SphaeroX/optimistic-hubble/.agents/swe_1/DISPATCH.md

## 2026-08-21T17:47:13Z

You are the SWE Light orchestrator for the task defined in ORIGINAL_REQUEST.md.

Project root: c:\Users\MGasc\Documents\antigravity\optimistic-hubble
Original request file: c:\Users\MGasc\Documents\antigravity\optimistic-hubble\.agents\ORIGINAL_REQUEST.md
Your working directory: c:\Users\MGasc\Documents\antigravity\optimistic-hubble\.agents\swe_1

Read ORIGINAL_REQUEST.md and execute the SWE Light implementation and review loop to fix the Android Wi-Fi SoftAP connection lifecycle, socket binding, and recording synchronization issue between Flutter and ESP32 SoftAP. Ensure all acceptance criteria are met and verified.

When complete, write your handoff.md and send a completion message back with your final summary.
