SphaeroX/optimistic-hubble/.agents/swe_1/progress.md

# Progress Tracking

## Iteration Status
Current iteration: 6 / 32

## Current Status
Last visited: 2026-08-21T20:11:15+02:00
- [x] Implementer pass (teamwork_preview_implementer - 139cbbd2-75ac-4e21-a6cd-302e5dc0f8cb completed)
- [x] Reviewer round 1 (teamwork_preview_reviewer - 05e17a85-e970-4b02-85ed-ecea45a1d87e completed)
- [x] Reviewer round 2 (teamwork_preview_reviewer - f65f6cd9-f0e1-40d8-a784-cee9b6a79a19 completed)
- [x] Reviewer round 3 (teamwork_preview_reviewer - c275563a-5b87-41f8-9933-3ed2bfb61a50 completed)
- [x] Orchestrator independent test verification (flutter analyze: 0 issues, flutter test: 10/10 passed, assembleDebug: BUILD SUCCESSFUL)
- [x] Victory audit (teamwork_preview_victory_auditor - 6c1af6c4-f39e-444e-9d3a-9c039cb8fe52 VICTORY CONFIRMED)
- [x] Handoff and completion reporting (swe_1/handoff.md written)

## Open Issues Ledger
- [x] Concurrency state transitions & atomic deferred binding (resolved in reviewer_3)
- [x] HTTP Range RFC 7233 206 vs 200 resume streaming (resolved in reviewer_3)
- [x] OkHttp socket/response leaks on error codes (resolved in reviewer_2)
- [x] Cooperative stream cancellation & clean event handling (resolved in reviewer_2)
- [x] NetworkCallback handle leaks on onLost/onUnavailable (resolved in reviewer_1)
- [x] SoftAP connection retention across batch transfers (resolved in implementer_1)
- [ ] Bench testing with live ESP32-C3 hardware running SoftAP firmware (hardware-dependent benchmark)
