SphaeroX/optimistic-hubble/.agents/teamwork_preview_victory_auditor_sentinel/progress.md

# Progress Log — Victory Auditor Sentinel

**Status**: Completed  
**Last visited**: 2026-08-21T18:14:30Z

## Completed Steps
- [x] Recorded inbound dispatch prompt in DISPATCH.md
- [x] Initialized and updated BRIEFING.md
- [x] Phase A: Timeline & Provenance Audit (verified commits, iterative progression, lack of pre-populated results)
- [x] Phase B: Integrity Check & Forensic Analysis (verified genuine socket routing, callback retention, batch sync lifecycle, absence of facade/cheating patterns)
- [x] Phase C: Independent Test & Build Verification (`flutter analyze` -> 0 issues, `flutter test` -> 10/10 pass, `.\gradlew.bat assembleDebug` -> SUCCESS, `flutter build apk --debug` -> SUCCESS)
- [x] Rendered structured VICTORY AUDIT REPORT in handoff.md
