SphaeroX/optimistic-hubble/.agents/implementer_1/handoff.md

# Implementer Handoff Report

> [!WARNING] **Skepticism Disclaimer**
> The implementation compiles cleanly against Android Gradle (assembleDebug) and Flutter tests/analyzer, but physical Wi-Fi SoftAP switching behavior on diverse real Android OEM devices (e.g., Samsung/Xiaomi captive portal assistants) requires live hardware validation.

## 1. What I changed
- **`apps/companion_app/android/app/src/main/kotlin/com/sphaerox/companion_app/network/IotWifiManager.kt`**:
  - Removed premature callback unregistration on `awaitClose` in `connectToEsp32SoftAp()`.
  - Added thread-safe `suspend fun connect()`, `isConnected()`, and `getActiveNetwork()` methods.
  - Retained `NetworkCallback` and `bindProcessToNetwork` throughout transfer sessions until explicit `disconnect()`.
  - Added connection deduplication to reuse active network without repeated dialog prompts.
- **`apps/companion_app/android/app/src/main/kotlin/com/sphaerox/companion_app/network/IotHttpClientFactory.kt`**:
  - Enhanced OkHttpClient factory to accept optional `Network` and bound socket factories exclusively to the IoT Wi-Fi interface.
  - Added local DNS resolution bypass for `192.168.4.1` and `xiao.local`.
- **`apps/companion_app/android/app/src/main/kotlin/com/sphaerox/companion_app/MainActivity.kt`**:
  - Added MethodChannel handlers for `connectWifiSoftAp`, `disconnectWifiSoftAp`, `isWifiConnected`, and enhanced `startWifiSoftApSync` with `keepConnected` flag.
  - Reused active Wi-Fi session across clip downloads without tearing down the connection between transfers.
- **`apps/companion_app/android/app/src/main/kotlin/com/sphaerox/companion_app/service/AudioSyncForegroundService.kt`**:
  - Refactored Tier 2 Wi-Fi SoftAP sync to use suspend `connect()` and guaranteed cleanup in `finally`.
- **`apps/companion_app/lib/core/services/native_audio_sync_bridge.dart`**:
  - Added `connectWifiSoftAp`, `disconnectWifiSoftAp`, `isWifiConnected`, and `keepConnected` parameter support.
- **`apps/companion_app/lib/features/recordings/services/recording_sync_manager.dart`**:
  - Refactored `syncAllClips()` to start ESP32 Wi-Fi and pre-connect native SoftAP once for the batch session.
  - Kept Wi-Fi alive (`keepWifiAlive: true`) across all unsynced clips during "Adaptive Sync All".
  - Cleaned up Wi-Fi connection and ESP32 hotspot in `finally` and added `cancelSync()`.
- **`apps/companion_app/test/hybrid_sync_test.dart`**:
  - Added unit tests for NativeAudioSyncBridge methods and failed/cancelled sync progress events.

## 2. Why
- Consuming Kotlin Flow via `.first()` immediately terminated the flow collector, causing `awaitClose { disconnect() }` to unregister the `NetworkCallback` and unbind the network before or during HTTP transfer.
- Batch syncing was initiating and tearing down Wi-Fi specifier connections per file, causing system dialog spam and connection thrashing.
- Explicit socket routing via `IotHttpClientFactory` and `bindProcessToNetwork` ensures HTTP requests never fall back to cellular WAN.

## 3. Verification Record
- **Deep Verification (ran actual tests):**
  - Ran `flutter analyze` in `apps/companion_app` (0 warnings, 0 errors).
  - Ran `flutter test` in `apps/companion_app` (8/8 tests passed including `adpcm_test`, `hybrid_sync_test`, and `widget_test`).
  - Ran `./gradlew assembleDebug` with JDK 21 (build succeeded cleanly in 21s).
- **Shallow Verification (manual run only):**
  - None (all code verified through automated compiler and test suites).
- **Unverified aspects:**
  - Physical interaction with physical XIAO ESP32-C3 hardware running SoftAP firmware.
  - OEM-specific Android aggressive captive-portal disconnections (e.g. MIUI/OneUI specific auto-reconnect prompts).

## 4. Known Issues
- `Minor Robustness Risk`: On some custom OEM Android skins (e.g., MIUI), no-internet Wi-Fi networks may prompt a system notification asking "Keep connected?"; if dismissed, OS may disconnect.

## 5. Untested Edge Cases & Next Step
- Reviewer should test batch sync with 5+ recordings against live ESP32-C3 hardware to verify throughput (>1.8 MB/s) and smooth teardown after completion.
