SphaeroX/optimistic-hubble/.agents/teamwork_preview_orchestrator_1/plan.md

# Plan: Research & Architectural Study — Optimal IoT-to-Android Audio Sync (XIAO ESP32-C3)

## Objective
Deliver an exhaustive, publication-grade, and actionable technical research document (`research/iot_android_transfer_study.md`) detailing protocols, benchmarks, comparative matrices, hybrid architecture, and production-ready Android Kotlin + ESP32-C3 firmware reference designs for seamless audio synchronization (0.5MB - 16MB @ 8 KB/s ADPCM).

## Phase 1: Deep Technical Survey & Exploration (Parallel Explorers)
- **Explorer 1 (BLE 5.0 Throughput & Market Analysis)**:
  - Deep-dive into BLE 5.0 PHY (1M vs 2M PHY), Data Length Extension (DLE / 251 bytes), ATT MTU negotiation (512 bytes), L2CAP Connection-Oriented Channels (CoC) vs GATT Notifications.
  - Physical vs effective throughput on ESP32-C3 (NimBLE / ESP-IDF) and Android Bluetooth stack (Fluoride / Gabeldorsche).
  - Commercial analysis of Plaud Note AI, Senstone, Mobvoi, and audio wearables (reverse engineering transfer modes, BLE handshake + Wi-Fi SoftAP trigger).
- **Explorer 2 (Android OS 10–15 / API 29–35+ Networking & Background Execution)**:
  - `WifiNetworkSpecifier.Builder` and `NetworkRequest` lifecycle.
  - `CompanionDeviceManager` (CDM) association and automatic device pairing.
  - Multi-network socket binding via `Network.bindSocket()` / `Network.openConnection()` to preserve cellular LTE/5G internet while communicating with local ESP32 SoftAP.
  - Android 12-15 background constraints: Foreground Service types (`dataSync`, `connectedDevice`), `WorkManager` expedited jobs, Doze mode whitelist, exact alarm permissions, runtime BLE permissions (`BLUETOOTH_SCAN`, `BLUETOOTH_CONNECT` with `neverForLocation`).
- **Explorer 3 (ESP32-C3 Firmware Architecture & Sync Protocol)**:
  - Coexistence of BLE 5.0 and Wi-Fi on ESP32-C3 (single RF chain, time-division multiplexing).
  - Dual-mode state machine: low-power BLE advertising/sleep vs high-speed Wi-Fi AP / STA burst.
  - Chunk streaming, CRC32 verification, resume/offset recovery protocol, LittleFS / external SPI Flash (W25Q128) streaming performance.

## Phase 2: Synthesis & Deliverable Compilation (Worker)
- Dispatch Worker to write `research/iot_android_transfer_study.md` covering:
  - Executive Summary & System Overview.
  - R1: State-of-the-Art & Protocol Deep-Dive (4 transfer methods + Plaud Note case study).
  - R2: Quantitative & Qualitative Benchmark Evaluation (Mathematical transfer time models, power profiling, UX friction analysis, Android API 29-35+ permission matrix).
  - R3: Optimal Architecture & Hybrid Strategy Definition (Zero-friction Primary Method, Background Sync vs Foreground On-Open Sync, Resilient Chunked Protocol with CRC32 & Offset Resume).
  - R4: Actionable Implementation Blueprint & Reference Code (Mermaid sequence diagrams, ESP32-C3 NimBLE/ESP-IDF firmware blueprint, Android Kotlin production implementation with Coroutines, Flow, WorkManager, WifiNetworkSpecifier, Multi-network binding).

## Phase 3: Adversarial Review & Verification
- Reviewer 1: Technical & Protocol Accuracy Review.
- Reviewer 2: Android Kotlin & OS Permission Compliance Review (API 29-35+).
- Challenger: Quantitative benchmark verification & edge-case stress testing.
- Forensic Auditor: Integrity & completeness check against all acceptance criteria.

## Phase 4: Sign-off & Delivery
- Synthesize reviews into `GATE_STATUS.md`.
- Ensure deliverable at `research/iot_android_transfer_study.md` is complete and verified.
- Report completion to parent agent.
