SphaeroX/optimistic-hubble/.agents/teamwork_preview_orchestrator_1/progress.md

# Progress

## Current Status
Last visited: 2026-08-20T13:54:55Z

## Iteration Status
Current iteration: 2 / 32

## Checklist
- [x] Initialized orchestrator workspace metadata (BRIEFING.md, plan.md, context.md, DISPATCH.md, PROJECT.md)
- [x] Phase 1: Dispatch Explorers for parallel deep technical research
  - [x] Explorer 1: BLE 5.0 Throughput (2M PHY, DLE, L2CAP CoC vs GATT) & Market Analysis — Complete
  - [x] Explorer 2: Android 10-15 Networking & Background execution — Complete
  - [x] Explorer 3: ESP32-C3 Firmware Architecture & Sync Protocol — Complete
- [x] Phase 2: Dispatch Worker 1 to compile initial study — Complete
- [x] Phase 3 (Iteration 1): Review panel identified 8 specific code refinements
- [x] Phase 3 (Iteration 2 Remediation): Worker 2 applied all 8 code hardening fixes
- [x] Phase 3 (Iteration 2 Verification):
  - [x] Reviewer 3 (0b439aba-4f2f-464b-80d6-3728eb40a02a): APPROVE
  - [x] Challenger 3 (4686c1ac-9bdb-4aab-ad5b-3cd2bd38899d): APPROVE
  - [x] Auditor 2 (91c80f33-50ca-43d1-af60-840e1b9f7fdb): CLEAN (0 integrity violations, 100% acceptance criteria)
- [x] Phase 4: Sign-off & delivery to parent
