SphaeroX/optimistic-hubble/.agents/auditor_1/handoff.md

# Independent Victory Audit Handoff Report

## 1. Observation
- **Git Timeline & Provenance**:
  - `dab73e5` (Reviewer 3): Synchronized network callback lifecycle, prevented orphaned deferreds, and resolved HTTP Range partial stream handling.
  - `101125f` (Reviewer 2): Resolved race conditions in SoftAP callback, closed OkHttp response leaks, and added cooperative cancellation.
  - `5eaf591` (Reviewer 1): Prevented NetworkCallback leaks, optimized batch sync, and harmonized destination paths.
  - `b9e5e6b` (Implementer 1): Retained Wi-Fi SoftAP connection and optimized batch sync lifecycle.
- **Forensic Source Inspection**:
  - `IotWifiManager.kt`: Replaced premature Flow unregistration on `awaitClose` with suspend `connect()`, internal `connectionDeferred` protected under `synchronized(stateLock)`, atomic process network binding, and guarded `onLost`/`onUnavailable` handlers.
  - `IotHttpClientFactory.kt`: OkHttpClient explicitly uses `iotNetwork.socketFactory` and local DNS bypass for `192.168.4.1` / `xiao.local` to prevent WAN cellular fallback.
  - `MainActivity.kt`: Reuses active Wi-Fi session across clip transfers, supports `keepConnected: true`, enforces cooperative cancellation via `if (!isActive) throw CancellationException()`, handles RFC 7233 206 Partial Content vs 200 OK branching, and ensures OkHttp `Response.use` disposal.
  - `recording_sync_manager.dart`: Refactored `syncAllClips()` to trigger Wi-Fi hotspot once and pre-connect native SoftAP session once for the entire batch, passing `keepWifiAlive: true` across all unsynced clips and tearing down connection in `finally`. Streams 206 chunks directly to disk (`openWrite`).
  - `hybrid_sync_test.dart`: Contains comprehensive test coverage across model tier classification, sync progress event lifecycle, platform fallback safety, HTTP Range offset calculation, and model mutations.
- **Independent Execution Commands**:
  - `flutter analyze` in `apps/companion_app`: Exited with code 0 (`No issues found!`).
  - `flutter test` in `apps/companion_app`: Exited with code 0 (`10/10 tests passed`).
  - `cmd /c "set JAVA_HOME=C:\Program Files\Java\jdk-21& gradlew.bat assembleDebug"` in `apps/companion_app/android`: Exited with code 0 (`BUILD SUCCESSFUL in 11s`, 182 actionable tasks).

## 2. Logic Chain
1. *Observation*: Consuming `connectToEsp32SoftAp` via Kotlin Flow `.first()` previously caused `awaitClose { disconnect() }` to immediately unregister the Android `NetworkCallback`.
2. *Deduction*: Refactoring `IotWifiManager` to maintain `activeCallback` and `activeNetwork` across transfers and delegating session lifecycle to explicit `connect()` / `disconnect()` calls directly fixes R1.
3. *Observation*: `IotHttpClientFactory` binds the `OkHttpClient` socket factory directly to the IoT Wi-Fi `Network` instance and overrides DNS lookup.
4. *Deduction*: This prevents Android OS cellular data routing or captive-portal health-check failures from interfering with local ESP32 SoftAP communications, satisfying R2.
5. *Observation*: `recording_sync_manager.dart` pre-connects the Wi-Fi SoftAP and signals the BLE Hotspot once at the batch level (`syncAllClips()`), passing `keepWifiAlive: true` during single clip syncs.
6. *Deduction*: This eliminates connection thrashing, reduces per-clip overhead, and ensures cleanup in `finally`, satisfying R3.
7. *Observation*: Independent execution of static analyzer, unit test suite, and native Android compiler produced zero errors and matched claimed test results.

## 3. Caveats
- Real hardware validation with physical XIAO ESP32-C3 hardware running SoftAP firmware is necessary to measure physical over-the-air throughput (>1.8 MB/s) and observe OEM-specific captive-portal prompt suppression on specialized OEM Android skins (e.g. Xiaomi MIUI / Samsung OneUI).

## 4. Conclusion
All requirements (R1, R2, R3) and acceptance criteria have been rigorously implemented, hardened against race conditions, and independently verified against compilers and test suites.

## 5. Verification Method
- Independent static analysis: `flutter analyze` in `apps/companion_app` -> 0 issues.
- Independent test suite: `flutter test` in `apps/companion_app` -> 10/10 passed.
- Independent native build: `gradlew.bat assembleDebug` with JDK 21 in `apps/companion_app/android` -> BUILD SUCCESSFUL.

---

=== VICTORY AUDIT REPORT ===

VERDICT: VICTORY CONFIRMED

PHASE A — TIMELINE:
  Result: PASS
  Anomalies: none (chronological git commits demonstrate iterative implementation, review hardening, and test expansion)

PHASE B — INTEGRITY CHECK:
  Result: PASS
  Details: Development mode integrity verified. Genuine implementation in Kotlin and Dart without facades, hardcoded returns, or fabricated result artifacts. All code comments and identifiers adhere to English standards.

PHASE C — INDEPENDENT TEST EXECUTION:
  Test command: flutter analyze ; flutter test ; gradlew assembleDebug
  Your results:
    - flutter analyze: 0 issues found (clean)
    - flutter test: 10/10 passed
    - gradlew assembleDebug: BUILD SUCCESSFUL in 11s (182 actionable tasks)
  Claimed results:
    - flutter analyze: 0 issues
    - flutter test: 10/10 passed
    - gradlew assembleDebug: BUILD SUCCESSFUL
  Match: YES

EVIDENCE (if REJECTED):
  N/A (VICTORY CONFIRMED)
