SphaeroX/optimistic-hubble/.agents/auditor_1/progress.md

# Progress Log

Last visited: 2026-08-21T20:11:00Z

- Phase A Completed: Timeline & Provenance verified cleanly across git history.
- Phase B Completed: Forensic integrity check passed (no facades, no hardcoded results, authentic implementation, clean English identifiers).
- Phase C Completed: Independent verification executed:
  - `flutter analyze`: 0 issues (clean)
  - `flutter test`: 10/10 tests passed
  - `gradlew assembleDebug`: BUILD SUCCESSFUL (11s)
- Generating final victory audit report in `handoff.md`.
