SphaeroX/optimistic-hubble/.agents/swe_1/BRIEFING.md

# BRIEFING — 2026-08-21T20:11:10+02:00

## Mission
Orchestrate SWE Light implementation and review loop to fix Android Wi-Fi SoftAP connection lifecycle, socket binding, and recording synchronization issue between Flutter and ESP32 SoftAP.

## 🔒 My Identity
- Archetype: orchestrator
- Roles: orchestrator, user_liaison, human_reporter, successor
- Working directory: c:\Users\MGasc\Documents\antigravity\optimistic-hubble\.agents\swe_1
- Original parent: parent
- Original parent conversation ID: d583ac53-1910-40fd-b3bc-9f7e1f49c882

## 🔒 My Workflow
- **Pattern**: SWE Light
- **Scope document**: c:\Users\MGasc\Documents\antigravity\optimistic-hubble\.agents\ORIGINAL_REQUEST.md
1. **Decompose**: SWE Light does not decompose; each worker receives full task verbatim.
2. **Dispatch & Execute**:
   - Implementer: teamwork_preview_implementer (completed)
   - Reviewers: teamwork_preview_reviewer (R1 completed, R2 completed, R3 completed)
   - Victory Auditor: teamwork_preview_victory_auditor (completed)
3. **On failure**: Retry -> Replace -> Skip -> Redistribute -> Redesign -> Escalate
4. **Succession**: Self-succeed when spawn count >= 16 and all subagents complete.
- **Work items**:
  1. Implementer pass [done]
  2. Reviewer round 1 [done]
  3. Reviewer round 2 [done]
  4. Reviewer round 3 [done]
  5. Victory audit [done]
- **Current phase**: 4
- **Current focus**: Complete

## 🔒 Key Constraints
- NEVER write, modify, or create source code files yourself. Delegate all implementation and repair.
- NEVER explore or debug codebase to solve task yourself.
- Dispatch sequentially. Pass original task verbatim.
- Maintain open-issues ledger across all rounds.
- Run at least 3 review rounds, verify tests personally, and pass victory audit.
- Never reuse a subagent after it has delivered its handoff.

## Current Parent
- Conversation ID: d583ac53-1910-40fd-b3bc-9f7e1f49c882
- Updated: 2026-08-21T19:47:20+02:00

## Key Decisions Made
- Initialized SWE Light orchestrator workflow.
- Dispatched Implementer 1 (139cbbd2-75ac-4e21-a6cd-302e5dc0f8cb) - completed.
- Dispatched Reviewer 1 (05e17a85-e970-4b02-85ed-ecea45a1d87e) - completed.
- Dispatched Reviewer 2 (f65f6cd9-f0e1-40d8-a784-cee9b6a79a19) - completed.
- Dispatched Reviewer 3 (c275563a-5b87-41f8-9933-3ed2bfb61a50) - completed.
- Personally re-ran flutter analyze (passed), flutter test (10/10 passed), and gradlew assembleDebug (passed).
- Dispatched Victory Auditor (6c1af6c4-f39e-444e-9d3a-9c039cb8fe52) - VICTORY CONFIRMED.
- Wrote final handoff report at `c:\Users\MGasc\Documents\antigravity\optimistic-hubble\.agents\swe_1\handoff.md`.

## Team Roster
| Agent | Type | Work Item | Status | Conv ID |
|---|---|---|---|---|
| Implementer_1 | teamwork_preview_implementer | Implementer pass | completed | 139cbbd2-75ac-4e21-a6cd-302e5dc0f8cb |
| Reviewer_1 | teamwork_preview_reviewer | Review round 1 | completed | 05e17a85-e970-4b02-85ed-ecea45a1d87e |
| Reviewer_2 | teamwork_preview_reviewer | Review round 2 | completed | f65f6cd9-f0e1-40d8-a784-cee9b6a79a19 |
| Reviewer_3 | teamwork_preview_reviewer | Review round 3 | completed | c275563a-5b87-41f8-9933-3ed2bfb61a50 |
| Auditor_1 | teamwork_preview_victory_auditor | Independent Victory Audit | completed | 6c1af6c4-f39e-444e-9d3a-9c039cb8fe52 |

## Succession Status
- Succession required: no
- Spawn count: 5 / 16
- Pending subagents: none
- Predecessor: none
- Successor: not yet spawned

## Active Timers
- Heartbeat cron: not started
- Safety timer: none

## Artifact Index
- c:\Users\MGasc\Documents\antigravity\optimistic-hubble\.agents\ORIGINAL_REQUEST.md — Original task requirements
- c:\Users\MGasc\Documents\antigravity\optimistic-hubble\.agents\swe_1\DISPATCH.md — Orchestrator dispatch log
- c:\Users\MGasc\Documents\antigravity\optimistic-hubble\.agents\swe_1\handoff.md — Orchestrator handoff report
- c:\Users\MGasc\Documents\antigravity\optimistic-hubble\.agents\implementer_1\handoff.md — Implementer handoff
- c:\Users\MGasc\Documents\antigravity\optimistic-hubble\.agents\reviewer_1\handoff.md — Reviewer 1 handoff
- c:\Users\MGasc\Documents\antigravity\optimistic-hubble\.agents\reviewer_2\handoff.md — Reviewer 2 handoff
- c:\Users\MGasc\Documents\antigravity\optimistic-hubble\.agents\reviewer_3\handoff.md — Reviewer 3 handoff
- c:\Users\MGasc\Documents\antigravity\optimistic-hubble\.agents\auditor_1\handoff.md — Victory Audit Report
