SphaeroX/optimistic-hubble/.agents/swe_1/handoff.md

# Orchestrator Handoff Report

## 1. Observation
- The Android Wi-Fi SoftAP connection lifecycle, socket binding, and recording synchronization issue between Flutter and ESP32 MCU SoftAP has been resolved and refined across 1 implementation pass, 3 adversarial review rounds, and 1 independent victory audit.
- **Key Changes Implemented**:
  - `IotWifiManager.kt`: Replaced premature Flow unregistration on `awaitClose` with thread-safe `suspend fun connect()`, `disconnect()`, and `getActiveNetwork()`. All state transitions (`connectionDeferred`, `activeCallback`, `activeNetwork`) are synchronized under `stateLock`. Process-to-network binding (`bindProcessToNetwork`) and callback unregistration are atomic and guarded against stale/late callback events.
  - `IotHttpClientFactory.kt`: OkHttpClient explicitly uses `iotNetwork.socketFactory` and bypasses external DNS queries for `192.168.4.1` and `xiao.local`, guaranteeing that local SoftAP traffic never falls back to cellular WAN.
  - `MainActivity.kt`: Reuses active Wi-Fi sessions across clip transfers, supports `keepConnected: true`, enforces cooperative cancellation (`isActive`), handles RFC 7233 206 vs 200 HTTP Range response branching, guarantees OkHttp `Response.use` socket disposal, and supports custom `destinationPath`.
  - `recording_sync_manager.dart` & `native_audio_sync_bridge.dart`: Refactored `syncAllClips()` to trigger Wi-Fi hotspot once and pre-connect native SoftAP session once for the entire batch session. Passed `keepWifiAlive: true` across individual clip transfers and cleaned up the Wi-Fi connection in `finally`. Streams HTTP chunks directly to disk (`openWrite`).
  - `hybrid_sync_test.dart`: Expanded unit tests covering Tier 1 vs Tier 2 adaptive thresholds, SyncProgressEvent lifecycle, HTTP Range 206 vs 200 resume math, platform fallback safety, and model mutations.

## 2. Logic Chain
- Prior to these changes, `connectToEsp32SoftAp.first()` immediately triggered `awaitClose { disconnect() }`, unregistering the `NetworkCallback` and unbinding the network before HTTP requests could complete.
- Retaining the callback and network binding until explicit session completion or cancellation ensures persistent, uninterrupted local MCU communication.
- Binding OkHttp sockets directly to the dedicated IoT Wi-Fi interface prevents cellular data fallback or captive-portal validation failures on Android 10+.
- Reusing the SoftAP connection across clips during batch sync ("Adaptive Sync All") eliminates system Wi-Fi dialog thrashing, removes redundant 1.5s per-clip BLE delays, and optimizes transfer speed.

## 3. Milestone State
- **Implementer Pass**: Completed (139cbbd2-75ac-4e21-a6cd-302e5dc0f8cb)
- **Reviewer Round 1**: Completed (05e17a85-e970-4b02-85ed-ecea45a1d87e)
- **Reviewer Round 2**: Completed (f65f6cd9-f0e1-40d8-a784-cee9b6a79a19)
- **Reviewer Round 3**: Completed (c275563a-5b87-41f8-9933-3ed2bfb61a50)
- **Independent Test Verification**: Completed by Orchestrator
- **Independent Victory Audit**: Completed & VICTORY CONFIRMED (6c1af6c4-f39e-444e-9d3a-9c039cb8fe52)

## 4. Verification Method & Test Results
- `flutter analyze` in `apps/companion_app`: **0 issues found (clean)**.
- `flutter test` in `apps/companion_app`: **10/10 tests passed**.
- Native Gradle build `.\gradlew.bat assembleDebug` in `apps/companion_app/android`: **BUILD SUCCESSFUL in 11s (182 actionable tasks, 0 compiler errors)**.
- Independent Victory Auditor Verdict: **VICTORY CONFIRMED**.

## 5. Active Subagents & Team Roster
- Implementer: `139cbbd2-75ac-4e21-a6cd-302e5dc0f8cb` (Completed)
- Reviewer 1: `05e17a85-e970-4b02-85ed-ecea45a1d87e` (Completed)
- Reviewer 2: `f65f6cd9-f0e1-40d8-a784-cee9b6a79a19` (Completed)
- Reviewer 3: `c275563a-5b87-41f8-9933-3ed2bfb61a50` (Completed)
- Victory Auditor: `6c1af6c4-f39e-444e-9d3a-9c039cb8fe52` (Completed)
- All subagents are retired and complete.

## 6. Pending Decisions & Caveats
- None pending for software implementation. Real-hardware validation with physical XIAO ESP32-C3 hardware running SoftAP firmware can be performed as next step to observe live OTA throughput (>1.8 MB/s).

## 7. Key Artifacts
- `c:\Users\MGasc\Documents\antigravity\optimistic-hubble\.agents\ORIGINAL_REQUEST.md` — Original Task Specification
- `c:\Users\MGasc\Documents\antigravity\optimistic-hubble\.agents\swe_1\BRIEFING.md` — Orchestrator Briefing
- `c:\Users\MGasc\Documents\antigravity\optimistic-hubble\.agents\swe_1\progress.md` — Progress & Open Issues Ledger
- `c:\Users\MGasc\Documents\antigravity\optimistic-hubble\.agents\implementer_1\handoff.md` — Implementer Report
- `c:\Users\MGasc\Documents\antigravity\optimistic-hubble\.agents\reviewer_1\handoff.md` — Reviewer 1 Report
- `c:\Users\MGasc\Documents\antigravity\optimistic-hubble\.agents\reviewer_2\handoff.md` — Reviewer 2 Report
- `c:\Users\MGasc\Documents\antigravity\optimistic-hubble\.agents\reviewer_3\handoff.md` — Reviewer 3 Report
- `c:\Users\MGasc\Documents\antigravity\optimistic-hubble\.agents\auditor_1\handoff.md` — Victory Audit Report
