SphaeroX/optimistic-hubble/.agents/teamwork_preview_victory_auditor_sentinel/BRIEFING.md

# BRIEFING — 2026-08-21T18:14:35Z

## Mission
Independent Victory Audit of the Android Wi-Fi SoftAP connection lifecycle, socket routing, and batch sync implementation against ORIGINAL_REQUEST.md.

## 🔒 My Identity
- Archetype: victory_auditor
- Roles: [critic, specialist, auditor, victory_verifier]
- Working directory: c:\Users\MGasc\Documents\antigravity\optimistic-hubble\.agents\teamwork_preview_victory_auditor_sentinel
- Original parent: d583ac53-1910-40fd-b3bc-9f7e1f49c882
- Target: full project

## 🔒 Key Constraints
- Audit-only — do NOT modify implementation code
- Trust NOTHING — verify everything independently
- Integrity Mode: development (from ORIGINAL_REQUEST.md)
- Follow Phase A (Timeline & Provenance), Phase B (Integrity Check), Phase C (Independent Test Execution)

## Current Parent
- Conversation ID: d583ac53-1910-40fd-b3bc-9f7e1f49c882
- Updated: 2026-08-21T18:14:35Z

## Audit Scope
- **Work product**: Android native Wi-Fi manager (`IotWifiManager.kt`, `MainActivity.kt`, `IotHttpClientFactory.kt`), Flutter sync manager & bridge (`recording_sync_manager.dart`, `native_audio_sync_bridge.dart`), and unit tests.
- **Profile loaded**: General Project / Victory Audit
- **Audit type**: victory audit

## Audit Progress
- **Phase**: completed
- **Checks completed**: [DISPATCH recorded, BRIEFING initialized, Phase A: Timeline & Provenance PASS, Phase B: Forensic Integrity PASS, Phase C: Independent Test & Build PASS, handoff.md generated]
- **Checks remaining**: []
- **Findings so far**: CLEAN — VICTORY CONFIRMED

## Key Decisions Made
- Confirmed genuine, non-facade implementation across native Android Kotlin and Flutter Dart code.
- Confirmed clean builds (`flutter analyze`, `flutter test`, `gradlew assembleDebug`, `flutter build apk --debug`).

## Artifact Index
- `.agents/teamwork_preview_victory_auditor_sentinel/DISPATCH.md` — Inbound dispatch record
- `.agents/teamwork_preview_victory_auditor_sentinel/BRIEFING.md` — Persistent memory
- `.agents/teamwork_preview_victory_auditor_sentinel/progress.md` — Liveness & heartbeat
- `.agents/teamwork_preview_victory_auditor_sentinel/handoff.md` — Final audit handoff report

## Attack Surface
- **Hypotheses tested**: Premature Flow unregistration, cellular data fallback, socket leakage, unhandled HTTP Range 200 vs 206 responses, batch sync reconnection thrashing.
- **Vulnerabilities found**: None remaining after the review iterations.
- **Untested angles**: Hardware-in-the-loop physical RF attenuation (software-side handles timeouts and reconnections gracefully).

## Loaded Skills
- None required
