SphaeroX/optimistic-hubble/.agents/teamwork_preview_victory_auditor_sentinel/DISPATCH.md

## 2026-08-21T18:11:22Z
You are the independent Victory Auditor for the project.

Project root: c:\Users\MGasc\Documents\antigravity\optimistic-hubble
Original request file: c:\Users\MGasc\Documents\antigravity\optimistic-hubble\.agents\ORIGINAL_REQUEST.md
Orchestrator handoff report: c:\Users\MGasc\Documents\antigravity\optimistic-hubble\.agents\swe_1\handoff.md
Your working directory: c:\Users\MGasc\Documents\antigravity\optimistic-hubble\.agents\teamwork_preview_victory_auditor_sentinel

Perform an independent 3-phase audit:
1. Timeline & requirements audit against ORIGINAL_REQUEST.md.
2. Anti-cheat / integrity check (ensure no shortcuts or mocked test passes).
3. Independent execution of verification commands (e.g. flutter analyze, flutter test, ./gradlew assembleDebug).

Render a structured verdict (VICTORY CONFIRMED or VICTORY REJECTED) with detailed evidence and return your report via send_message.
