SphaeroX/optimistic-hubble/.agents/teamwork_preview_auditor_2/BRIEFING.md

# BRIEFING — 2026-08-20T13:54:00Z

## Mission
Conduct exhaustive final forensic integrity audit of the research report `research/iot_android_transfer_study.md` against all user constraints in `ORIGINAL_REQUEST.md`.

## 🔒 My Identity
- Archetype: forensic_auditor
- Roles: critic, specialist, auditor
- Working directory: c:\Users\MGasc\Documents\antigravity\optimistic-hubble\.agents\teamwork_preview_auditor_2
- Original parent: ff5b3206-dca0-46f5-be4f-e7353b2157c6
- Target: full project (research/iot_android_transfer_study.md)

## 🔒 Key Constraints
- Audit-only — do NOT modify implementation code
- Trust NOTHING — verify everything independently
- Strict forensic analysis for hardcoded mocks, facade implementations, fabricated results, and integrity violations
- Cross-check all 8 Acceptance Criteria from ORIGINAL_REQUEST.md

## Current Parent
- Conversation ID: ff5b3206-dca0-46f5-be4f-e7353b2157c6
- Updated: 2026-08-20T13:54:00Z

## Audit Scope
- **Work product**: `research/iot_android_transfer_study.md` (2,034 lines, 106.8 KB)
- **Profile loaded**: General Project (Development Mode per ORIGINAL_REQUEST.md)
- **Audit type**: forensic integrity check

## Audit Progress
- **Phase**: reporting (Completed)
- **Checks completed**:
  - Phase 1: Mode-Agnostic Forensic Verification (Passed)
  - Phase 2: Mode-Specific Flagging & Acceptance Criteria Cross-Check (8/8 Passed)
  - Mathematical and airtime derivation verification (Passed)
  - Binary framing and unpack loop simulation (Passed)
  - Adversarial challenge remediation checks (Passed)
  - audit_report.md and handoff.md generation (Completed)
- **Checks remaining**: None
- **Findings so far**: CLEAN

## Key Decisions Made
- Confirmed verdict: CLEAN.
- Generated audit_report.md and handoff.md with empirical proof.

## Artifact Index
- `.agents/teamwork_preview_auditor_2/DISPATCH.md` — Inbound dispatch instructions
- `.agents/teamwork_preview_auditor_2/BRIEFING.md` — Situational awareness
- `.agents/teamwork_preview_auditor_2/progress.md` — Progress and liveness
- `.agents/teamwork_preview_auditor_2/verify_study.py` — Mathematical validation script
- `.agents/teamwork_preview_auditor_2/test_l2cap_stream.py` — Binary stream simulation script
- `.agents/teamwork_preview_auditor_2/audit_report.md` — Full forensic audit report
- `.agents/teamwork_preview_auditor_2/handoff.md` — Handoff report with binary verdict

## Attack Surface
- **Hypotheses tested**:
  1. 32-byte header parsing with `ByteBuffer` -> Verified passing without underflow.
  2. Stream chunk corruption & resume append -> Verified passing with append mode and whole-file CRC32.
  3. WorkManager Android 14/15 FGS compliance -> Verified passing with `setForeground` and `connectedDevice`.
  4. SoftAP power watchdog -> Verified passing with 60s connect / 30s idle timeout.
  5. DMA I2S timing -> Verified passing with DMA self-clocking.
- **Vulnerabilities found**: 0 unaddressed vulnerabilities.
- **Untested angles**: None.

## Loaded Skills
- None.
