SphaeroX/optimistic-hubble/.agents/teamwork_preview_auditor_2/DISPATCH.md

## 2026-08-20T13:49:31Z
You are Auditor 2 (Final Forensic Integrity Auditor) for the Research & Architectural Study: Optimal IoT-to-Android Audio Sync (XIAO ESP32-C3).

Your working directory is: c:\Users\MGasc\Documents\antigravity\optimistic-hubble\.agents\teamwork_preview_auditor_2
The user requirements are in: c:\Users\MGasc\Documents\antigravity\optimistic-hubble\ORIGINAL_REQUEST.md
The updated deliverable is in: c:\Users\MGasc\Documents\antigravity\optimistic-hubble\research\iot_android_transfer_study.md

You MUST read ORIGINAL_REQUEST.md and research/iot_android_transfer_study.md.

Perform exhaustive final forensic integrity auditing:
1. Verify that all sections, tables, mathematical proofs, Mermaid sequence diagrams, firmware blueprints, and Android Kotlin reference codes are 100% genuine, authentic, and free of dummy/mock shortcuts.
2. Cross-check all 8 Acceptance Criteria from ORIGINAL_REQUEST.md:
   - [ ] Comprehensive analysis of at least 4 transfer methods (BLE 5.0 High-Throughput, Android WifiNetworkSpecifier SoftAP, Station Mode LAN sync, Hybrid).
   - [ ] Concrete throughput benchmarks and transfer time calculations specifically tailored to 8 KB/s ADPCM audio files (0.5 MB to 16 MB).
   - [ ] Detailed analysis of Android 12-15 background constraints, foreground service types (dataSync, connectedDevice), and battery optimization policies.
   - [ ] In-depth breakdown of Plaud Note AI / commercial audio recorder transfer mechanisms.
   - [ ] Clear comparative trade-off matrix with scoring for speed, UX friction, power, and complexity.
   - [ ] Mermaid sequence diagrams for both Foreground On-Open Sync and Silent Background Sync.
   - [ ] Ready-to-use architecture blueprint with ESP32-C3 firmware outline and Android Kotlin reference code.
   - [ ] Deliver all findings in a comprehensive, structured markdown report in the working directory research/iot_android_transfer_study.md.

Write your audit report to `.agents/teamwork_preview_auditor_2/audit_report.md` and binary verdict (CLEAN / INTEGRITY VIOLATION) in `.agents/teamwork_preview_auditor_2/handoff.md`.
Communicate your verdict to parent via send_message.
