SphaeroX/optimistic-hubble/.agents/teamwork_preview_orchestrator_1/BRIEFING.md

# BRIEFING — 2026-08-20T13:54:50Z

## Mission
Orchestrate technical research, benchmark evaluation, trade-off matrix, architecture blueprint, and Android Kotlin + ESP32-C3 firmware reference designs for optimal IoT-to-Android audio sync (8 KB/s ADPCM audio files, 0.5MB-16MB) without manual Wi-Fi switching, delivering `research/iot_android_transfer_study.md`.

## 🔒 My Identity
- Archetype: teamwork_preview_orchestrator
- Roles: orchestrator, user_liaison, human_reporter, successor
- Working directory: c:\Users\MGasc\Documents\antigravity\optimistic-hubble\.agents\teamwork_preview_orchestrator_1
- Original parent: parent
- Original parent conversation ID: 8e5fa4f8-cedf-4fa6-873e-433905a0217f

## 🔒 My Workflow
- **Pattern**: Project Orchestrator
- **Scope document**: c:\Users\MGasc\Documents\antigravity\optimistic-hubble\PROJECT.md
1. **Decompose**:
   - Phase 1: Exploration & Technical Research (3 parallel Explorers — Complete).
   - Phase 2: Synthesis & Deliverable Creation (Worker 1 & Worker 2 — Complete).
   - Phase 3: Adversarial Review & Verification (Iteration 1 & Iteration 2 — Complete, Gate PASS).
   - Phase 4: Sign-off & Delivery.
2. **Dispatch & Execute**:
   - Direct delegation to subagents per pattern.
3. **On failure**:
   - Retry -> Replace -> Skip -> Redistribute -> Redesign
4. **Succession**:
   - Succession threshold: 16 spawns.

## 🔒 Key Constraints
- Never write source code / final deliverable directly as orchestrator (dispatch-only).
- Maintain rigorous mathematical and empirical accuracy on throughput, power, battery life, transfer times for 8 KB/s ADPCM (0.5MB - 16MB).
- Strict adherence to Android 10-15 (API 29-35+) constraints, permissions, ForegroundService types (`connectedDevice`, `dataSync`), CompanionDeviceManager, and WifiNetworkSpecifier socket binding.
- Output deliverable path: `c:\Users\MGasc\Documents\antigravity\optimistic-hubble\research\iot_android_transfer_study.md`.

## Current Parent
- Conversation ID: 8e5fa4f8-cedf-4fa6-873e-433905a0217f
- Updated: 2026-08-20T13:38:00Z

## Key Decisions Made
- All milestones M1 through M5 completed and verified.
- Gate status: PASS (Auditor: CLEAN, Reviewer: APPROVE, Challenger: APPROVE).

## Team Roster
| Agent | Type | Work Item | Status | Conv ID |
|---|---|---|---|---|
| explorer_1 | teamwork_preview_explorer | BLE 5.0 Throughput & Market Analysis | completed | 0cd0aaa9-88d2-438c-9ccd-3a03f86e1930 |
| explorer_2 | teamwork_preview_explorer | Android 10-15 Networking & Background | completed | 4fc5bf8c-5dc7-4f91-ac1c-1bc243606945 |
| explorer_3 | teamwork_preview_explorer | ESP32-C3 Firmware & Recovery Protocol | completed | 0f4afa59-f48f-442d-aafd-73494f2a6127 |
| worker_1 | teamwork_preview_worker | Master Technical Study Compiler | completed | 343be365-dbe5-49fc-8af2-d334c73403d3 |
| reviewer_1 | teamwork_preview_reviewer | Technical & Protocol Reviewer | completed (APPROVE) | a0e8c67a-3fb6-46d4-9869-d4c057340581 |
| reviewer_2 | teamwork_preview_reviewer | Android & Firmware Reviewer | completed (REQUEST_CHANGES) | a7c4a8dc-d9bf-42c4-bfd3-c107fe62f95b |
| challenger_1 | teamwork_preview_challenger | Mathematical & Benchmark Challenger | completed (APPROVE) | 1e67dff6-3e61-4f30-bf39-a2cf7acbae93 |
| challenger_2 | teamwork_preview_challenger | Protocol Stress Challenger | completed (REQUEST_CHANGES) | a6aaaa7b-db30-4652-82b1-91a726c91075 |
| auditor_1 | teamwork_preview_auditor | Forensic Integrity Auditor | completed (CLEAN) | d9006a47-a668-4083-a4ff-e52d5edd4445 |
| worker_2 | teamwork_preview_worker | Deliverable Refinement & Code Hardening | completed | d83996e2-d8c0-4812-b3c2-3825923589ad |
| reviewer_3 | teamwork_preview_reviewer | Re-Verification Reviewer | completed (APPROVE) | 0b439aba-4f2f-464b-80d6-3728eb40a02a |
| challenger_3 | teamwork_preview_challenger | Re-Verification Challenger | completed (APPROVE) | 4686c1ac-9bdb-4aab-ad5b-3cd2bd38899d |
| auditor_2 | teamwork_preview_auditor | Final Forensic Auditor | completed (CLEAN) | 91c80f33-50ca-43d1-af60-840e1b9f7fdb |

## Succession Status
- Succession required: no
- Spawn count: 13 / 16
- Pending subagents: none
- Predecessor: none
- Successor: not yet spawned

## Active Timers
- Heartbeat cron: killed
- Safety timer: none

## Artifact Index
- `ORIGINAL_REQUEST.md` — User requirements & specifications
- `PROJECT.md` — Decomposition, milestones, feature inventory
- `research/iot_android_transfer_study.md` — Final verified deliverable
