SphaeroX/optimistic-hubble/.agents/teamwork_preview_orchestrator_1/DISPATCH.md

## 2026-08-20T13:37:34Z
You are the Project Orchestrator for the Research & Architectural Study: Optimal IoT-to-Android Audio Sync (XIAO ESP32-C3).

Your working directory is: c:\Users\MGasc\Documents\antigravity\optimistic-hubble\.agents\teamwork_preview_orchestrator_1
The workspace root is: c:\Users\MGasc\Documents\antigravity\optimistic-hubble
The verbatim user requirements are stored in: c:\Users\MGasc\Documents\antigravity\optimistic-hubble\ORIGINAL_REQUEST.md

Your mission is to orchestrate and execute the complete technical research, benchmark evaluation, trade-off matrix, architecture blueprint, and Android Kotlin + ESP32-C3 firmware reference designs according to ORIGINAL_REQUEST.md.

The final comprehensive deliverable must be written to:
c:\Users\MGasc\Documents\antigravity\optimistic-hubble\research\iot_android_transfer_study.md

Please follow standard orchestration workflows:
1. Initialize your plan.md, context.md, and progress.md in your working directory.
2. Formulate a detailed multi-phase plan addressing R1 (State-of-the-art protocols, BLE 5.0 2M PHY/DLE/L2CAP, WifiNetworkSpecifier/CompanionDeviceManager, Station Mode mDNS, Plaud Note / commercial analysis), R2 (benchmarks, transfer times for 8 KB/s ADPCM audio files 0.5MB-16MB, UX friction, Android API 29-35+ restrictions, power, complexity), R3 (optimal primary architecture, hybrid strategy, foreground & background sync modes, CRC/resume recovery), and R4 (actionable blueprint, Mermaid diagrams, ESP32-C3 firmware architecture, Kotlin reference implementation).
3. Dispatch specialized subagents to perform web research, codebase analysis of the existing project if relevant, benchmarking analysis, architectural design, and document drafting.
4. Verify all acceptance criteria are met in research/iot_android_transfer_study.md.
5. Update progress.md regularly and send a completion message when finished.
