SphaeroX/optimistic-hubble/.agents/teamwork_preview_orchestrator_1/GATE_STATUS.md

# Gate Status — Iteration 2 (Final)

## Panel Verdicts
| Agent | Role | Verdict | Source | Notes |
|---|---|---|---|---|
| auditor_2 | teamwork_preview_auditor | CLEAN | handoff.md | 0 integrity violations, 100% acceptance criteria satisfied |
| reviewer_3 | teamwork_preview_reviewer | APPROVE | handoff.md | All 8 findings from Reviewer 2 fully resolved with zero shortcuts |
| challenger_3 | teamwork_preview_challenger | APPROVE | handoff.md | Automated stress tests verify 32-byte header, resume append, FGS compliance, watchdog |
| reviewer_1 | teamwork_preview_reviewer | APPROVE | handoff.md | Verified protocol analysis, market study, and trade-off matrix |
| challenger_1 | teamwork_preview_challenger | APPROVE | handoff.md | Verified mathematical models, airtimes, transfer times, battery longevity |

Gate Result: **PASS**
