SphaeroX/optimistic-hubble/.agents/teamwork_preview_orchestrator_1/handoff.md

# Orchestrator Handoff Report

**Project**: Optimal IoT-to-Android Audio Sync (XIAO ESP32-C3)  
**Deliverable**: `research/iot_android_transfer_study.md` (2,034 lines, 106.8 KB)  
**Orchestrator**: `teamwork_preview_orchestrator_1`  
**Date**: 2026-08-20  
**Handoff Type**: Hard (Task Complete)

---

## 1. Milestone State
- **M1 (Protocol Deep-Dive & Survey)**: DONE (BLE 5.0 2M PHY/DLE/L2CAP, Android WifiNetworkSpecifier/CompanionDeviceManager, multi-network cellular data preservation, Wi-Fi STA mDNS, Plaud Note reverse-engineering).
- **M2 (Benchmarks & Trade-Off Matrix)**: DONE (Throughput tables, 8 KB/s IMA-ADPCM models for 1m/5m/10m/35m, UX friction matrix, Android 10-15 permission matrix, 150/300 mAh LiPo battery models with energy crossover at 4.21 MB, multi-attribute decision matrix).
- **M3 (Architecture & Recovery Protocol)**: DONE (Tier 1 Silent BLE < 2MB, Tier 2 Dynamic SoftAP >= 2MB, Tier 3 Docked LAN STA, Modes A/B/C, 32-byte chunk framing & RFC 7233 Range resume).
- **M4 (Sequence Diagrams & Reference Code)**: DONE (4 Mermaid sequence diagrams, FreeRTOS DMA ring buffer & RFC 7233 C++ firmware, NimBLE L2CAP server C++, production Kotlin code for `IotWifiManager`, `IotHttpClientFactory`, `BleL2capAudioReceiver`, `AudioSyncForegroundService`, `AudioSyncWorker`, and `AndroidManifest.xml`).
- **M5 (Synthesis & Final Review Gate)**: DONE (Gate Result: PASS; Auditor: CLEAN, Reviewer: APPROVE, Challenger: APPROVE).

---

## 2. Active Subagents
- All 13 subagents across exploration, drafting, review, challenge, and forensic audit phases have finished execution.

---

## 3. Pending Decisions
- None. All architectural decisions, mathematical models, and code blueprints are fully resolved and unanimously approved.

---

## 4. Key Artifacts
- **Primary Deliverable**: `c:\Users\MGasc\Documents\antigravity\optimistic-hubble\research\iot_android_transfer_study.md`
- **Scope & Milestones**: `c:\Users\MGasc\Documents\antigravity\optimistic-hubble\PROJECT.md`
- **Orchestrator State**:
  - `c:\Users\MGasc\Documents\antigravity\optimistic-hubble\.agents\teamwork_preview_orchestrator_1\BRIEFING.md`
  - `c:\Users\MGasc\Documents\antigravity\optimistic-hubble\.agents\teamwork_preview_orchestrator_1\progress.md`
  - `c:\Users\MGasc\Documents\antigravity\optimistic-hubble\.agents\teamwork_preview_orchestrator_1\GATE_STATUS.md`
- **Automated Validation Test Harness**: `c:\Users\MGasc\Documents\antigravity\optimistic-hubble\tests\test_all_dimensions.py`

---

## 5. Verification Summary
- **Auditor Verdict**: CLEAN (0 integrity violations, 100% acceptance criteria satisfied).
- **Reviewer Verdict**: APPROVE (All technical findings and Android 14/15 constraints verified).
- **Challenger Verdict**: APPROVE (Frame airtimes, throughput bounds, and crash recovery stress-tested).
