SphaeroX/optimistic-hubble/.agents/teamwork_preview_reviewer_2/review.md

# Review Report: Research & Architectural Study — Optimal IoT-to-Android Audio Sync (XIAO ESP32-C3)

**Reviewer:** Reviewer 2 (Android & Firmware Implementation Reviewer)  
**Target Document:** `research/iot_android_transfer_study.md`  
**Working Directory:** `.agents/teamwork_preview_reviewer_2`  
**Date:** 2026-08-20  
**Verdict:** **REQUEST_CHANGES**

---

## 1. Executive Summary

The architectural study `research/iot_android_transfer_study.md` is an exceptionally well-researched, mathematically rigorous, and comprehensive technical document. The theoretical derivations (airtime modeling, RF coexistence analysis, energy crossover points, Linux multi-network policy routing) and architectural strategy (Tiered Adaptive Hybrid Engine) are outstanding.

However, an exhaustive adversarial review of the **implementation blueprints and reference code** revealed two **Critical** findings (including a fatal `BufferUnderflowException` in the L2CAP packet parser and a dummy `delay(4000)` implementation in the foreground service), three **Major** findings (WorkManager lifecycle decoupling, omitted WebServer header collection breaking HTTP Range resume, and missing NimBLE L2CAP C++ firmware code), and three **Minor** findings.

Because of the integrity violation (dummy implementation) and runtime crashes in the reference code, the verdict is **REQUEST_CHANGES**.

---

## 2. Findings Matrix

| Finding ID | Severity | Category | Target Location | Summary Description |
|---|---|---|---|---|
| **CRIT-01** | **Critical** | Runtime Crash / Bug | `research/iot_android_transfer_study.md` (Lines 665-679, 1187-1216) | **BufferUnderflowException**: Header struct is 32 bytes, but parser allocates 30 bytes, crashing on `expectedFileCrc32`. |
| **CRIT-02** | **Critical** | Integrity / Dummy Code | `AudioSyncForegroundService.kt` (Line 1317) | **Dummy Simulation**: Foreground service contains `delay(4000)` instead of executing real audio synchronization. |
| **MAJ-01** | **Major** | Architecture / Android OS | `AudioSyncWorker.kt` (Lines 1392-1404) | **Premature Worker Completion**: Worker fire-and-forgets service and returns `Result.success()`, releasing wakelocks early. |
| **MAJ-02** | **Major** | Firmware / Protocol | `wifi_server_range.cpp` (Lines 905-941) | **Silent Range Resume Failure**: Arduino `WebServer` requires `server.collectHeaders("Range")`; without it, `hasHeader("Range")` is always false. |
| **MAJ-03** | **Major** | Firmware Completeness | Section 5.2 (ESP32-C3 Firmware Blueprint) | **Missing NimBLE L2CAP C++ Blueprint**: No C++ reference code provided for ESP32 NimBLE L2CAP CoC server. |
| **MIN-01** | **Minor** | Android OS Compliance | Section 5.3 (Android Reference Guide) | **Missing Manifest Blueprint**: Android 14/15 `FOREGROUND_SERVICE_CONNECTED_DEVICE` manifest declarations not provided. |
| **MIN-02** | **Minor** | Robustness / Stream IO | `BleL2capAudioReceiver.kt` (Lines 1220-1239) | **Unhandled Partial Read on EOF**: Premature socket close writes truncated payload bytes without aborting. |
| **MIN-03** | **Minor** | Firmware Robustness | `audio_ringbuffer_engine.cpp` (Lines 873-892) | **Missing EOF Buffer Flush**: Trailing audio (< 512 bytes) remains unflushed in `sector_buffer` on recording completion. |

---

## 3. Detailed Findings & Root-Cause Analysis

### CRIT-01 [Critical]: `BufferUnderflowException` in `BleL2capAudioReceiver.kt` & 30 vs 32-Byte Header Sizing Mismatch
- **Location:** `research/iot_android_transfer_study.md`, Section 4.3.1 (lines 665–679) & Section 5.3.3 (lines 1187–1216).
- **Root Cause:**
  In Section 4.3.1, `struct SyncChunkHeader` is specified with 11 fields:
  1. `magic`: `uint16_t` (2 bytes)
  2. `version`: `uint8_t` (1 byte)
  3. `frameType`: `uint8_t` (1 byte)
  4. `fileId`: `uint32_t` (4 bytes)
  5. `sequenceNum`: `uint32_t` (4 bytes)
  6. `byteOffset`: `uint32_t` (4 bytes)
  7. `payloadLength`: `uint16_t` (2 bytes)
  8. `reserved`: `uint16_t` (2 bytes)
  9. `totalFileSize`: `uint32_t` (4 bytes)
  10. `chunkCrc32`: `uint32_t` (4 bytes)
  11. `fileCrc32`: `uint32_t` (4 bytes)
  
  $$\text{Total Struct Size} = 2 + 1 + 1 + 4 + 4 + 4 + 2 + 2 + 4 + 4 + 4 = \mathbf{32 \text{ Bytes}}$$

  However, throughout the document (lines 637, 760, 1182, 1187, 1190, 1193, 1198), it is labeled as **"30-Byte Header"**.
  In `BleL2capAudioReceiver.kt`:
  ```kotlin
  val headerBuffer = ByteBuffer.allocate(30).order(ByteOrder.LITTLE_ENDIAN)
  // ... reads 30 bytes from socket ...
  val magic = headerBuffer.short              // pos: 2
  val version = headerBuffer.get()            // pos: 3
  val frameType = headerBuffer.get()          // pos: 4
  val fileId = headerBuffer.int               // pos: 8
  val seqNum = headerBuffer.int               // pos: 12
  val byteOffset = headerBuffer.int           // pos: 16
  val payloadLen = headerBuffer.short         // pos: 18
  val reserved = headerBuffer.short           // pos: 20
  val totalFileSize = headerBuffer.int        // pos: 24
  val chunkCrc32 = headerBuffer.int           // pos: 28
  val expectedFileCrc32 = headerBuffer.int    // pos: 32 -> THROWS java.nio.BufferUnderflowException!
  ```
- **Impact:** The receiver crashes immediately upon receiving the first audio chunk, rendering Tier 1 BLE L2CAP streaming completely inoperable.
- **Remediation:** Update the specification and Kotlin code to use `32` bytes (`ByteBuffer.allocate(32)`, `32 - headerBytesRead`).

---

### CRIT-02 [Critical]: Dummy / Facade Implementation in `AudioSyncForegroundService.kt`
- **Location:** `research/iot_android_transfer_study.md`, Section 5.3.4 (lines 1314–1324).
- **Observation:**
  ```kotlin
  serviceScope.launch {
      try {
          // Perform BLE L2CAP or Wi-Fi sync execution
          delay(4000)
      } catch (e: Exception) {
          Log.e(TAG, "Sync error: ${e.message}", e)
      } finally {
          stopForeground(STOP_FOREGROUND_REMOVE)
          stopSelf()
      }
  }
  ```
- **Root Cause & Violation:** Instead of invoking `BleL2capAudioReceiver` or `IotWifiManager` / `IotHttpClientFactory`, the foreground service contains a hardcoded dummy delay (`delay(4000)`). Under team integrity rules, dummy or facade implementations that look complete but contain mock logic must be flagged as an integrity finding.
- **Remediation:** Implement the actual sync dispatch logic inside `AudioSyncForegroundService.kt` that resolves pending recordings from BLE metadata, selects the appropriate tier (L2CAP vs SoftAP), streams the payload, updates notification progress, and verifies CRC32.

---

### MAJ-01 [Major]: WorkManager Lifecycle Decoupling & Premature Worker Completion in `AudioSyncWorker.kt`
- **Location:** `research/iot_android_transfer_study.md`, Section 5.3.5 (lines 1392–1404).
- **Root Cause:**
  `AudioSyncWorker.doWork()` calls `AudioSyncForegroundService.start(applicationContext)` and immediately returns `Result.success()`.
- **Impact:**
  1. Once `doWork()` returns, WorkManager considers the background task complete and immediately releases the OS execution wake-locks.
  2. On Android 12+ (API 31+), calling `startForegroundService()` from the background is restricted and throws `ForegroundServiceStartNotAllowedException` unless the worker itself is running as an Expedited Work Request with `setForeground(ForegroundInfo(...))`.
  3. The OS can kill the service process before the peripheral connection is negotiated.
- **Remediation:** Convert `AudioSyncWorker` to use `setForeground(createForegroundInfo())` directly, or have the worker suspend until the synchronization operation completes before returning `Result.success()`.

---

### MAJ-02 [Major]: Missing `collectHeaders` in ESP32 WebServer (`wifi_server_range.cpp`)
- **Location:** `research/iot_android_transfer_study.md`, Section 5.2.2 (lines 905–941).
- **Root Cause:**
  In Arduino ESP32 `WebServer`, request headers are not parsed or stored by default. To access the HTTP `Range` header via `server.hasHeader("Range")` and `server.header("Range")`, the developer must register the header in `setup()`:
  ```cpp
  const char* header_keys[] = {"Range", "Accept-Ranges"};
  server.collectHeaders(header_keys, 2);
  ```
- **Impact:** Without `server.collectHeaders()`, `server.hasHeader("Range")` silently returns `false` on every request. Resumed transfers will restart from byte 0, corrupting partial downloads and wasting Wi-Fi airtime and battery.
- **Remediation:** Add `server.collectHeaders(header_keys, 2)` to the WebServer initialization blueprint.

---

### MAJ-03 [Major]: Missing ESP32 NimBLE L2CAP CoC / GATT Server C++ Implementation
- **Location:** `research/iot_android_transfer_study.md`, Section 5.2.
- **Observation:** Section 5.2 provides C++ code for FreeRTOS ring-buffer (`audio_ringbuffer_engine.cpp`) and WebServer HTTP Range (`wifi_server_range.cpp`), but contains no C++ code snippet for the ESP32 NimBLE L2CAP CoC server (PSM registration, `ble_l2cap_create_server`, connection event callbacks, MTU/MPS sizing, and credit management).
- **Impact:** Firmware developers lack the concrete NimBLE API calls required to establish the L2CAP CoC channel on ESP-IDF / Arduino ESP32.
- **Remediation:** Provide a complete C++ reference implementation (`nimble_l2cap_server.cpp`) demonstrating NimBLE L2CAP CoC server registration and data transmission.

---

### MIN-01 [Minor]: Missing `AndroidManifest.xml` Blueprint
- **Location:** Section 5.3.
- **Observation:** While permissions and FGS types are discussed in the text, the actual XML manifest block declaring `FOREGROUND_SERVICE_CONNECTED_DEVICE`, `BLUETOOTH_CONNECT`, `BLUETOOTH_SCAN`, `NEARBY_WIFI_DEVICES`, and service metadata is missing.
- **Remediation:** Add a complete `AndroidManifest.xml` snippet illustrating API 29–35+ declarations.

---

### MIN-02 [Minor]: Unhandled Partial Reads on EOF in `BleL2capAudioReceiver.kt`
- **Location:** Section 5.3.3, lines 1220–1239.
- **Observation:** If the socket closes mid-payload (`read == -1`), `payloadBytesRead` is `< payloadLen`. The code continues to write truncated data and compute CRC without checking if `payloadBytesRead == payloadLen`.
- **Remediation:** Check `if (payloadBytesRead < payloadLen) throw IOException("Premature EOF during payload read")`.

---

### MIN-03 [Minor]: Missing Flush Mechanism in `audio_ringbuffer_engine.cpp`
- **Location:** Section 5.2.1, lines 873–892.
- **Observation:** `StorageWriterTask` only writes to Flash when `buffer_fill >= 512`. When recording ends, up to 511 trailing bytes will remain in `sector_buffer` and will not be saved.
- **Remediation:** Add a flush event or timeout check to write remaining `buffer_fill` bytes upon recording termination.

---

## 4. Verified Claims & Theoretical Validation

The following architectural claims and derivations were independently verified and found to be **100% mathematically and technically sound**:

1. **LE 2M PHY Airtime & Throughput Limits (Section 2.1.1):**
   - Transmit airtime for DLE 251B: $T_{\text{TX}} = 8.0 + 16.0 + 8.0 + 1004.0 + 16.0 + 12.0 = 1,064.0 \text{ µs}$.
   - Cycle time: $1064.0 + 150.0 + 40.0 + 150.0 = 1,404.0 \text{ µs}$.
   - Max theoretical packet rate: $\approx 712.25 \text{ pkts/sec}$.
   - L2CAP CoC Net Throughput (247B payload): $712.25 \times 247 \text{ B} = \mathbf{175.93 \text{ KB/s}}$. **Verified.**

2. **Energy Crossover Derivation (Section 3.5.2):**
   - Energy BLE: $18.2 \text{ mA} \times (S / 125) / 3600 = 0.0404 \cdot S \text{ mAh/MB}$.
   - Energy Wi-Fi: $[135 \text{ mA} \times (S / 1800) + (85 \text{ mA} \times 3.5 \text{ s})] / 3600 = 0.0208 \cdot S + 0.0826 \text{ mAh}$.
   - Equating: $0.0196 \cdot S = 0.0826 \implies S_{\text{cross}} = \mathbf{4.21 \text{ MB}} \ (\approx 8.7 \text{ min audio})$. **Verified.**

3. **Multi-Network Socket Isolation (Section 2.3 & 5.3.2):**
   - `OkHttpClient.Builder().socketFactory(iotNetwork.socketFactory)` correctly binds only the IoT client sockets via Linux `SO_BINDTODEVICE` / `fwmark`, leaving default process routing on cellular 5G/LTE unimpeded. **Verified.**

4. **`IotWifiManager.kt` CallbackFlow Mechanics (Section 5.3.1):**
   - Correctly constructs `WifiNetworkSpecifier` and `NetworkRequest` with `removeCapability(NetworkCapabilities.NET_CAPABILITY_INTERNET)`.
   - Properly cleans up via `awaitClose { disconnect() }`. **Verified.**

---

## 5. Recommended Code Fixes & Remediation Blueprints

### Fix 1: Corrected `BleL2capAudioReceiver.kt` (32-Byte Header + Robust IO)
```kotlin
package com.xiao.audiosync.ble

import android.bluetooth.BluetoothDevice
import android.bluetooth.BluetoothSocket
import android.content.Context
import android.os.Build
import android.util.Log
import androidx.annotation.RequiresApi
import kotlinx.coroutines.Dispatchers
import kotlinx.coroutines.withContext
import java.io.File
import java.io.FileOutputStream
import java.io.IOException
import java.io.InputStream
import java.nio.ByteBuffer
import java.nio.ByteOrder
import java.util.zip.CRC32

class BleL2capAudioReceiver(private val context: Context) {

    private var l2capSocket: BluetoothSocket? = null

    @RequiresApi(Build.VERSION_CODES.Q)
    suspend fun receiveAudioViaL2cap(
        device: BluetoothDevice,
        psm: Int = 0x0081,
        outputFile: File,
        onProgress: (bytesReceived: Long, totalBytes: Long) -> Unit
    ): Boolean = withContext(Dispatchers.IO) {
        var fileOutputStream: FileOutputStream? = null
        try {
            Log.i(TAG, "Opening L2CAP Channel to PSM: 0x${psm.toString(16)} on ${device.address}")
            l2capSocket = device.createInsecureL2capChannel(psm)
            l2capSocket?.connect()

            val inputStream: InputStream = l2capSocket?.inputStream 
                ?: throw IOException("Failed to obtain L2CAP socket input stream")
            fileOutputStream = FileOutputStream(outputFile)

            val fileCrc = CRC32()
            var totalBytesExpected = 0L
            var totalBytesReceived = 0L
            // FIXED: Header size is exactly 32 bytes
            val headerBuffer = ByteBuffer.allocate(32).order(ByteOrder.LITTLE_ENDIAN)

            while (l2capSocket?.isConnected == true) {
                // 1. Read exactly 32 bytes for SyncChunkHeader
                var headerBytesRead = 0
                headerBuffer.clear()
                while (headerBytesRead < 32) {
                    val read = inputStream.read(headerBuffer.array(), headerBytesRead, 32 - headerBytesRead)
                    if (read == -1) break
                    headerBytesRead += read
                }
                if (headerBytesRead == 0) break // Clean EOF
                if (headerBytesRead < 32) throw IOException("Incomplete header received ($headerBytesRead/32 bytes)")

                headerBuffer.position(0)
                val magic = headerBuffer.short.toInt() and 0xFFFF
                if (magic != 0xAA55) {
                    throw IOException("Invalid magic in chunk header: 0x${magic.toString(16)}")
                }

                val version = headerBuffer.get()
                val frameType = headerBuffer.get()
                val fileId = headerBuffer.int
                val seqNum = headerBuffer.int
                val byteOffset = headerBuffer.int
                val payloadLen = headerBuffer.short.toInt() and 0xFFFF
                val reserved = headerBuffer.short
                val totalFileSize = headerBuffer.int.toLong() and 0xFFFFFFFFL
                val chunkCrc32 = headerBuffer.int.toLong() and 0xFFFFFFFFL
                val expectedFileCrc32 = headerBuffer.int.toLong() and 0xFFFFFFFFL

                totalBytesExpected = totalFileSize

                if (frameType == 0x05) { // FIN frame
                    Log.i(TAG, "Received FIN frame from peripheral")
                    break
                }

                // 2. Read exactly payloadLen binary bytes
                var payloadBytesRead = 0
                val payload = ByteArray(payloadLen)
                while (payloadBytesRead < payloadLen) {
                    val read = inputStream.read(payload, payloadBytesRead, payloadLen - payloadBytesRead)
                    if (read == -1) throw IOException("Premature EOF during payload read")
                    payloadBytesRead += read
                }

                // 3. Verify chunk CRC32
                val chunkCrc = CRC32()
                chunkCrc.update(payload, 0, payloadBytesRead)
                if (chunkCrc.value != chunkCrc32) {
                    throw IOException("Chunk CRC32 mismatch on sequence $seqNum (calc=0x${chunkCrc.value.toString(16)}, exp=0x${chunkCrc32.toString(16)})")
                }

                fileOutputStream.write(payload, 0, payloadBytesRead)
                fileCrc.update(payload, 0, payloadBytesRead)
                totalBytesReceived += payloadBytesRead

                onProgress(totalBytesReceived, totalBytesExpected)

                if (totalBytesReceived >= totalBytesExpected) {
                    if (fileCrc.value != expectedFileCrc32) {
                        throw IOException("File CRC32 verification failed!")
                    }
                    Log.i(TAG, "File CRC32 (0x${fileCrc.value.toString(16)}) verified successfully!")
                    break
                }
            }

            fileOutputStream.flush()
            return@withContext true
        } catch (e: Exception) {
            Log.e(TAG, "L2CAP Sync Exception: ${e.message}", e)
            return@withContext false
        } finally {
            try { fileOutputStream?.close() } catch (_: Exception) {}
            try { l2capSocket?.close() } catch (_: Exception) {}
            l2capSocket = null
        }
    }

    companion object {
        private const val TAG = "BleL2capAudioReceiver"
    }
}
```

---

### Fix 2: Corrected `AudioSyncForegroundService.kt` (Real Sync Orchestration)
```kotlin
package com.xiao.audiosync.service

import android.app.Notification
import android.app.NotificationChannel
import android.app.NotificationManager
import android.app.Service
import android.bluetooth.BluetoothAdapter
import android.bluetooth.BluetoothManager
import android.content.Context
import android.content.Intent
import android.content.pm.ServiceInfo
import android.os.Build
import android.os.IBinder
import android.util.Log
import androidx.core.app.NotificationCompat
import androidx.core.app.ServiceCompat
import com.xiao.audiosync.ble.BleL2capAudioReceiver
import kotlinx.coroutines.*
import java.io.File

class AudioSyncForegroundService : Service() {

    private val serviceScope = CoroutineScope(Dispatchers.IO + SupervisorJob())
    private lateinit var notificationManager: NotificationManager

    override fun onBind(intent: Intent?): IBinder? = null

    override fun onCreate() {
        super.onCreate()
        notificationManager = getSystemService(Context.NOTIFICATION_SERVICE) as NotificationManager
        createNotificationChannel()
    }

    override fun onStartCommand(intent: Intent?, flags: Int, startId: Int): Int {
        val deviceAddress = intent?.getStringExtra(EXTRA_DEVICE_ADDRESS)
        val initialNotification = buildProgressNotification("Connecting to XIAO ESP32-C3...", 0, 100)

        if (Build.VERSION.SDK_INT >= Build.VERSION_CODES.UPSIDE_DOWN_CAKE) {
            ServiceCompat.startForeground(
                this,
                NOTIFICATION_ID,
                initialNotification,
                ServiceInfo.FOREGROUND_SERVICE_TYPE_CONNECTED_DEVICE
            )
        } else {
            startForeground(NOTIFICATION_ID, initialNotification)
        }

        if (deviceAddress.isNullOrEmpty()) {
            Log.e(TAG, "No device address provided. Stopping service.")
            stopSelf()
            return START_NOT_STICKY
        }

        serviceScope.launch {
            try {
                val btManager = getSystemService(Context.BLUETOOTH_SERVICE) as BluetoothManager
                val device = btManager.adapter.getRemoteDevice(deviceAddress)
                val targetFile = File(filesDir, "audio_${System.currentTimeMillis()}.adpcm")
                val receiver = BleL2capAudioReceiver(applicationContext)

                val success = receiver.receiveAudioViaL2cap(
                    device = device,
                    psm = 0x0081,
                    outputFile = targetFile
                ) { bytesReceived, totalBytes ->
                    val percent = if (totalBytes > 0) ((bytesReceived * 100) / totalBytes).toInt() else 0
                    notificationManager.notify(
                        NOTIFICATION_ID,
                        buildProgressNotification("Downloading audio: $percent%", percent, 100)
                    )
                }

                if (success) {
                    Log.i(TAG, "Audio sync completed successfully: ${targetFile.absolutePath}")
                } else {
                    Log.e(TAG, "Audio sync failed.")
                }
            } catch (e: Exception) {
                Log.e(TAG, "Fatal sync error: ${e.message}", e)
            } finally {
                stopForeground(STOP_FOREGROUND_REMOVE)
                stopSelf()
            }
        }

        return START_NOT_STICKY
    }

    private fun createNotificationChannel() {
        if (Build.VERSION.SDK_INT >= Build.VERSION_CODES.O) {
            val channel = NotificationChannel(
                CHANNEL_ID,
                "Audio Sync Service",
                NotificationManager.IMPORTANCE_LOW
            ).apply {
                description = "Shows ongoing transfer progress with XIAO recorder"
            }
            notificationManager.createNotificationChannel(channel)
        }
    }

    private fun buildProgressNotification(content: String, progress: Int, max: Int): Notification {
        return NotificationCompat.Builder(this, CHANNEL_ID)
            .setContentTitle("XIAO Voice Sync")
            .setContentText(content)
            .setSmallIcon(android.R.drawable.stat_sys_download)
            .setProgress(max, progress, progress == 0)
            .setOngoing(true)
            .setPriority(NotificationCompat.PRIORITY_LOW)
            .build()
    }

    override fun onDestroy() {
        super.onDestroy()
        serviceScope.cancel()
    }

    companion object {
        private const val TAG = "AudioSyncFGService"
        private const val CHANNEL_ID = "channel_audio_sync"
        private const val NOTIFICATION_ID = 2001
        const val EXTRA_DEVICE_ADDRESS = "extra_device_address"

        fun start(context: Context, deviceAddress: String) {
            val intent = Intent(context, AudioSyncForegroundService::class.java).apply {
                putExtra(EXTRA_DEVICE_ADDRESS, deviceAddress)
            }
            if (Build.VERSION.SDK_INT >= Build.VERSION_CODES.O) {
                context.startForegroundService(intent)
            } else {
                context.startService(intent)
            }
        }
    }
}
```

---

### Fix 3: Corrected `wifi_server_range.cpp` (with `server.collectHeaders`)
```cpp
// Firmware: wifi_server_range.cpp
#include <WiFi.h>
#include <WebServer.h>
#include <LittleFS.h>
#include <esp_rom_crc.h>

WebServer server(80);

// Mandatory HTTP Header registration for Arduino ESP32 WebServer
const char* HTTP_COLLECT_HEADERS[] = {"Range", "Accept-Ranges"};
const size_t HTTP_COLLECT_HEADERS_COUNT = sizeof(HTTP_COLLECT_HEADERS) / sizeof(char*);

void setupHttpServer() {
    // CRITICAL: Without collectHeaders, server.hasHeader("Range") will ALWAYS return false!
    server.collectHeaders(HTTP_COLLECT_HEADERS, HTTP_COLLECT_HEADERS_COUNT);
    
    server.on("/api/download", HTTP_GET, handleApiDownloadRange);
    server.begin();
    Serial.println("HTTP Audio Server started with RFC 7233 Range support");
}

void handleApiDownloadRange() {
    if (!server.hasArg("id")) {
        server.send(400, "text/plain", "Missing id parameter");
        return;
    }

    String path = "/" + server.arg("id") + ".adpcm";
    if (!LittleFS.exists(path)) {
        server.send(404, "text/plain", "File not found");
        return;
    }

    File audioFile = LittleFS.open(path, "r");
    size_t totalFileSize = audioFile.size();
    size_t startByte = 0;
    size_t endByte = totalFileSize - 1;

    // Handle RFC 7233 HTTP Range Header
    if (server.hasHeader("Range")) {
        String rangeHeader = server.header("Range");
        int equalsIndex = rangeHeader.indexOf('=');
        int dashIndex = rangeHeader.indexOf('-');
        if (equalsIndex != -1 && dashIndex != -1) {
            startByte = rangeHeader.substring(equalsIndex + 1, dashIndex).toInt();
            if (dashIndex + 1 < rangeHeader.length()) {
                endByte = rangeHeader.substring(dashIndex + 1).toInt();
            }
        }
    }

    if (startByte >= totalFileSize) {
        server.sendHeader("Content-Range", "bytes */" + String(totalFileSize));
        server.send(416, "text/plain", "Requested Range Not Satisfiable");
        audioFile.close();
        return;
    }

    size_t contentLength = (endByte - startByte) + 1;
    audioFile.seek(startByte);

    server.sendHeader("Content-Type", "audio/adpcm");
    server.sendHeader("Accept-Ranges", "bytes");
    server.sendHeader("Content-Length", String(contentLength));
    if (server.hasHeader("Range")) {
        server.sendHeader("Content-Range", "bytes " + String(startByte) + "-" + String(endByte) + "/" + String(totalFileSize));
        server.send(206, "audio/adpcm", "");
    } else {
        server.send(200, "audio/adpcm", "");
    }

    uint8_t streamBuffer[2920]; // 2 x TCP MSS
    WiFiClient client = server.client();
    size_t bytesRemaining = contentLength;

    while (client.connected() && bytesRemaining > 0) {
        size_t bytesToRead = (bytesRemaining > sizeof(streamBuffer)) ? sizeof(streamBuffer) : bytesRemaining;
        size_t bytesRead = audioFile.read(streamBuffer, bytesToRead);
        if (bytesRead > 0) {
            client.write(streamBuffer, bytesRead);
            bytesRemaining -= bytesRead;
        } else {
            break;
        }
    }
    audioFile.close();
}
```

---

### Fix 4: Added NimBLE L2CAP CoC Server Blueprint (`nimble_l2cap_server.cpp`)
```cpp
// Firmware: nimble_l2cap_server.cpp
#include "nimble/nimble_port.h"
#include "nimble/nimble_port_freertos.h"
#include "host/ble_hs.h"
#include "host/ble_l2cap.h"
#include "esp_log.h"
#include "LittleFS.h"
#include <esp_rom_crc.h>

#define L2CAP_AUDIO_PSM       0x0081
#define L2CAP_COC_MTU         512
#define TAG                   "NIMBLE_L2CAP"

#pragma pack(push, 1)
struct SyncChunkHeader {
    uint16_t magic;          // 0xAA55
    uint8_t  version;        // 0x01
    uint8_t  frameType;      // 0x01=DATA, 0x05=FIN
    uint32_t fileId;         // File identifier
    uint32_t sequenceNum;    // Monotonically increasing chunk index
    uint32_t byteOffset;     // Offset in file
    uint16_t payloadLength;  // Size of payload in this chunk (bytes)
    uint16_t reserved;       // 0x0000
    uint32_t totalFileSize;  // Total file size (bytes)
    uint32_t chunkCrc32;     // CRC32 of payload
    uint32_t fileCrc32;      // Complete file CRC32
};
#pragma pack(pop)

static struct ble_l2cap_chan* s_active_coc_chan = NULL;

static int l2cap_coc_event_cb(struct ble_l2cap_event *event, void *arg) {
    switch (event->type) {
        case BLE_L2CAP_EVENT_COC_CONNECTED:
            ESP_LOGI(TAG, "L2CAP CoC Connected! Channel handle: %p, MTU: %d", 
                     event->connect.chan, event->connect.chan->scid);
            s_active_coc_chan = event->connect.chan;
            break;

        case BLE_L2CAP_EVENT_COC_DISCONNECTED:
            ESP_LOGI(TAG, "L2CAP CoC Disconnected");
            s_active_coc_chan = NULL;
            break;

        case BLE_L2CAP_EVENT_COC_ACCEPT:
            ESP_LOGI(TAG, "L2CAP CoC Connection Accept requested");
            return 0; // Accept connection

        default:
            break;
    }
    return 0;
}

void streamAudioFileOverL2cap(const char* filePath, uint32_t fileId) {
    if (!s_active_coc_chan) {
        ESP_LOGE(TAG, "Cannot stream: No active L2CAP channel");
        return;
    }

    File file = LittleFS.open(filePath, "r");
    if (!file) return;

    size_t totalSize = file.size();
    uint32_t entireFileCrc = 0; // Pre-calculated or streaming CRC

    uint8_t payloadBuffer[512];
    SyncChunkHeader header;
    header.magic = 0xAA55;
    header.version = 0x01;
    header.frameType = 0x01;
    header.fileId = fileId;
    header.totalFileSize = totalSize;
    header.fileCrc32 = entireFileCrc;
    header.reserved = 0;

    uint32_t seq = 0;
    uint32_t offset = 0;

    while (file.available() && s_active_coc_chan) {
        size_t bytesRead = file.read(payloadBuffer, sizeof(payloadBuffer));
        header.sequenceNum = seq++;
        header.byteOffset = offset;
        header.payloadLength = bytesRead;
        header.chunkCrc32 = esp_rom_crc32_le(0, payloadBuffer, bytesRead);

        struct os_mbuf *om = ble_hs_mbuf_l2cap_pkt();
        os_mbuf_append(om, &header, sizeof(header));
        os_mbuf_append(om, payloadBuffer, bytesRead);

        int rc = ble_l2cap_send(s_active_coc_chan, om);
        if (rc != 0) {
            ESP_LOGW(TAG, "L2CAP send backpressure (rc=%d)", rc);
            vTaskDelay(pdMS_TO_TICKS(10));
        }

        offset += bytesRead;
    }

    file.close();
}

void initNimbleL2capServer() {
    int rc = ble_l2cap_create_server(L2CAP_AUDIO_PSM, L2CAP_COC_MTU, l2cap_coc_event_cb, NULL);
    if (rc != 0) {
        ESP_LOGE(TAG, "Failed to create L2CAP server, rc = %d", rc);
    } else {
        ESP_LOGI(TAG, "NimBLE L2CAP CoC Server registered on PSM 0x%04X", L2CAP_AUDIO_PSM);
    }
}
```

---

### Fix 5: Added `AndroidManifest.xml` Blueprint
```xml
<!-- AndroidManifest.xml Reference Blueprint (API 29 to 35+) -->
<manifest xmlns:android="http://schemas.android.com/apk/res/android">

    <!-- BLE Permissions (Android 12+ / API 31+) -->
    <uses-permission android:name="android.permission.BLUETOOTH_SCAN"
        android:usesPermissionFlags="neverForLocation" />
    <uses-permission android:name="android.permission.BLUETOOTH_CONNECT" />

    <!-- Legacy BLE Permissions (Android 10-11 / API 29-30) -->
    <uses-permission android:name="android.permission.BLUETOOTH" android:maxSdkVersion="30" />
    <uses-permission android:name="android.permission.BLUETOOTH_ADMIN" android:maxSdkVersion="30" />
    <uses-permission android:name="android.permission.ACCESS_FINE_LOCATION" android:maxSdkVersion="30" />

    <!-- Wi-Fi & Network Permissions -->
    <uses-permission android:name="android.permission.CHANGE_NETWORK_STATE" />
    <uses-permission android:name="android.permission.ACCESS_NETWORK_STATE" />
    <uses-permission android:name="android.permission.INTERNET" />
    <uses-permission android:name="android.permission.NEARBY_WIFI_DEVICES"
        android:usesPermissionFlags="neverForLocation" />

    <!-- Foreground Service Permissions (Android 14+ / API 34+) -->
    <uses-permission android:name="android.permission.FOREGROUND_SERVICE" />
    <uses-permission android:name="android.permission.FOREGROUND_SERVICE_CONNECTED_DEVICE" />
    <uses-permission android:name="android.permission.POST_NOTIFICATIONS" />

    <application>
        <service
            android:name=".service.AudioSyncForegroundService"
            android:foregroundServiceType="connectedDevice"
            android:exported="false" />
    </application>
</manifest>
```

---

## 6. Verdict & Required Action Items

### Verdict: **REQUEST_CHANGES**

### Required Action Items for Author:
1. **[CRIT-01]** Correct the framing header struct and binary parsing size from 30 bytes to 32 bytes in `struct SyncChunkHeader`, Mermaid Diagram 2, and `BleL2capAudioReceiver.kt`.
2. **[CRIT-02]** Replace the dummy `delay(4000)` implementation in `AudioSyncForegroundService.kt` with actual invocation of `BleL2capAudioReceiver` / `IotWifiManager`.
3. **[MAJ-01]** Refactor `AudioSyncWorker.kt` so it does not prematurely terminate and decouple from the Foreground Service lifecycle.
4. **[MAJ-02]** Add `server.collectHeaders(HTTP_COLLECT_HEADERS, 2)` to `wifi_server_range.cpp`.
5. **[MAJ-03]** Add the `nimble_l2cap_server.cpp` C++ reference blueprint for ESP32 NimBLE L2CAP CoC server.
6. **[MIN-01]** Include the `AndroidManifest.xml` reference snippet in Section 5.3.
