SphaeroX/optimistic-hubble/.agents/teamwork_preview_challenger_1/BRIEFING.md

# BRIEFING — 2026-08-20T13:45:00Z

## Mission
Adversarially challenge and verify all mathematical models, frame timings, airtimes, throughput limits, audio transfer durations, power consumption equations, battery longevity projections, and energy crossover points in the IoT-to-Android audio sync research study.

## ?? My Identity
- Archetype: EMPIRICAL CHALLENGER
- Roles: critic, specialist
- Working directory: c:\Users\MGasc\Documents\antigravity\optimistic-hubble\.agents\teamwork_preview_challenger_1
- Original parent: ff5b3206-dca0-46f5-be4f-e7353b2157c6
- Milestone: Research Verification
- Instance: 1 of 1

## ?? Key Constraints
- Review-only — do NOT modify implementation/study code directly.
- Empirical rigor: write and run verification scripts to independently calculate every formula and verify all values.
- Produce challenge_report.md and handoff.md with explicit verdict (APPROVE / REQUEST_CHANGES).
- Communicate with parent agent via send_message.

## Current Parent
- Conversation ID: ff5b3206-dca0-46f5-be4f-e7353b2157c6
- Updated: 2026-08-20T13:45:00Z

## Review Scope
- **Files to review**: research/iot_android_transfer_study.md, ORIGINAL_REQUEST.md
- **Review criteria**:
  1. BLE 5.0 frame timing, airtime, PDU packing, and net throughput math
  2. Audio transfer duration & speedup calculations for 8 KB/s IMA-ADPCM files (0.48 MB, 2.40 MB, 4.80 MB, 16.80 MB)
  3. Power consumption, usable battery capacity (85% DoD), battery longevity for 150 mAh & 300 mAh LiPo batteries
  4. Energy crossover point equation and derivation
  5. Identification of any mathematical inconsistencies, unit errors, or rounding discrepancies

## Attack Surface
- **Hypotheses tested**:
  - BLE 2M airtime calculation ({TX} = 1,064 \mu s$, {cycle} = 1,404 \mu s$, max packets/s = 712.25)
  - BLE max theoretical throughputs (LL: 178.78 KB/s, L2CAP CoC: 175.93 KB/s, GATT Notify: 173.79 KB/s)
  - Audio transfer durations ({transfer} = T_{handshake} + S / v_{net}$) and speedups
  - Energy consumption models ({BLE} = 0.0404$ mAh/MB, {WiFi} = 0.0208$ mAh/MB + 0.0826 mAh setup)
  - Energy crossover equation ({cross} = 4.21$ MB)
  - Battery longevity table calculations (14.66, 56.12, 123.13 mAh/day -> days/hours for 150 mAh and 300 mAh at 85% DoD)
- **Vulnerabilities found**: TBD via empirical script execution
- **Untested angles**: Verification in progress

## Key Decisions Made
- Build a unified Python verification suite 
erify_math.py to independently compute every number and check absolute and relative errors.

## Artifact Index
- .agents/teamwork_preview_challenger_1/DISPATCH.md — Inbound instructions log
- .agents/teamwork_preview_challenger_1/BRIEFING.md — Persistent working memory
- .agents/teamwork_preview_challenger_1/progress.md — Heartbeat and progress log
- .agents/teamwork_preview_challenger_1/challenge_report.md — Detailed adversarial findings
- .agents/teamwork_preview_challenger_1/handoff.md — Final handoff report with verdict
