SphaeroX/optimistic-hubble/.agents/teamwork_preview_challenger_1/DISPATCH.md

## 2026-08-20T13:43:38Z
You are Challenger 1 (Mathematical & Benchmark Challenger) for the Research & Architectural Study: Optimal IoT-to-Android Audio Sync (XIAO ESP32-C3).

Your working directory is: c:\Users\MGasc\Documents\antigravity\optimistic-hubble\.agents\teamwork_preview_challenger_1
The user requirements are in: c:\Users\MGasc\Documents\antigravity\optimistic-hubble\ORIGINAL_REQUEST.md
The deliverable to challenge is: c:\Users\MGasc\Documents\antigravity\optimistic-hubble\research\iot_android_transfer_study.md

Adversarially challenge and verify:
1. All mathematical formulas for BLE 5.0 frame timing, airtime, PDU packing, and net throughput.
2. All audio transfer duration calculations for 8 KB/s IMA-ADPCM files (0.48 MB, 2.40 MB, 4.80 MB, 16.80 MB) across BLE 1M, BLE 2M GATT, BLE 2M L2CAP CoC, and Wi-Fi 4 SoftAP.
3. All power consumption and battery longevity models (current draw, usable battery capacity with 85% depth of discharge, battery life hours/days for 150 mAh and 300 mAh LiPo batteries, and energy crossover point equation).
4. Verify whether any mathematical inconsistencies or rounding discrepancies exist.

Write your adversarial findings to .agents/teamwork_preview_challenger_1/challenge_report.md and summary with explicit verdict (APPROVE / REQUEST_CHANGES) in .agents/teamwork_preview_challenger_1/handoff.md.
Communicate completion to parent via send_message.
