SphaeroX/optimistic-hubble/.agents/teamwork_preview_challenger_2/DISPATCH.md

## 2026-08-20T13:43:38Z
You are Challenger 2 (Protocol Stress & Edge-Case Challenger) for the Research & Architectural Study: Optimal IoT-to-Android Audio Sync (XIAO ESP32-C3).

Your working directory is: c:\Users\MGasc\Documents\antigravity\optimistic-hubble\.agents\teamwork_preview_challenger_2
The user requirements are in: c:\Users\MGasc\Documents\antigravity\optimistic-hubble\ORIGINAL_REQUEST.md
The deliverable to challenge is: c:\Users\MGasc\Documents\antigravity\optimistic-hubble\research\iot_android_transfer_study.md

You MUST read ORIGINAL_REQUEST.md and research/iot_android_transfer_study.md.

Adversarially challenge and stress-test the architectural protocols and edge cases:
1. Network dropouts mid-transfer: Does the 30-byte binary chunk header and RFC 7233 HTTP Range resume guarantee zero-drop atomic file recovery?
2. Multi-network routing: Does `OkHttpClient` socket factory binding prevent cellular 5G/LTE leakage and prevent cloud API failures?
3. Android OS background termination: Does the `connectedDevice` Foreground Service withstand Android 14/15 background restrictions?
4. Coexistence single-antenna contention: Does the sequential state machine prevent ESP32-C3 Wi-Fi and BLE hardware collision?
5. LittleFS flash erase latency: Does the 16KB FreeRTOS DMA ring buffer prevent audio dropouts during flash writes?

Write your stress-test report to `.agents/teamwork_preview_challenger_2/challenge_report.md` and summary with explicit verdict (APPROVE / REQUEST_CHANGES) in `.agents/teamwork_preview_challenger_2/handoff.md`.
Communicate completion to parent via send_message.
