SphaeroX/optimistic-hubble/.agents/teamwork_preview_challenger_3/BRIEFING.md

# BRIEFING — 2026-08-20T13:54:00Z

## Mission
Adversarial empirical stress-testing and re-verification of IoT-to-Android Audio Sync protocol, architecture study, and code artifacts.

## 🔒 My Identity
- Archetype: challenger
- Roles: critic, specialist
- Working directory: c:\Users\MGasc\Documents\antigravity\optimistic-hubble\.agents\teamwork_preview_challenger_3
- Original parent: ff5b3206-dca0-46f5-be4f-e7353b2157c6
- Milestone: protocol-stress-reverification
- Instance: 3 of 3

## 🔒 Key Constraints
- Review-only — do NOT modify implementation code directly in deliverable; document findings in challenge report
- Strictly verify empirically with executable test harnesses (Kotlin, C++, Python simulation / oracles)

## Current Parent
- Conversation ID: ff5b3206-dca0-46f5-be4f-e7353b2157c6
- Updated: 2026-08-20T13:54:00Z

## Review Scope
- **Files to review**:
  - ORIGINAL_REQUEST.md
  - 
esearch/iot_android_transfer_study.md
  - .agents/teamwork_preview_challenger_2/challenge_report.md
- **Review criteria**:
  1. 32-byte header parsing in BleL2capAudioReceiver.kt (VERIFIED / PASS)
  2. Robust resume appending and chunk index tracking (VERIFIED / PASS)
  3. Android 14/15 WorkManager execution and FGS restrictions (VERIFIED / PASS)
  4. SoftAP power watchdog timers (60s association / 30s idle) (VERIFIED / PASS)
  5. I2S DMA continuous sampling jitter and drift (VERIFIED / PASS)

## Attack Surface
- **Hypotheses tested**: 30B vs 32B framing underflow, partial resume CRC integrity, Android 14/15 FGS launch restrictions, hanging SoftAP battery deadlock, I2S DMA timing drift.
- **Vulnerabilities found**: All 6 former vulnerabilities resolved in deliverable. Zero blocking issues remain.
- **Untested angles**: None. Automated tests executed and passed.

## Loaded Skills
- None

## Key Decisions Made
- Executed empirical automated verification suite 	ests/test_all_dimensions.py covering all 5 challenge dimensions.
- Concluded with verdict APPROVE.

## Artifact Index
- .agents/teamwork_preview_challenger_3/challenge_report.md — Complete empirical challenge report
- .agents/teamwork_preview_challenger_3/handoff.md — 5-component handoff report and verdict (APPROVE)
- 	ests/test_all_dimensions.py — Automated empirical verification harness
