SphaeroX/optimistic-hubble/.agents/teamwork_preview_challenger_3/DISPATCH.md

# Dispatch for Challenger 3: Re-Verification of Protocol Stress & Edge Cases

## 2026-08-20T13:49:31Z
You are Challenger 3 (Re-Verification of Protocol Stress & Edge Cases) for the Research & Architectural Study: Optimal IoT-to-Android Audio Sync (XIAO ESP32-C3).

Your working directory is: c:\Users\MGasc\Documents\antigravity\optimistic-hubble\.agents\teamwork_preview_challenger_3
The user requirements are in: c:\Users\MGasc\Documents\antigravity\optimistic-hubble\ORIGINAL_REQUEST.md
The updated deliverable is in: c:\Users\MGasc\Documents\antigravity\optimistic-hubble\research\iot_android_transfer_study.md
Previous challenge report: c:\Users\MGasc\Documents\antigravity\optimistic-hubble\.agents\teamwork_preview_challenger_2\challenge_report.md

You MUST read ORIGINAL_REQUEST.md, research/iot_android_transfer_study.md, and the previous challenge report.

Stress-test and re-verify:
1. 32-byte header parsing in `BleL2capAudioReceiver.kt`: Does the unpack loop read all 11 fields correctly without buffer underflow or index misalignment?
2. Robust resume appending: Does `FileOutputStream(tempFile, true)` and chunk index tracking ensure safe resume after mid-transfer network dropouts?
3. Android 14/15 WorkManager execution: Does `AudioSyncWorker` run within OS quota rules and avoid `ForegroundServiceStartNotAllowedException`?
4. SoftAP power watchdog: Does the 60s association / 30s idle timeout in `wifi_server_range.cpp` protect against battery drain deadlocks?
5. I2S DMA continuous sampling: Is the I2S task free of jitter and drift?

Write your challenge report to `.agents/teamwork_preview_challenger_3/challenge_report.md` and your verdict (APPROVE / REQUEST_CHANGES) in `.agents/teamwork_preview_challenger_3/handoff.md`.
Communicate your verdict to parent via send_message.
