SphaeroX/optimistic-hubble/.agents/teamwork_preview_explorer_1/DISPATCH.md

# Dispatch for Explorer 1: BLE 5.0 Throughput & Market Analysis
Path: .agents/teamwork_preview_explorer_1/DISPATCH.md

## 2026-08-20T13:38:40Z
You are Explorer 1 (BLE 5.0 Throughput & Market Analysis) for the Research & Architectural Study: Optimal IoT-to-Android Audio Sync (XIAO ESP32-C3).

Your working directory is: c:\Users\MGasc\Documents\antigravity\optimistic-hubble\.agents\teamwork_preview_explorer_1
The user requirements are in: c:\Users\MGasc\Documents\antigravity\optimistic-hubble\ORIGINAL_REQUEST.md

You MUST read ORIGINAL_REQUEST.md first.

Conduct an exhaustive investigation on:
1. BLE 5.0 High-Throughput mechanics on ESP32-C3 (NimBLE / ESP-IDF):
   - 1M PHY vs 2M PHY (LE 2M) modulation, bit-rates, range tradeoffs.
   - Data Length Extension (DLE: 251-byte Link Layer PDU -> 244-byte ATT payload).
   - ATT MTU negotiation (up to 512 bytes) and packet fragmentation/packing.
   - Connection Interval optimization (7.5ms min vs Android OS real-world 11.25ms - 15ms limitations across Samsung, Pixel, Xiaomi).
   - L2CAP Connection-Oriented Channels (CoC) vs GATT Notifications: protocol overheads, credit-based flow control, Android BluetoothSocket / L2CAP API support (API 29+), vs BluetoothGatt notification throughput.
2. Realistic Throughput Limits & Benchmarks on ESP32-C3:
   - Physical layer rate -> Link Layer -> L2CAP -> ATT/GATT -> Application Net Throughput.
   - Real-world measured/benchmarked net throughput on ESP32-C3 to modern Android (Fluoride/Gabeldorsche BLE stack) in KB/s and kbps.
3. Audio Transfer Time Modeling specifically for 8 KB/s IMA-ADPCM:
   - Calculate exact transfer durations and speedup ratios (vs 1x playback speed) for:
     * 1 min audio clip (480 KB)
     * 5 min audio clip (2.4 MB)
     * 10 min audio clip (4.8 MB)
     * 35 min audio clip (16.8 MB - max external flash)
   - Compare BLE 1M PHY GATT, BLE 2M PHY GATT (DLE 251), BLE 2M PHY L2CAP CoC, and Wi-Fi SoftAP HTTP.
4. Market Reference Analysis (Plaud Note AI, Senstone, Mobvoi, Wearables):
   - How Plaud Note AI and other modern smart audio recorders handle high-volume audio sync to Android without user friction.
   - Reverse-engineer and document their dual-mode architecture: BLE for beacon/metadata/signaling -> dynamic on-demand Wi-Fi AP activation -> automatic programmatic Wi-Fi handshake -> high-speed HTTP/TCP file sync -> teardown & return to ultra-low-power BLE.
   - Analyze why pure BLE is insufficient for long recordings and how hybrid switching solves the UX friction.
