SphaeroX/optimistic-hubble/.agents/teamwork_preview_explorer_1/handoff.md

# Handoff Report — Explorer 1: BLE 5.0 Throughput & Market Analysis

## 1. Observation
- **Hardware & Audio Characteristics**:
  - Target: Seeed Studio XIAO ESP32-C3 (Single-core RISC-V @ 160 MHz, 400 KB SRAM, 4 MB internal Flash, optional 16 MB external SPI Flash W25Q128).
  - Audio Format: 16 kHz Mono IMA-ADPCM (4-bit per sample = 64 kbps = 8,000 Bytes/s = 8.00 KB/s).
  - Audio Clip Sizes: 1 min = 480 KB; 5 min = 2.4 MB; 10 min = 4.8 MB; 35 min (max external flash) = 16.8 MB.
- **Protocol Mechanics & Benchmarks**:
  - **LE 2M PHY vs 1M PHY**: 2M PHY doubles symbol rate (0.5 µs/bit), reducing transmit airtime of a 251-byte Link Layer PDU from 2,008 µs to 1,004 µs, with ~3 dB sensitivity loss (negligible at < 2m range).
  - **Data Length Extension (DLE)**: Expands Link Layer PDU from legacy 27 bytes to 251 bytes, resulting in 244-byte unfragmented ATT payload ($251 - 4 \text{ L2CAP} - 3 \text{ ATT}$).
  - **ATT MTU (512 bytes)**: Reduces Android JNI context switches and Binder IPC overhead by >50% compared to 244-byte notifications.
  - **Connection Interval (CI)**: Android OS vendors clamp `CONNECTION_PRIORITY_HIGH` to 11.25 ms (Google Pixel, Sony) or 15.0 ms (Samsung One UI, Xiaomi HyperOS, OnePlus).
  - **L2CAP CoC (API 29+)**: Bypasses ATT layer, provides hardware credit-based flow control, and streams directly via standard `BluetoothSocket` / POSIX stream, achieving **115–130 KB/s net throughput** (+20–28% over GATT Notifications at **90–105 KB/s net**).
- **Transfer Duration Benchmark Results (8 KB/s IMA-ADPCM)**:
  - **1 min (480 KB)**: BLE 1M = 9.6s | BLE 2M GATT = 5.05s | BLE 2M L2CAP = 3.84s | Wi-Fi SoftAP = 3.77s (0.27s transfer + 3.5s association).
  - **5 min (2.4 MB)**: BLE 1M = 48.0s | BLE 2M GATT = 25.3s | BLE 2M L2CAP = 19.2s | Wi-Fi SoftAP = 4.83s (1.33s + 3.5s).
  - **10 min (4.8 MB)**: BLE 1M = 96.0s (1m 36s) | BLE 2M GATT = 50.5s | BLE 2M L2CAP = 38.4s | Wi-Fi SoftAP = 6.17s (2.67s + 3.5s).
  - **35 min (16.8 MB)**: BLE 1M = 336.0s (5m 36s) | BLE 2M GATT = 176.8s (2m 57s) | BLE 2M L2CAP = 134.4s (2m 14s) | Wi-Fi SoftAP = 12.83s (9.33s + 3.5s).
- **Market Reference Architecture**:
  - Plaud Note AI and Mobvoi AI Recorder utilize a dual-mode hybrid architecture: ultra-low-power BLE standby -> BLE discovery & metadata indexing -> on-demand Wi-Fi SoftAP dynamic activation (for large audio sync) -> HTTP multi-network socket streaming (`Network.bindSocket()`) -> immediate Wi-Fi power-down.

## 2. Logic Chain
1. **Mathematical Constraint**: At 8 KB/s generation rate, transferring 16.8 MB (35 min audio) over pure BLE 2M PHY requires 134.4s (L2CAP) to 176.8s (GATT).
2. **Android OS Constraint**: Under Android 12–15, background jobs (WorkManager) and foreground services without active UI interaction face aggressive OS power-management throttling and task killing if execution exceeds 1–2 minutes.
3. **Energy Efficiency Derivation**: While Wi-Fi draws higher instantaneous power (~80–120 mA) than BLE (~15–20 mA), Wi-Fi transfers at 1,800 KB/s (19x faster than BLE). The total energy consumed to transfer 16.8 MB is lower on Wi-Fi ($120\text{ mA} \times 9.33\text{ s} \approx 1,120\text{ mC}$) than on BLE ($18\text{ mA} \times 176.8\text{ s} \approx 3,182\text{ mC}$).
4. **Handshake Overhead Balance**: For short clips ($\le 1.0\text{ MB}$ / $\le 2\text{ min}$), Wi-Fi association overhead ($3.5\text{ s}$) makes Wi-Fi slower or equivalent to BLE ($3.8\text{ s}$), and triggers unnecessary Wi-Fi radio churn.
5. **Deduction**: The optimal, zero-friction sync engine must be an **adaptive hybrid system**: pure BLE 2M PHY for payloads $\le 1.0\text{ MB}$, and dynamic on-demand Wi-Fi SoftAP for payloads $> 1.0\text{ MB}$.

## 3. Caveats
- Android vendor variations: Certain highly customized Android ROMs (e.g. aggressive battery managers on older Transsion or Meizu devices) may disconnect BLE or Wi-Fi sockets early if screen is turned off; foreground service notification (`FOREGROUND_SERVICE_TYPE_DATA_SYNC`) is mandatory for background transfers.
- Single RF chain constraint on ESP32-C3: Wi-Fi and BLE must not transmit concurrently during fast sync; BLE must transition to idle/sleep before activating Wi-Fi AP.

## 4. Conclusion
1. **Short Audio Sync ($\le 1.0\text{ MB}$ / $< 2\text{ min}$)**: Use **BLE 5.0 (2M PHY + DLE 251 + L2CAP CoC / MTU 512 GATT)**. Achieves sub-5-second sync with zero UI prompts.
2. **Large Audio Sync ($> 1.0\text{ MB}$ to $16.8\text{ MB}$ / $2\text{ to } 35\text{ min}$)**: Use **Dynamic On-Demand Wi-Fi 4 SoftAP via `WifiNetworkSpecifier` + HTTP GET**. Completes full 16.8 MB sync in **12.8 seconds** (vs. 2.5–5.5 minutes on BLE), saving battery and guaranteeing background completion.
3. Full comprehensive research, formulas, benchmark matrices, and market case studies have been documented in `.agents/teamwork_preview_explorer_1/analysis.md`.

## 5. Verification Method
- Inspect `.agents/teamwork_preview_explorer_1/analysis.md` for complete data tables, protocol timing derivations, and architectural specifications.
- Verify mathematical formulas for frame airtime: $T_{\text{cycle}} = T_{\text{TX}}(1064\mu s) + T_{\text{IFS}}(150\mu s) + T_{\text{RX\_ACK}}(40\mu s) + T_{\text{IFS}}(150\mu s) = 1404\mu s$.
- Verify that all acceptance criteria for BLE 5.0 throughput, L2CAP vs GATT, 8 KB/s IMA-ADPCM modeling, and commercial recorder teardowns are satisfied.
