SphaeroX/optimistic-hubble/.agents/teamwork_preview_explorer_1/progress.md

# Progress — Explorer 1: BLE 5.0 Throughput & Market Analysis

**Last visited**: 2026-08-20T13:40:30Z

- [x] Initialized DISPATCH.md and BRIEFING.md
- [x] Task 1: BLE 5.0 High-Throughput Mechanics on ESP32-C3 (NimBLE / ESP-IDF)
- [x] Task 2: Realistic Throughput Limits & Benchmarks on ESP32-C3 vs Android
- [x] Task 3: Mathematical Audio Transfer Time Modeling (8 KB/s IMA-ADPCM)
- [x] Task 4: Market Reference Analysis (Plaud Note AI, Senstone, Mobvoi)
- [x] Task 5: Compilation of comprehensive analysis.md and handoff.md
