SphaeroX/optimistic-hubble/.agents/teamwork_preview_explorer_2/handoff.md

# Handoff Report: Explorer 2 (Android OS Networking & Background Execution)

**Agent**: Explorer 2  
**Target Milestone**: Comprehensive Android 10–15 (API 29–35+) Networking, Multi-Network Socket Routing & Background Execution Analysis for XIAO ESP32-C3 Audio Sync  
**Detailed Report Location**: `.agents/teamwork_preview_explorer_2/analysis.md`  
**Date**: 2026-08-20  

---

## 1. Observation

1. **Android Programmatic Wi-Fi API Constraints (`WifiNetworkSpecifier`)**:
   - Starting with Android 10 (API 29), legacy `WifiManager.enableNetwork()` and `WifiConfiguration` are completely deprecated.
   - `WifiNetworkSpecifier.Builder` paired with `ConnectivityManager.requestNetwork()` enforces a modal system UI dialog/bottom sheet ("Connect to device?").
   - Android OS does not permit background invocation of `requestNetwork()` with `WifiNetworkSpecifier`; background requests fail immediately (`onUnavailable()`) or trigger a security exception unless invoked with foreground UI context.
   - Connection is strictly ephemeral: unregistering `ConnectivityManager.NetworkCallback` instantly tears down the Wi-Fi link (< 200 ms) and restores default routes.
2. **Multi-Network Routing & Cellular Internet Preservation**:
   - ESP32-C3 SoftAP (`192.168.4.1`) lacks upstream WAN connectivity (`NET_CAPABILITY_INTERNET` is absent/unvalidated).
   - Calling `ConnectivityManager.bindProcessToNetwork(network)` binds the entire OS process to the local Wi-Fi interface (`wlan0`), causing all cloud APIs (Whisper, OpenAI, Firebase, telemetry) to fail with `UnknownHostException`/`ConnectException`.
   - Android supports per-socket routing via `network.socketFactory` and `Network.bindSocket(Socket)`. In OkHttp, passing `OkHttpClient.Builder().socketFactory(network.socketFactory)` isolates HTTP requests to `192.168.4.1` while preserving 5G/LTE Cellular internet for the rest of the application.
3. **Android Background Restrictions & Permissions (API 29–35+)**:
   - Android 12+ (API 31+) decouples Bluetooth from GPS location via `android.permission.BLUETOOTH_SCAN` with `android:usesPermissionFlags="neverForLocation"` and `android.permission.BLUETOOTH_CONNECT`. No location permissions (`ACCESS_FINE_LOCATION`) are required for direct GATT/L2CAP connections.
   - Android 14 & 15 (API 34/35+) mandate explicit `foregroundServiceType`. `foregroundServiceType="connectedDevice"` has **unlimited duration** during active peripheral communication, whereas `foregroundServiceType="dataSync"` is restricted to a **6-hour cumulative timeout** and blocked from `BOOT_COMPLETED` in Android 15.
   - `BluetoothLeScanner.startScan(filters, settings, pendingIntent)` with hardware `ScanFilter` wakes `BroadcastReceiver` on advertising matches with **zero CPU wakeups during standby**.
   - `CompanionDeviceManager` (CDM) association unlocks battery optimization exemptions (`REQUEST_COMPANION_RUN_IN_BACKGROUND`) and background presence callbacks via `CompanionDeviceService`.

---

## 2. Logic Chain

1. **Step 1 (Wi-Fi UX & Feasibility)**: Because `WifiNetworkSpecifier` requires explicit user confirmation in a system dialog on every ephemeral session and cannot be triggered from the background (Observation 1), **Wi-Fi SoftAP cannot be used for zero-click silent background sync**. It is solely viable for user-initiated / on-open fast sync.
2. **Step 2 (Silent Background Channel)**: Because Android supports low-power hardware BLE scan filters via `PendingIntent` (Observation 3) and allows silent background GATT/L2CAP connections without user prompts, **Pure BLE 5.0 is the only viable zero-friction, silent background sync channel**.
3. **Step 3 (Dual-Network Integrity)**: Because the ESP32 SoftAP has no internet WAN routing, calling `bindProcessToNetwork()` breaks all cloud services for the app; however, configuring `OkHttpClient` with `network.socketFactory` binds only the ESP32 HTTP requests to `wlan0` (Observation 2). Therefore, **the app can stream audio from `192.168.4.1` over Wi-Fi while concurrently uploading transcripts to cloud APIs over 5G/LTE**.
4. **Step 4 (FGS Selection in Android 14/15)**: Because Android 14/15 restricts `dataSync` to 6 hours and disallows boot launches, while `connectedDevice` supports continuous peripheral communication without timeouts (Observation 3), **all audio sync background services must declare `foregroundServiceType="connectedDevice"`**.
5. **Step 5 (Optimal Hybrid Strategy)**: Combining Step 1, 2, 3, and 4: Small audio files (0.5 MB–2 MB; 1–5 min recordings) transfer silently over BLE 5.0 in ~4–20s in the background. Large audio files (> 2 MB up to 16 MB; 15–33 min recordings) trigger a 1-tap in-app notification prompt launching `WifiNetworkSpecifier` for ultra-fast HTTP sync at 2.0 MB/s (16 MB in ~8s) with cellular preservation.

---

## 3. Caveats

1. **OEM Custom Battery Optimizations**: Certain aggressive Android OEMs (e.g. Xiaomi MIUI/HyperOS, Huawei EMUI, Samsung OneUI aggressive sleep) may restrict background PendingIntents unless the user explicitly exempts the app via `Settings.ACTION_REQUEST_IGNORE_BATTERY_OPTIMIZATIONS` or pairs via `CompanionDeviceManager`.
2. **Wi-Fi 4 SoftAP Handshake Latency**: Establishing a Wi-Fi association via `WifiNetworkSpecifier` involves 802.11 probe requests, authentication, 4-way WPA2 handshake, and DHCP IP acquisition, which adds a fixed overhead of **2.5 to 4.0 seconds** before HTTP transfer begins. For files under 1 MB, BLE 5.0 is faster end-to-end.
3. **Assumption on Audio Codec**: Calculations assume 8 KB/s IMA-ADPCM (16 kHz 16-bit mono compressed to 4 bits/sample = 64 kbps = 8 KB/s). If uncompressed 16-bit PCM (32 KB/s) is used, file sizes scale by 4x.

---

## 4. Conclusion

The optimal Android architecture for Seeed Studio XIAO ESP32-C3 audio synchronization is a **Tiered Hybrid Sync Engine**:
- **Tier 1 (Silent Background Sync, < 2 MB)**: Pure BLE 5.0 (L2CAP CoC / 2M PHY @ 60–125 KB/s). Triggered via BLE Scan PendingIntent or `CompanionDeviceService`. Zero clicks, runs in `connectedDevice` FGS. 1-minute clip (0.48 MB) syncs in **~4.8 seconds**.
- **Tier 2 (Fast 1-Tap Wi-Fi Sync, 2 MB – 16 MB)**: BLE signals Wi-Fi SoftAP activation; Android app prompts a 1-tap confirmation (`WifiNetworkSpecifier`); OkHttp downloads audio from `192.168.4.1` via isolated `network.socketFactory` at **1.5–2.5 MB/s**. 16 MB recording syncs in **~8.0 seconds** with complete cellular internet preservation.
- **Compliance**: Android 12–15 compliant using `BLUETOOTH_SCAN` (`neverForLocation`), `BLUETOOTH_CONNECT`, `FOREGROUND_SERVICE_CONNECTED_DEVICE`, and `CompanionDeviceManager`.

---

## 5. Verification Method

To independently verify the technical findings and Kotlin reference implementations:
1. **Inspect Analysis Report**:
   - View `.agents/teamwork_preview_explorer_2/analysis.md` for complete API documentation, architectural diagrams, version comparison table (API 29–35+), and full Kotlin source listings (`IotWifiManager`, `IotHttpClientFactory`, `AudioSyncForegroundService`, `BlePresenceReceiver`).
2. **Verify Multi-Network Dual Routing**:
   - Run an OkHttp request using `IotHttpClientFactory.createClient(iotNetwork)` to `http://192.168.4.1/api/audio` while simultaneously executing a standard `OkHttpClient` GET to `https://api.openai.com/v1/models` on a dual-SIM or Cellular+Wi-Fi Android test device. Verify that both requests succeed concurrently.
3. **Verify Android 14/15 Foreground Service Compliance**:
   - Target `compileSdk 35`, `targetSdk 35`. Run `AudioSyncForegroundService` with `ServiceInfo.FOREGROUND_SERVICE_TYPE_CONNECTED_DEVICE` and assert that no `MissingForegroundServiceTypeException` or `SecurityException` is thrown.
