SphaeroX/optimistic-hubble/.agents/teamwork_preview_explorer_3/DISPATCH.md

## 2026-08-20T13:38:40Z

You are Explorer 3 (ESP32-C3 Firmware Architecture & Sync Protocol) for the Research & Architectural Study: Optimal IoT-to-Android Audio Sync (XIAO ESP32-C3).

Your working directory is: c:\Users\MGasc\Documents\antigravity\optimistic-hubble\.agents\teamwork_preview_explorer_3
The user requirements are in: c:\Users\MGasc\Documents\antigravity\optimistic-hubble\ORIGINAL_REQUEST.md

You MUST read ORIGINAL_REQUEST.md first.

Conduct an exhaustive investigation on:
1. ESP32-C3 Hardware, RF & Memory Architecture:
   - Single-core RISC-V 32-bit CPU @ 160MHz, 400KB SRAM, 4MB Flash (or external 16MB W25Q128 SPI-Flash).
   - Single RF frontend (2.4 GHz) shared between 802.11 b/g/n Wi-Fi and Bluetooth 5.0 LE.
   - RF Coexistence dynamics: Time-Division Multiplexing (TDM) coexistence penalties vs sequential state machine architecture (Deep Sleep -> BLE low-power advertising -> BLE handshake -> Dynamic on-demand Wi-Fi AP start -> High-speed HTTP stream -> Wi-Fi shutdown -> BLE idle).
   - Power consumption profile across states: Deep Sleep (5 uA), Light Sleep (130 uA), BLE Advertising (1-2 mA avg), BLE Connected 2M PHY (15-20 mA), Wi-Fi SoftAP active/streaming (80-120 mA peak / 180 mA TX).
   - Battery life modeling for a typical 150 mAh / 300 mAh wearable LiPo battery.
2. Flash Storage Streaming & I/O Performance:
   - LittleFS on internal 4MB Flash vs raw SPI-Flash (W25Q128): read throughput limits, 4KB sector alignment, DMA buffer sizing, preventing audio recording interruption vs transfer streaming.
3. Local Wi-Fi Station Mode (STA) & mDNS / Local HTTP Sync:
   - BLE Wi-Fi credential provisioning (Espressif Protocomm or custom GATT service).
   - mDNS service advertisement (`_xiao-audio._tcp.local` @ port 80).
   - Zero-configuration local LAN synchronization when user is at home or device is on charging dock.
4. Resilient Chunked Transfer & Recovery Protocol:
   - Designing a bulletproof chunked transfer protocol (over BLE L2CAP/GATT or HTTP):
     * Chunk headers (Sequence ID, Offset, Chunk Size, Total File Size, CRC32 / xxHash).
     * Partial transfer resume: `Range: bytes=offset-` in HTTP or `RESUME_FROM_OFFSET(chunkIdx)` in BLE.
     * Packet loss handling, sliding window / credit-based flow control, timeout & retry strategies, deduplication, atomic file finalization.

Write your comprehensive findings to:
`c:\Users\MGasc\Documents\antigravity\optimistic-hubble\.agents\teamwork_preview_explorer_3\analysis.md`
And write your final summary to `handoff.md` in your working directory.
Communicate completion to parent via send_message.
