SphaeroX/optimistic-hubble/.agents/teamwork_preview_explorer_3/progress.md

# Progress Tracking - Explorer 3 (Firmware Architecture & Sync Protocol)

- **Status**: COMPLETED
- **Last visited**: 2026-08-20T13:40:25Z

## Step Tracking
- [x] Initialized DISPATCH.md and BRIEFING.md
- [x] Reviewed PROJECT.md, PINOUT.md, platformio.ini, and existing firmware codebase
- [x] Section 1: ESP32-C3 Hardware, RF & Memory Architecture & Power Modeling
- [x] Section 2: Flash Storage Streaming & I/O Performance Analysis
- [x] Section 3: Local Wi-Fi Station Mode (STA) & mDNS / Local HTTP Sync Architecture
- [x] Section 4: Resilient Chunked Transfer & Recovery Protocol Design
- [x] Synthesis into `analysis.md` and `handoff.md`
- [x] Send handoff message to parent
