SphaeroX/optimistic-hubble/.agents/teamwork_preview_reviewer_1/DISPATCH.md

## 2026-08-20T13:43:38Z
You are Reviewer 1 (Technical & Protocol Reviewer) for the Research & Architectural Study: Optimal IoT-to-Android Audio Sync (XIAO ESP32-C3).

Your working directory is: c:\Users\MGasc\Documents\antigravity\optimistic-hubble\.agents\teamwork_preview_reviewer_1
The user requirements are in: c:\Users\MGasc\Documents\antigravity\optimistic-hubble\ORIGINAL_REQUEST.md
The finalized deliverable to review is in: c:\Users\MGasc\Documents\antigravity\optimistic-hubble\research\iot_android_transfer_study.md

You MUST read ORIGINAL_REQUEST.md and research/iot_android_transfer_study.md.

Evaluate:
1. Thoroughness of R1 (BLE 5.0 2M PHY, DLE 251, L2CAP CoC vs GATT, Android WifiNetworkSpecifier/CompanionDeviceManager, multi-network cellular data preservation, Wi-Fi STA mDNS, Plaud Note AI reverse engineering).
2. Thoroughness of R2 (Quantitative benchmark tables, 8 KB/s IMA-ADPCM transfer time models for 1m/5m/10m/35m recordings, UX friction scoring, Android API 29-35+ permission matrix, power & battery models for 150/300 mAh LiPo, multi-attribute trade-off matrix).
3. Soundness of R3 (Tiered Hybrid strategy, Silent BLE background sync vs 1-tap Wi-Fi SoftAP sync vs Docked LAN STA sync, 30-byte chunk header & RFC 7233 Range resume protocol).
4. Clarity of R4 (Mermaid diagrams, ESP32-C3 firmware architecture, Android Kotlin reference implementation).

Write your detailed review to `.agents/teamwork_preview_reviewer_1/review.md` and your summary with explicit verdict (APPROVE / REQUEST_CHANGES) in `.agents/teamwork_preview_reviewer_1/handoff.md`.
Communicate your verdict to parent via send_message.
