SphaeroX/optimistic-hubble/.agents/teamwork_preview_reviewer_1/progress.md

# Progress — Reviewer 1 (Technical & Protocol Reviewer)

- Status: COMPLETED
- Last visited: 2026-08-20T13:44:35Z
- Current step: Review completed, review.md and handoff.md written, sending verdict to parent.
