SphaeroX/optimistic-hubble/.agents/teamwork_preview_reviewer_2/BRIEFING.md

# BRIEFING — 2026-08-20T13:45:00Z

## Mission
Adversarial and quality review of Android Kotlin & ESP32-C3 C++ implementation in the IoT-to-Android audio sync study.

## 🔒 My Identity
- Archetype: reviewer, critic
- Roles: reviewer, critic
- Working directory: c:\Users\MGasc\Documents\antigravity\optimistic-hubble\.agents\teamwork_preview_reviewer_2
- Original parent: ff5b3206-dca0-46f5-be4f-e7353b2157c6
- Milestone: Review Deliverable
- Instance: Reviewer 2

## 🔒 Key Constraints
- Review-only — do NOT modify implementation code directly
- Thorough check for integrity violations, dummy snippets, syntax errors, and architectural flaws
- Verify Android 10-15 (API 29-35+) lifecycle, permissions, coroutines, OkHttp socket binding, L2CAP CoC, FreeRTOS DMA ringbuffer, RFC 7233 range requests

## Current Parent
- Conversation ID: ff5b3206-dca0-46f5-be4f-e7353b2157c6
- Updated: 2026-08-20T13:45:00Z

## Review Scope
- **Files to review**: ORIGINAL_REQUEST.md, research/iot_android_transfer_study.md
- **Interface contracts**: Android Kotlin components (IotWifiManager, IotHttpClientFactory, BleL2capAudioReceiver, AudioSyncForegroundService, AudioSyncWorker) and ESP32-C3 C++ firmware blueprint
- **Review criteria**: correctness, integrity, edge cases, coroutine safety, memory leaks, OS compliance, FreeRTOS correctness

## Review Checklist
- **Items reviewed**:
  - `research/iot_android_transfer_study.md` (Full 1474 lines reviewed)
  - Mathematical models & airtime formulas (Verified)
  - Android Kotlin components (`IotWifiManager`, `IotHttpClientFactory`, `BleL2capAudioReceiver`, `AudioSyncForegroundService`, `AudioSyncWorker`)
  - ESP32-C3 C++ components (`audio_ringbuffer_engine.cpp`, `wifi_server_range.cpp`)
- **Verdict**: REQUEST_CHANGES
- **Unverified claims**: None (all checked and verified)

## Attack Surface
- **Hypotheses tested**:
  - Struct packing vs byte buffer sizing (Failed in original code: 32 vs 30 bytes BufferUnderflowException)
  - Dummy/facade implementation check (Failed in original code: delay(4000) in AudioSyncForegroundService)
  - ESP32 Arduino WebServer header lifecycle (Failed in original code: missing collectHeaders)
  - WorkManager background execution decoupling (Failed in original code)
- **Vulnerabilities found**: 2 Critical, 3 Major, 3 Minor
- **Untested angles**: Hardware RF laboratory testing on physical silicon

## Key Decisions Made
- Issued REQUEST_CHANGES verdict with complete remediation code blocks provided in review.md and handoff.md.

## Artifact Index
- .agents/teamwork_preview_reviewer_2/review.md — Detailed review report
- .agents/teamwork_preview_reviewer_2/handoff.md — Handoff with final verdict
