SphaeroX/optimistic-hubble/.agents/teamwork_preview_reviewer_2/progress.md

# Progress Log

- **Status**: Review Complete. Handoff and Review reports generated.
- **Last visited**: 2026-08-20T13:45:00Z
- **Current Step**: Reporting verdict to parent agent.
