SphaeroX/optimistic-hubble/.agents/teamwork_preview_reviewer_3/BRIEFING.md

# BRIEFING — 2026-08-20T15:51:00Z

## Mission
Re-verify that all 8 findings from Reviewer 2 have been fully and properly resolved in research/iot_android_transfer_study.md, ensure strict Android 14/15 compliance and production-ready reference implementations, and issue an objective review verdict.

## 🔒 My Identity
- Archetype: reviewer_critic
- Roles: reviewer, critic
- Working directory: c:\Users\MGasc\Documents\antigravity\optimistic-hubble\.agents\teamwork_preview_reviewer_3
- Original parent: ff5b3206-dca0-46f5-be4f-e7353b2157c6
- Milestone: Review 3
- Instance: 1 of 1

## 🔒 Key Constraints
- Review-only — do NOT modify implementation code or deliverable directly
- Actively check for integrity violations (hardcoded test results, facade implementations, shortcuts, fabricated verifications)
- Strictly verify Android 14/15 background execution, foreground service types, and power constraints
- Self-contained handoff and review report

## Current Parent
- Conversation ID: ff5b3206-dca0-46f5-be4f-e7353b2157c6
- Updated: 2026-08-20T15:51:00Z

## Review Scope
- **Files to review**:
  - `ORIGINAL_REQUEST.md`
  - `research/iot_android_transfer_study.md`
  - `.agents/teamwork_preview_reviewer_2/review.md`
- **Interface contracts**: `ORIGINAL_REQUEST.md`, ESP32-C3 hardware constraints, Android 14/15 foreground service / permissions specifications
- **Review criteria**: correctness, completeness, quality, adversarial robustness, integrity, zero-placeholder production readiness

## Key Decisions Made
- All 8 findings from Reviewer 2 (CRIT-01, CRIT-02, MAJ-01, MAJ-02, MAJ-03, MIN-01, MIN-02, MIN-03) verified 100% resolved.
- Verified absence of integrity violations, dummy codes, and buffer sizing mismatches.
- Issued verdict: APPROVE.

## Review Checklist
- **Items reviewed**: `research/iot_android_transfer_study.md`, `ORIGINAL_REQUEST.md`, `.agents/teamwork_preview_reviewer_2/review.md`
- **Verdict**: APPROVE
- **Unverified claims**: None (all claims verified)

## Attack Surface
- **Hypotheses tested**:
  - 32-byte header struct alignment and deserialization loop: PASS
  - Android 14/15 FGS type `connectedDevice` and WorkManager lifecycle binding: PASS
  - Arduino ESP32 WebServer `collectHeaders` and HTTP 206/416 RFC 7233 Range handling: PASS
  - ESP32 NimBLE L2CAP CoC credit flow control and memory buffer management: PASS
  - Multi-network socket factory isolation on cellular LTE/5G: PASS
- **Vulnerabilities found**: 0 (all prior vulnerabilities resolved)
- **Untested angles**: None within scope of document review

## Artifact Index
- `.agents/teamwork_preview_reviewer_3/DISPATCH.md` — Incoming dispatch log
- `.agents/teamwork_preview_reviewer_3/BRIEFING.md` — Agent state and working memory
- `.agents/teamwork_preview_reviewer_3/progress.md` — Liveness heartbeat
- `.agents/teamwork_preview_reviewer_3/review.md` — Detailed review report
- `.agents/teamwork_preview_reviewer_3/handoff.md` — Handoff and verdict
