SphaeroX/optimistic-hubble/.agents/teamwork_preview_victory_auditor_1/DISPATCH.md

## 2026-08-20T13:55:18Z
You are the independent Victory Auditor for the Research & Architectural Study: Optimal IoT-to-Android Audio Sync (XIAO ESP32-C3).

Your working directory is: c:\Users\MGasc\Documents\antigravity\optimistic-hubble\.agents\teamwork_preview_victory_auditor_1
The workspace root is: c:\Users\MGasc\Documents\antigravity\optimistic-hubble
The authoritative user request is in: c:\Users\MGasc\Documents\antigravity\optimistic-hubble\ORIGINAL_REQUEST.md
The deliverable under audit is: c:\Users\MGasc\Documents\antigravity\optimistic-hubble\research\iot_android_transfer_study.md

Please conduct an independent, strict 3-phase audit:
Phase 1: Verification of deliverable against all requirements (R1: BLE 5.0 2M PHY/DLE/L2CAP, WifiNetworkSpecifier/CompanionDeviceManager, Station Mode mDNS, Plaud Note / commercial analysis; R2: Benchmarks for 8 KB/s ADPCM audio files 0.5MB-16MB, UX friction, Android API 29-35+ constraints, power consumption & battery models, complexity matrix; R3: Tiered hybrid architecture, background & foreground sync modes, CRC32 chunking & RFC 7233 resume; R4: 4 Mermaid sequence diagrams, ESP32-C3 firmware C++ blueprint, production-grade Android Kotlin reference code).
Phase 2: Technical rigor, code quality, and anti-hallucination / cheating checks.
Phase 3: Checklist against all Acceptance Criteria in ORIGINAL_REQUEST.md.

Produce your structured audit report and return either a "VICTORY CONFIRMED" or "VICTORY REJECTED" verdict.
