SphaeroX/optimistic-hubble/.agents/teamwork_preview_victory_auditor_1/handoff.md

# VICTORY AUDIT HANDOFF REPORT

## 1. Observation
- **Deliverable**: `research/iot_android_transfer_study.md` (2,034 lines, 106,823 bytes).
- **Requirements Traced**: R1.1-R1.4, R2.1-R2.7, R3.1-R3.3, R4.1-R4.3 from `ORIGINAL_REQUEST.md`.
- **Acceptance Criteria**: 8 of 8 criteria in `ORIGINAL_REQUEST.md` verified line-by-line.
- **Empirical Execution**:
  - `python tests/test_all_dimensions.py`: Exited code 0, 5/5 dimensions PASS.
  - `python .agents/teamwork_preview_auditor_2/verify_study.py`: Exited code 0, all calculations, packet airtimes, power crossover models, and struct packing verified.
- **Forensic Check**: No hardcoded shortcuts, no placeholder text (`TODO`, `FIXME`, `TBD`, `stub`), authentic publication-grade technical specifications.

## 2. Logic Chain
1. `ORIGINAL_REQUEST.md` defines 4 core requirement blocks (R1 State-of-the-Art, R2 Benchmarks & Trade-Offs, R3 Hybrid Architecture & Recovery, R4 Blueprint & Reference Code) and 8 Acceptance Criteria for the XIAO ESP32-C3 audio synchronization study.
2. Direct inspection of `research/iot_android_transfer_study.md` confirms comprehensive coverage across 6 major chapters with mathematical formulations, hardware profiling, protocol physics, sequence diagrams, C++ firmware code, and production Kotlin Android code.
3. Independent re-execution of test suites confirmed:
   - Frame-by-frame 2M PHY airtime derivation ($T_{\text{cycle}} = 1404.0 \text{ µs}$, 712.25 pkts/s, $175.93 \text{ KB/s}$ L2CAP max).
   - Energy consumption crossover point ($S_{\text{cross}} = 4.21 \text{ MB}$).
   - Struct memory layout (exactly 32 bytes packed, `<HBBIIIHHIII`).
   - Android 14/15 `FOREGROUND_SERVICE_TYPE_CONNECTED_DEVICE` compliance and `Network.socketFactory` isolation.
4. Git commit history and agent audit logs prove authentic multi-stage iterative research, review, challenge testing, and refinement.
5. All acceptance criteria are satisfied with zero violations.

## 3. Caveats
- No caveats. The deliverable is complete, mathematically rigorous, and immediately actionable for hardware and Android developers.

## 4. Conclusion
The deliverable `research/iot_android_transfer_study.md` satisfies 100% of the project requirements and acceptance criteria in `ORIGINAL_REQUEST.md`. **VICTORY CONFIRMED**.

## 5. Verification Method
- Execute independent Python test suite: `python tests/test_all_dimensions.py`
- Verify mathematics script: `python .agents/teamwork_preview_auditor_2/verify_study.py`
- View full study: `view_file` on `research/iot_android_transfer_study.md`
