SphaeroX/optimistic-hubble/.agents/teamwork_preview_worker_1/BRIEFING.md

# BRIEFING — 2026-08-20T13:43:25Z

## Mission
Synthesize the complete, authoritative, publication-grade, and actionable final research and architectural study on Optimal IoT-to-Android Audio Sync (XIAO ESP32-C3) into `research/iot_android_transfer_study.md`.

## 🔒 My Identity
- Archetype: implementer, qa, specialist
- Roles: Master Technical Study Compiler
- Working directory: c:\Users\MGasc\Documents\antigravity\optimistic-hubble\.agents\teamwork_preview_worker_1
- Original parent: ff5b3206-dca0-46f5-be4f-e7353b2157c6
- Milestone: Architectural Study Synthesis

## 🔒 Key Constraints
- Pure genuine technical synthesis — no placeholders, no dummy code, no truncated sections.
- Integrate all 3 explorer deep-dives (Explorer 1 BLE/L2CAP, Explorer 2 Android 10-15 Multi-Network/CDM, Explorer 3 ESP32-C3 Coexistence/Power/Recovery).
- Follow the exact 6-section structure requested by the user.
- Complete production-grade Kotlin and C++ firmware implementations.
- Write output to `research/iot_android_transfer_study.md`.

## Current Parent
- Conversation ID: ff5b3206-dca0-46f5-be4f-e7353b2157c6
- Updated: 2026-08-20T13:43:25Z

## Task Summary
- **What to build**: Full exhaustive technical deliverable in `research/iot_android_transfer_study.md`.
- **Success criteria**: 100% full coverage of R1, R2, R3, R4, acceptance criteria, mathematical models, Mermaid diagrams, complete Kotlin/C++ code, power models, permission matrix.
- **Status**: Completed! 1,474 lines, 80 KB document generated.

## Key Decisions Made
- Established the 3-Tier Adaptive Hybrid Sync Engine as the optimal architecture for the XIAO ESP32-C3:
  - Tier 1: Silent Background Sync (< 2.0 MB / < 4 min audio) via BLE 5.0 L2CAP CoC / 2M PHY (0 clicks, 4-18s duration).
  - Tier 2: Dynamic SoftAP Fast Sync (>= 2.0 MB to 16.8 MB) via WifiNetworkSpecifier + OkHttp socketFactory (1 tap, 1.8-2.2 MB/s, cellular LTE preserved).
  - Tier 3: Docked Zero-Touch Home LAN Sync via Wi-Fi STA + mDNS (0 clicks, 2.8 MB/s, 0 battery drain).
- Isolated per-socket routing via `Network.socketFactory` to resolve the fatal flaw of `bindProcessToNetwork()`.
- Implemented FreeRTOS ringbuffer architecture isolating Priority 10 audio recording from network streaming.

## Artifact Index
- `research/iot_android_transfer_study.md` — Final publication-grade technical study.
- `.agents/teamwork_preview_worker_1/handoff.md` — Final handoff report.
- `.agents/teamwork_preview_worker_1/progress.md` — Progress log.
- `.agents/teamwork_preview_worker_1/DISPATCH.md` — Dispatch record.
