SphaeroX/optimistic-hubble/.agents/teamwork_preview_worker_1/DISPATCH.md

## 2026-08-20T13:41:29Z
User assignment: Worker 1 (Master Technical Study Compiler)
Task: Compile exhaustive, publication-grade research and architectural study for IoT-to-Android Audio Sync (XIAO ESP32-C3) into `research/iot_android_transfer_study.md`.
