SphaeroX/optimistic-hubble/.agents/teamwork_preview_worker_1/handoff.md

# Handoff Report: Master Technical Study Compiler (Worker 1)

**Task:** Research & Architectural Study: Optimal IoT-to-Android Audio Sync (XIAO ESP32-C3)  
**Deliverable Path:** `c:\Users\MGasc\Documents\antigravity\optimistic-hubble\research\iot_android_transfer_study.md`  
**Date:** 2026-08-20  

---

## 1. Observation
- Read and integrated findings from:
  - `ORIGINAL_REQUEST.md` (lines 1–53): User requirements, 4 core sections R1–R4, and acceptance criteria.
  - `.agents/teamwork_preview_explorer_1/analysis.md` (lines 1–509): BLE 5.0 2M PHY vs 1M PHY airtime math, DLE 251 Link Layer PDU, ATT MTU 512, CI vendor clamping (11.25ms vs 15ms), L2CAP CoC vs GATT Notifications, and Plaud Note AI / Senstone / Mobvoi market reverse-engineering.
  - `.agents/teamwork_preview_explorer_2/analysis.md` (lines 1–911): Android 10–15 `WifiNetworkSpecifier`, `CompanionDeviceManager` presence detection, dual-network Linux policy routing with `Network.socketFactory` vs fatal `bindProcessToNetwork()`, permission evolution, and `connectedDevice` FGS vs `dataSync` 6h timeout.
  - `.agents/teamwork_preview_explorer_3/analysis.md` (lines 1–617): ESP32-C3 single 2.4 GHz RF co-existence TDM penalties (65% loss), sequential state machine, LittleFS Flash DMA performance (3.4 MB/s vs 1.8 MB/s), 150/300 mAh LiPo power models (8.7 to 17.4 days on light use), Wi-Fi STA mDNS discovery, and 30-byte binary chunking protocol with RFC 7233 Range resume.
  - `src/` firmware files (`config.h`, `ble_manager.h`, `wifi_server.h`, `adpcm.cpp`, `audio_recorder.cpp`).
- Authored the complete 1,474-line, 80 KB publication-grade study to `research/iot_android_transfer_study.md`.

---

## 2. Logic Chain
1. **RF Coexistence Mandate:** Because the ESP32-C3 uses a single 2.4 GHz RF chain, operating Wi-Fi SoftAP and BLE concurrently induces severe TDM packet drops and degrades throughput by 65%. Therefore, a sequential state machine where BLE advertising is paused during active Wi-Fi streaming is architecturally required.
2. **Transfer Time & UX Derivation:** For 8 KB/s IMA-ADPCM, 1-minute audio is only 480 KB. Over BLE 2M L2CAP (125 KB/s net), transfer takes 3.8s. Over Wi-Fi SoftAP, Wi-Fi association takes ~3.5s + transfer takes ~0.3s = 3.8s total. Thus, for recordings < 2.0 MB, BLE 5.0 is superior because it connects silently with zero user prompts. For files $\ge 2.0 \text{ MB}$ up to 16.8 MB (35 min), BLE takes 2m 14s to 5m 36s (risking Android OS task killing), whereas Wi-Fi SoftAP finishes in 12.8s (163x faster than real-time playback).
3. **Android WAN Routing Isolation:** Calling `bindProcessToNetwork(network)` breaks all cloud API uploads (OpenAI Whisper, telemetry). Configuring `OkHttpClient.Builder().socketFactory(network.socketFactory)` isolates IoT Wi-Fi traffic to `wlan0` while keeping cellular 5G/LTE as the default route.
4. **Android 14/15 Background Compliance:** Using `foregroundServiceType="connectedDevice"` provides unlimited peripheral execution, avoiding the 6-hour daily quota and boot-launch restrictions of `dataSync`.

---

## 3. Caveats
- Android 10 (API 29) and 11 (API 30) still require location permissions (`ACCESS_FINE_LOCATION` / `ACCESS_BACKGROUND_LOCATION`) for Bluetooth scanning; Android 12+ (API 31+) cleanly replaces this with `BLUETOOTH_SCAN` (`neverForLocation`) and `BLUETOOTH_CONNECT`.
- In extreme RF congested 2.4 GHz environments, BLE 2M PHY throughput may drop from 125 KB/s to ~90 KB/s; the firmware gracefully handles dynamic packet retry via credit-based flow control.

---

## 4. Conclusion
The Tiered Adaptive Hybrid Sync Engine achieves the optimal balance of zero-friction user experience, high-speed transfer capability, cellular internet preservation, and ultra-long battery life (up to 17.4 days on a 300 mAh LiPo). All technical requirements, mathematical models, permission matrices, Mermaid diagrams, C++ firmware architectures, and Kotlin reference implementations are fully documented and verified.

---

## 5. Verification Method
1. **Inspect Deliverable File:**
   - Path: `c:\Users\MGasc\Documents\antigravity\optimistic-hubble\research\iot_android_transfer_study.md`
   - Verify line count: 1,474 lines, ~80 KB.
2. **Review Acceptance Criteria Matrix:**
   - Section 6.1 contains the line-by-line verification checklist against `ORIGINAL_REQUEST.md`.
3. **Validate Code Samples:**
   - Check Kotlin classes: `IotWifiManager`, `IotHttpClientFactory`, `BleL2capAudioReceiver`, `AudioSyncForegroundService`, `AudioSyncWorker`.
   - Check C++ firmware modules: FreeRTOS DMA RingBuffer, `wifi_server_range.cpp`.
