SphaeroX/optimistic-hubble/.agents/teamwork_preview_worker_1/progress.md

# Progress Log - Worker 1 (Master Technical Study Compiler)

Last visited: 2026-08-20T13:43:20Z

## Status
- [x] Initialized DISPATCH.md and BRIEFING.md
- [x] Read source documents:
  - [x] ORIGINAL_REQUEST.md
  - [x] Explorer 1 analysis.md (BLE 5.0 2M PHY, DLE 251, L2CAP CoC vs GATT, Plaud Note AI / market analysis)
  - [x] Explorer 2 analysis.md (Android 10-15 WifiNetworkSpecifier, CompanionDeviceManager, multi-network socket routing, FGS connectedDevice)
  - [x] Explorer 3 analysis.md (ESP32-C3 RF coexistence, Flash I/O, power models for 150/300 mAh LiPo, Wi-Fi STA mDNS, chunked recovery protocol)
  - [x] Existing firmware in src/
- [x] Synthesized and compiled complete study to `research/iot_android_transfer_study.md` (1,474 lines, 80 KB)
- [x] Self-verified against all Acceptance Criteria
- [x] Created handoff.md report
- [x] Communicated completion to parent via send_message
