SphaeroX/optimistic-hubble/.agents/teamwork_preview_worker_2/DISPATCH.md

## 2026-08-20T13:46:31Z

Task: Deliverable Refinement & Code Hardening for Research & Architectural Study: Optimal IoT-to-Android Audio Sync (XIAO ESP32-C3).
Working Directory: c:\Users\MGasc\Documents\antigravity\optimistic-hubble\.agents\teamwork_preview_worker_2
Deliverable: c:\Users\MGasc\Documents\antigravity\optimistic-hubble\research\iot_android_transfer_study.md

Review & Challenge inputs:
1. .agents/teamwork_preview_reviewer_2/review.md
2. .agents/teamwork_preview_challenger_2/challenge_report.md
3. research/iot_android_transfer_study.md

Mandatory Refinements to Apply:
1. 32-Byte Header Fix (CRIT-01)
2. Genuine Production Logic in AudioSyncForegroundService.kt (CRIT-02)
3. Android 14/15 Compliant WorkManager in AudioSyncWorker.kt (MAJ-01)
4. Arduino WebServer Range Header Collection (MAJ-02)
5. ESP32 NimBLE L2CAP CoC C++ Firmware Reference Code (MAJ-03)
6. AndroidManifest.xml Reference Blueprint (MIN-01)
7. Stream IO & Partial Read Hardening in BleL2capAudioReceiver.kt (MIN-02)
8. Firmware I2S Timing & Flash Flush Hardening (MIN-03)
