SphaeroX/optimistic-hubble/.agents/teamwork_preview_worker_2/progress.md

# Progress Tracker - Worker 2

Last visited: 2026-08-20T13:48:38Z

- [x] Initialized workspace and briefing
- [x] Read review.md, challenge_report.md, and current iot_android_transfer_study.md
- [x] Draft hardening edits for all 8 technical refinements
- [x] Update iot_android_transfer_study.md with:
  - 32-Byte Header Fix in text, diagram, and Kotlin parser (CRIT-01)
  - Genuine production logic in AudioSyncForegroundService.kt (CRIT-02)
  - Android 14/15 Compliant WorkManager in AudioSyncWorker.kt (MAJ-01)
  - Arduino WebServer Range Header Collection and bounds validation in wifi_server_range.cpp (MAJ-02)
  - ESP32 NimBLE L2CAP CoC C++ reference code in nimble_l2cap_server.cpp (MAJ-03)
  - AndroidManifest.xml Reference Blueprint in Section 5.3.6 (MIN-01)
  - Stream IO & Partial Read Hardening in BleL2capAudioReceiver.kt (MIN-02)
  - Firmware I2S Timing fix, trailing sector flush, and SoftAP watchdog in Section 5.2 (MIN-03)
- [x] Verify integrity and thoroughness
- [x] Write handoff report and notify parent
