SphaeroX/optimistic-hubble/.agents/teamwork_preview_auditor_1/BRIEFING.md

# BRIEFING — 2026-08-20T13:46:00Z

## Mission
Forensic integrity audit of the Research & Architectural Study on Optimal IoT-to-Android Audio Sync for Seeed XIAO ESP32-C3 (`research/iot_android_transfer_study.md`).

## 🔒 My Identity
- Archetype: forensic_auditor
- Roles: critic, specialist, auditor
- Working directory: c:\Users\MGasc\Documents\antigravity\optimistic-hubble\.agents\teamwork_preview_auditor_1
- Original parent: ff5b3206-dca0-46f5-be4f-e7353b2157c6
- Target: research/iot_android_transfer_study.md

## 🔒 Key Constraints
- Audit-only — do NOT modify implementation code
- Trust NOTHING — verify everything independently
- Check for authenticity, completeness, facades, hardcoded results, and compliance with ORIGINAL_REQUEST.md

## Current Parent
- Conversation ID: ff5b3206-dca0-46f5-be4f-e7353b2157c6
- Updated: 2026-08-20T13:46:00Z

## Audit Scope
- **Work product**: `c:\Users\MGasc\Documents\antigravity\optimistic-hubble\research\iot_android_transfer_study.md`
- **Profile loaded**: General Project
- **Audit type**: Forensic Integrity Check & Acceptance Criteria Verification

## Audit Progress
- **Phase**: reporting
- **Checks completed**: [Authenticity Check, Placeholder/Facade Search, BLE Airtime & Throughput Math Verification, Audio Transfer Duration Validation, Power & Energy Crossover Modeling, Multi-Network SocketFactory Review, Android 14/15 Background Compliance Check, Acceptance Criteria 1-8 Cross-Verification]
- **Checks remaining**: []
- **Findings so far**: CLEAN — 0 integrity violations, 100% acceptance criteria satisfied.

## Key Decisions Made
- Confirmed full technical authenticity and mathematical accuracy of all tables, formulas, diagrams, and code implementations.
- Issued verdict CLEAN.

## Artifact Index
- `.agents/teamwork_preview_auditor_1/audit_report.md` — Detailed forensic audit report
- `.agents/teamwork_preview_auditor_1/handoff.md` — Handoff report with binary verdict

## Attack Surface
- **Hypotheses tested**: Checked for unhandled cellular disconnects, invalid Android 14/15 FGS types, erroneous airtime calculations, and stubbed code.
- **Vulnerabilities found**: None. All potential failure modes (e.g. `bindProcessToNetwork` cellular WAN loss, `dataSync` 6h timeout) were properly identified and resolved in the study.
- **Untested angles**: None within the scope of the architectural research.

## Loaded Skills
None required for standalone markdown analysis.
