SphaeroX/optimistic-hubble/.agents/teamwork_preview_auditor_1/handoff.md

# Handoff Report: Forensic Integrity Audit

**Auditor:** Auditor 1 (Forensic Integrity Auditor)  
**Deliverable Audited:** `c:\Users\MGasc\Documents\antigravity\optimistic-hubble\research\iot_android_transfer_study.md`  
**Verdict:** **CLEAN**  
**Timestamp:** 2026-08-20T13:46:00Z  

---

## 1. Observation
- Inspected the deliverable file `research/iot_android_transfer_study.md` (1,474 lines, 79,943 bytes).
- Conducted search for placeholders, stubs, and unfinished markers (`TODO`, `FIXME`, `TBD`, `placeholder`); returned 0 results.
- Verified all mathematical formulas and timing calculations:
  - Audio profiling: $16 \text{ kHz} \times 4 \text{ bits} = 64 \text{ kbps} = 8,000 \text{ B/s}$. File sizes: 480 KB (1 min), 2.4 MB (5 min), 4.8 MB (10 min), 16.8 MB (35 min).
  - BLE 2M PHY Link Layer frame airtime: $T_{\text{TX}} = 1064 \mu\text{s}$, $T_{\text{cycle}} = 1404 \mu\text{s}$, theoretical max rate $= 712.25 \text{ pkts/s}$, L2CAP CoC throughput $= 175.93 \text{ KB/s}$, GATT Notify throughput $= 173.79 \text{ KB/s}$.
  - Power consumption & energy crossover: BLE energy $= 0.0404 \text{ mAh/MB}$, Wi-Fi SoftAP $= 0.0208 \text{ mAh/MB} + 0.0826 \text{ mAh setup}$, yielding exact crossover at $S_{\text{cross}} = 4.21 \text{ MB}$ ($8.7 \text{ min audio}$).
- Verified all 4 Mermaid diagrams (Mode B Foreground SoftAP, Mode A Background L2CAP, RFC 7233 Range Recovery, Mode C Docked LAN Sync) are syntactically valid and accurately represent the communication sequence.
- Verified ESP32-C3 C++ code (FreeRTOS Dual-Task RingBuffer, LittleFS HTTP 206 Partial Content server, 30-byte `SyncChunkHeader`) and Android Kotlin code (`IotWifiManager`, `IotHttpClientFactory`, `BleL2capAudioReceiver`, `AudioSyncForegroundService`, `AudioSyncWorker`).
- Verified multi-network routing isolation using `OkHttpClient.Builder().socketFactory(network.socketFactory)` to preserve mobile 5G/LTE connectivity.
- Verified Android 14/15 background compliance using `FOREGROUND_SERVICE_TYPE_CONNECTED_DEVICE` rather than timeout-prone `dataSync`.

## 2. Logic Chain
1. **Authenticity:** All content, tables, models, and code blocks represent genuine, deeply researched technical artifacts without dummy implementations or facade wrappers.
2. **Mathematical Consistency:** The calculations for physical radio airtime, transfer durations, battery draw, and file size distributions are mathematically rigorous and consistent across all sections.
3. **Acceptance Criteria Fulfillment:** Each of the 8 Acceptance Criteria from `ORIGINAL_REQUEST.md` was cross-referenced directly with corresponding sections in the deliverable. Every criterion passed without deficiency.
4. **Conclusion Derivation:** Because all forensic integrity checks passed and all acceptance criteria are fully satisfied, the work product is rated CLEAN.

## 3. Caveats
- No caveats. The research study thoroughly covers theoretical limits, laboratory measurements, field anomalies, vendor-specific BLE connection interval clamping, and modern Android OS background restrictions (API 29 through API 35+).

## 4. Conclusion
The deliverable `research/iot_android_transfer_study.md` is **CLEAN**, publication-grade, and ready for immediate downstream engineering and firmware/app development.

## 5. Verification Method
1. Inspect the deliverable file:
   ```bash
   view_file research/iot_android_transfer_study.md
   ```
2. Verify lack of placeholder markers:
   ```bash
   grep -inE "TODO|FIXME|TBD|placeholder" research/iot_android_transfer_study.md
   ```
3. Check the audit report:
   ```bash
   view_file .agents/teamwork_preview_auditor_1/audit_report.md
   ```
