SphaeroX/optimistic-hubble/.agents/teamwork_preview_challenger_1/progress.md

# Progress Log — Challenger 1 (Mathematical & Benchmark Challenger)

- **Status**: Completed
- **Last visited**: 2026-08-20T13:46:30Z
- **Current Phase**: Handoff & Notification

## Completed Steps
- [x] Step 1: Ingest ORIGINAL_REQUEST.md and research/iot_android_transfer_study.md
- [x] Step 2: Initialize BRIEFING.md, DISPATCH.md, and progress.md
- [x] Step 3: Write comprehensive Python mathematical verification script to recompute all derivations and tables
- [x] Step 4: Execute verification test harness and collect empirical discrepancies/confirmation
- [x] Step 5: Stress-test boundary conditions and model assumptions (RF congestion, battery degradation, ringbuffer safety)
- [x] Step 6: Compile challenge_report.md and handoff.md with explicit verdict APPROVE
- [x] Step 7: Send final message to parent agent
