SphaeroX/optimistic-hubble/.agents/teamwork_preview_challenger_2/BRIEFING.md

# BRIEFING — 2026-08-20T13:45:38Z

## Mission
Adversarial protocol stress-testing and edge-case challenge of the IoT-to-Android Audio Sync architectural study (XIAO ESP32-C3).

## 🔒 My Identity
- Archetype: empirical challenger
- Roles: critic, specialist
- Working directory: c:\Users\MGasc\Documents\antigravity\optimistic-hubble\.agents\teamwork_preview_challenger_2
- Original parent: ff5b3206-dca0-46f5-be4f-e7353b2157c6
- Milestone: protocol-stress-challenge
- Instance: 1 of 1

## 🔒 Key Constraints
- Review-only — do NOT modify implementation code directly unless running tests/simulation scripts in workspace.
- Provide empirical verification and calculation/scenario models for each challenged area.
- Explicit verdict: APPROVE or REQUEST_CHANGES in handoff.md.

## Current Parent
- Conversation ID: ff5b3206-dca0-46f5-be4f-e7353b2157c6
- Updated: 2026-08-20T13:45:38Z

## Review Scope
- **Files reviewed**:
  - `c:\Users\MGasc\Documents\antigravity\optimistic-hubble\ORIGINAL_REQUEST.md`
  - `c:\Users\MGasc\Documents\antigravity\optimistic-hubble\research\iot_android_transfer_study.md`
- **Challenge questions completed**:
  1. Mid-transfer dropouts & RFC 7233 / 30B vs 32B binary chunk header atomic recovery (FAIL - BufferUnderflow & struct mismatch found)
  2. Multi-network routing & OkHttpClient socket factory / cellular 5G/LTE isolation (PASS - Verified)
  3. Android OS background termination & connectedDevice FGS under Android 14/15 restrictions (FAIL - FGS launch from Worker anti-pattern identified)
  4. Coexistence single-antenna contention & sequential state machine (PASS on RF isolation, FAIL on missing SoftAP timeout watchdog)
  5. LittleFS flash erase latency vs FreeRTOS 16KB DMA ring buffer (PASS on 5.12x headroom, FAIL on vTaskDelay I2S overrun)

## Attack Surface
- **Hypotheses tested**: 5 primary architectural dimensions and code paths.
- **Vulnerabilities found**: 6 concrete issues documented in challenge_report.md and handoff.md.
- **Untested angles**: Hardware-in-the-loop physical bench test (simulated via empirical calculations).

## Key Decisions Made
- Verdict rendered: **REQUEST_CHANGES** with 6 concrete remediation recommendations.

## Artifact Index
- `.agents/teamwork_preview_challenger_2/DISPATCH.md` — Inbound dispatches
- `.agents/teamwork_preview_challenger_2/BRIEFING.md` — Context & identity
- `.agents/teamwork_preview_challenger_2/progress.md` — Liveness & heartbeat
- `.agents/teamwork_preview_challenger_2/challenge_report.md` — Detailed stress test report
- `.agents/teamwork_preview_challenger_2/handoff.md` — Final handoff & verdict
