SphaeroX/optimistic-hubble/.agents/teamwork_preview_explorer_1/BRIEFING.md

# BRIEFING — 2026-08-20T13:40:20Z

## Mission
Conduct exhaustive technical investigation into BLE 5.0 high-throughput mechanics, realistic throughput limits/benchmarks on ESP32-C3 vs modern Android, audio transfer time modeling for 8 KB/s IMA-ADPCM, and market reference analysis (Plaud Note AI, Senstone, Mobvoi) to determine optimal audio sync architecture.

## 🔒 My Identity
- Archetype: explorer
- Roles: ble-5-throughput-analyst, market-reference-analyst
- Working directory: c:\Users\MGasc\Documents\antigravity\optimistic-hubble\.agents\teamwork_preview_explorer_1
- Original parent: ff5b3206-dca0-46f5-be4f-e7353b2157c6
- Milestone: Phase 1 Deep Technical Survey & Exploration

## 🔒 Key Constraints
- Read-only investigation — do NOT implement code
- Follow strict 5-component handoff format in handoff.md
- Produce comprehensive analysis.md
- Send completion message to parent via send_message

## Current Parent
- Conversation ID: ff5b3206-dca0-46f5-be4f-e7353b2157c6
- Updated: 2026-08-20T13:40:20Z

## Investigation State
- **Explored paths**: BLE 5.0 2M PHY, DLE 251, MTU 512, L2CAP CoC vs GATT notify, Android CI limits (Pixel/Samsung/Xiaomi), 8 KB/s IMA-ADPCM audio transfer modeling, Plaud Note AI dual-mode reverse engineering.
- **Key findings**: 
  - Pure BLE 2M PHY GATT achieves 90-105 KB/s net, L2CAP CoC achieves 115-130 KB/s net on ESP32-C3.
  - Wi-Fi 4 SoftAP achieves 1,600-2,000 KB/s (1.8 MB/s avg).
  - For < 1 MB audio (< 2 min), BLE 2M PHY is fastest & lowest friction (3.8-5.0s transfer).
  - For > 1 MB audio (up to 16.8 MB / 35 min), Wi-Fi SoftAP is mandatory (12.8s vs 2m14s-5m36s on BLE).
- **Unexplored areas**: None within Explorer 1 scope.

## Key Decisions Made
- Confirmed that hybrid dynamic switching (BLE signaling + dynamic Wi-Fi SoftAP triggered by payload size threshold of ~1.0 MB) represents the optimal industry-standard architecture, mirroring Plaud Note AI.

## Artifact Index
- analysis.md — Full technical deep-dive report
- progress.md — Liveness heartbeat and milestone tracking
- handoff.md — 5-component handoff report for parent agent
