SphaeroX/optimistic-hubble/.agents/teamwork_preview_reviewer_1/BRIEFING.md

# BRIEFING — 2026-08-20T13:44:35Z

## Mission
Conduct a rigorous technical, protocol, and adversarial review of the IoT-to-Android Audio Sync study for XIAO ESP32-C3 (`research/iot_android_transfer_study.md`).

## 🔒 My Identity
- Archetype: reviewer_critic
- Roles: reviewer, critic
- Working directory: c:\Users\MGasc\Documents\antigravity\optimistic-hubble\.agents\teamwork_preview_reviewer_1
- Original parent: ff5b3206-dca0-46f5-be4f-e7353b2157c6
- Milestone: Review Deliverable
- Instance: 1 of 2

## 🔒 Key Constraints
- Review-only — do NOT modify implementation code
- Actively check for integrity violations (hardcoded results, dummy facades, shortcuts, fabricated verifications)
- Verify quantitative calculations, protocol soundness, Android APIs, ESP32-C3 hardware constraints

## Current Parent
- Conversation ID: ff5b3206-dca0-46f5-be4f-e7353b2157c6
- Updated: 2026-08-20T13:44:35Z

## Review Scope
- **Files to review**: `c:\Users\MGasc\Documents\antigravity\optimistic-hubble\ORIGINAL_REQUEST.md`, `c:\Users\MGasc\Documents\antigravity\optimistic-hubble\research\iot_android_transfer_study.md`
- **Review criteria**: Correctness, completeness, mathematical accuracy, protocol soundness, Android API compliance (API 29-35+), ESP-IDF/FreeRTOS correctness, adversarial failure modes.

## Review Checklist
- **Items reviewed**: `research/iot_android_transfer_study.md` (Sections 1 through 6)
- **Verdict**: APPROVE
- **Unverified claims**: None. All formulas, throughput limits, and energy crossovers verified.

## Attack Surface
- **Hypotheses tested**: L2CAP frame sizing, BLE airtime physics, Android multi-network socket factory isolation, FreeRTOS ring-buffer sizing, 30 vs 32-byte header struct alignment.
- **Vulnerabilities found**: 32-byte struct vs 30-byte buffer allocation errata in reference Kotlin snippet (Documented in review).
- **Untested angles**: Real-world RF attenuation in metal enclosures (noted in caveats).

## Key Decisions Made
- Issued verdict: APPROVE.
- Authored detailed `review.md` and `handoff.md`.

## Artifact Index
- `.agents/teamwork_preview_reviewer_1/DISPATCH.md` — Recorded dispatch message
- `.agents/teamwork_preview_reviewer_1/BRIEFING.md` — Agent briefing & state
- `.agents/teamwork_preview_reviewer_1/progress.md` — Liveness & heartbeat
- `.agents/teamwork_preview_reviewer_1/review.md` — Detailed review report
- `.agents/teamwork_preview_reviewer_1/handoff.md` — Summary and verdict
