SphaeroX/optimistic-hubble/.agents/teamwork_preview_reviewer_2/handoff.md

# Handoff Report: Reviewer 2 (Android & Firmware Implementation Review)

**Agent:** Reviewer 2 (`teamwork_preview_reviewer_2`)  
**Target:** `research/iot_android_transfer_study.md`  
**Date:** 2026-08-20  
**Verdict:** **REQUEST_CHANGES**

---

## 1. Observation

Direct code and structural observations from `research/iot_android_transfer_study.md`:

1. **Header Size Definition vs Kotlin Buffer Allocation:**
   - Section 4.3.1 (lines 665-679): `struct SyncChunkHeader` contains 11 fields totaling **32 bytes** ($2 + 1 + 1 + 4 + 4 + 4 + 2 + 2 + 4 + 4 + 4 = 32$).
   - Section 5.3.3 (`BleL2capAudioReceiver.kt`, lines 1187–1216):
     ```kotlin
     val headerBuffer = ByteBuffer.allocate(30).order(ByteOrder.LITTLE_ENDIAN)
     // ... reads 30 bytes ...
     val chunkCrc32 = headerBuffer.int.toLong() and 0xFFFFFFFFL // pos: 28
     val expectedFileCrc32 = headerBuffer.int.toLong() and 0xFFFFFFFFL // pos: 32 -> Crashes with BufferUnderflowException
     ```
2. **Dummy Implementation in Foreground Service:**
   - Section 5.3.4 (`AudioSyncForegroundService.kt`, line 1317):
     ```kotlin
     serviceScope.launch {
         try {
             // Perform BLE L2CAP or Wi-Fi sync execution
             delay(4000)
         } ...
     }
     ```
     Contains a simulated dummy timer instead of invoking actual sync receivers.
3. **WorkManager Lifecycle Decoupling:**
   - Section 5.3.5 (`AudioSyncWorker.kt`, lines 1392–1404):
     `AudioSyncWorker.doWork()` starts the service and immediately returns `Result.success()`, causing WorkManager to drop its wake-lock before the peripheral connects.
4. **Omitted WebServer Header Collection:**
   - Section 5.2.2 (`wifi_server_range.cpp`, lines 905–941):
     `server.hasHeader("Range")` is queried without `server.collectHeaders()`, causing it to always return `false` on ESP32 Arduino WebServer.
5. **Missing NimBLE L2CAP Server C++ Blueprint:**
   - Section 5.2 provides FreeRTOS audio capture and WebServer HTTP Range code, but completely omits the C++ implementation for the NimBLE L2CAP CoC peripheral server.

---

## 2. Logic Chain

1. **Observation 1 $\rightarrow$ Critical Defect:** `BleL2capAudioReceiver.kt` allocates 30 bytes for a 32-byte header struct and attempts to read 32 bytes from the buffer. This triggers a guaranteed `java.nio.BufferUnderflowException` on every single received L2CAP chunk, breaking Tier 1 audio streaming at runtime.
2. **Observation 2 $\rightarrow$ Integrity Violation:** `AudioSyncForegroundService.kt` uses `delay(4000)` rather than executing real transfer logic. Under the Teamwork integrity rules, facade/dummy implementations constitute an integrity violation requiring a `REQUEST_CHANGES` verdict.
3. **Observation 3 $\rightarrow$ Architectural Defect:** Premature return of `Result.success()` in `AudioSyncWorker.kt` unbinds WorkManager from the foreground service, exposing the process to background termination on Android 12–15.
4. **Observation 4 $\rightarrow$ Protocol Defect:** Without `server.collectHeaders(header_keys, count)` in `wifi_server_range.cpp`, Arduino ESP32 `WebServer` ignores incoming `Range: bytes=X-` request headers, breaking RFC 7233 resume functionality.
5. **Observation 5 $\rightarrow$ Completeness Gap:** The study mandates BLE L2CAP CoC as the primary Tier 1 protocol, but omits the ESP32-C3 C++ server implementation.

---

## 3. Caveats

- **RF Hardware Coexistence:** Throughput and airtime models assume standard ESP32-C3 RF performance with single-antenna TDM. Extreme 2.4 GHz RF congestion (e.g. crowded office) may lower net throughput further.
- **Android OEM Variance:** While standard AOSP behavior is evaluated across API 29–35+, aggressive OEM battery kill daemons (e.g., Samsung Sleeping Apps, Xiaomi MIUI Battery Saver) require Companion Device Manager (CDM) association to achieve 100% background reliability.

---

## 4. Conclusion

The core theoretical analysis, mathematical airtime modeling, energy crossover derivations, and architectural design in `research/iot_android_transfer_study.md` are top-tier and publication-ready. However, the reference implementation contains critical runtime bugs (30 vs 32-byte `BufferUnderflowException`), an integrity violation (dummy `delay(4000)` in `AudioSyncForegroundService`), and missing firmware blueprints (NimBLE L2CAP CoC C++ code).

**Verdict:** **REQUEST_CHANGES**

---

## 5. Verification Method

1. **Header Size Verification:**
   - Inspect `struct SyncChunkHeader` in Section 4.3.1. Sum field byte lengths ($2+1+1+4+4+4+2+2+4+4+4 = 32$).
   - Inspect `BleL2capAudioReceiver.kt` lines 1187 & 1216. Verify `ByteBuffer.allocate(32)` is used and all 11 fields are extracted without buffer underflow.
2. **Foreground Service Logic Verification:**
   - Inspect `AudioSyncForegroundService.kt` line 1317. Verify `delay(4000)` is replaced with real invocation of `BleL2capAudioReceiver` / `IotWifiManager`.
3. **Arduino WebServer Header Collection:**
   - Check `wifi_server_range.cpp`. Verify `server.collectHeaders(...)` is invoked during setup before checking `server.hasHeader("Range")`.
4. **Firmware Blueprint Completeness:**
   - Verify that `nimble_l2cap_server.cpp` is included in Section 5.2 demonstrating `ble_l2cap_create_server()` and data transmission over `os_mbuf`.
