SphaeroX/optimistic-hubble/.agents/teamwork_preview_reviewer_3/DISPATCH.md

## 2026-08-20T13:49:31Z
You are Reviewer 3 (Re-Verification of Reference Implementation & Android 14/15 Compliance) for the Research & Architectural Study: Optimal IoT-to-Android Audio Sync (XIAO ESP32-C3).

Your working directory is: c:\Users\MGasc\Documents\antigravity\optimistic-hubble\.agents\teamwork_preview_reviewer_3
The user requirements are in: c:\Users\MGasc\Documents\antigravity\optimistic-hubble\ORIGINAL_REQUEST.md
The updated deliverable is in: c:\Users\MGasc\Documents\antigravity\optimistic-hubble\research\iot_android_transfer_study.md
Previous review report: c:\Users\MGasc\Documents\antigravity\optimistic-hubble\.agents\teamwork_preview_reviewer_2\review.md

You MUST read ORIGINAL_REQUEST.md, research/iot_android_transfer_study.md, and the previous review report.

Re-verify that all 8 findings from Reviewer 2 have been fully and properly resolved in `research/iot_android_transfer_study.md`:
1. CRIT-01: 32-byte header struct sizing (in text, tables, and `BleL2capAudioReceiver.kt` ByteBuffer/loop reads).
2. CRIT-02: Genuine production logic in `AudioSyncForegroundService.kt` (no delay(4000) mock).
3. MAJ-01: Native `CoroutineWorker` execution in `AudioSyncWorker.kt` using `setForeground(createForegroundInfo())` with `FOREGROUND_SERVICE_TYPE_CONNECTED_DEVICE`.
4. MAJ-02: `server.collectHeaders(HTTP_COLLECT_HEADERS, 2)` and Range bounds validation in `wifi_server_range.cpp`.
5. MAJ-03: Full ESP32 NimBLE L2CAP CoC C++ reference code (`nimble_l2cap_server.cpp`) in Section 5.2.3.
6. MIN-01: Production `AndroidManifest.xml` reference snippet in Section 5.3.6.
7. MIN-02: Stream IO hardening in `BleL2capAudioReceiver.kt` (`.part` file resume appending, bad chunk dropping).
8. MIN-03: I2S timing fix (removed `vTaskDelay(2)`) and trailing buffer flush in `audio_ringbuffer_engine.cpp`, plus 60-second SoftAP watchdog timer.

Write your review to `.agents/teamwork_preview_reviewer_3/review.md` and your verdict (APPROVE / REQUEST_CHANGES) in `.agents/teamwork_preview_reviewer_3/handoff.md`.
Communicate your verdict to parent via send_message.
