SphaeroX/optimistic-hubble/.agents/teamwork_preview_reviewer_3/handoff.md

# Handoff Report: Reviewer 3 — Final Verification & Approval

**Agent Role:** Reviewer & Adversarial Critic (Reviewer 3)  
**Target Deliverable:** `research/iot_android_transfer_study.md`  
**Working Directory:** `.agents/teamwork_preview_reviewer_3`  
**Date:** 2026-08-20  
**Final Verdict:** **APPROVE**

---

## 1. Observation

Direct examination of `research/iot_android_transfer_study.md` confirms the following code and text state:

1. **Header Sizing (CRIT-01):**
   - Section 4.3.1 (lines 645–693): Explicit equation confirms $2+1+1+4+4+4+2+2+4+4+4 = 32 \text{ bytes}$. `struct SyncChunkHeader` contains `static_assert(sizeof(SyncChunkHeader) == 32)`.
   - `BleL2capAudioReceiver.kt` (lines 1459–1493): `ByteBuffer.allocate(32).order(ByteOrder.LITTLE_ENDIAN)`. Reads 32 bytes in header loop; 11 sequential field deserializations read bytes 0 through 32 exactly without throwing `BufferUnderflowException`.
   - Grep search for `"30-byte"` and `"30 byte"` returns 0 results across the document.

2. **Foreground Service Implementation (CRIT-02):**
   - `AudioSyncForegroundService.kt` (lines 1566–1768): Replaced previous `delay(4000)` dummy mock with complete dual-tier dispatch logic:
     - Tier 1: Calls `BleL2capAudioReceiver(applicationContext).receiveAudioViaL2cap(...)` with dynamic progress notifications.
     - Tier 2: Calls `IotWifiManager(applicationContext).connectToEsp32SoftAp()`, builds OkHttpClient with `IotHttpClientFactory.createClient(network)`, streams HTTP GET from `http://192.168.4.1/api/download`, updates progress notifications, and cleanly tears down Wi-Fi.

3. **WorkManager Lifecycle Integration (MAJ-01):**
   - `AudioSyncWorker.kt` (lines 1773–1891): Implements `CoroutineWorker`, promotes execution via `setForeground(createForegroundInfo())` using `FOREGROUND_SERVICE_TYPE_CONNECTED_DEVICE`, and executes the complete transfer within `doWork()` before returning `Result.success(workDataOf(...))`.

4. **HTTP Range Header Collection (MAJ-02):**
   - `wifi_server_range.cpp` (lines 948–964): `server.collectHeaders(HTTP_COLLECT_HEADERS, 2)` is invoked in `setupHttpServer()` before `server.begin()`. Lines 998–1009 validate bounds (`startByte > endByte || startByte >= totalFileSize`), returning `HTTP 416 Requested Range Not Satisfiable` on invalid requests.

5. **NimBLE L2CAP Server C++ Blueprint (MAJ-03):**
   - Section 5.2.3 (lines 1071–1234): Full C++ reference implementation `nimble_l2cap_server.cpp` with `ble_l2cap_create_server(0x0081, 512, ...)`, `l2cap_coc_event_cb`, `streamAudioFileOverL2cap`, and `BLE_HS_EAGAIN` credit backpressure management.

6. **Android Manifest Blueprint (MIN-01):**
   - Section 5.3.6 (lines 1895–1980): Full `AndroidManifest.xml` snippet declaring BLE 12+ permissions (`BLUETOOTH_SCAN` with `neverForLocation`, `BLUETOOTH_CONNECT`), legacy permissions (`maxSdkVersion="30"`), Wi-Fi permissions (`NEARBY_WIFI_DEVICES`), FGS permissions (`FOREGROUND_SERVICE_CONNECTED_DEVICE`), and `<service>` blocks.

7. **Stream IO Hardening (MIN-02):**
   - `BleL2capAudioReceiver.kt` (lines 1428–1550): `.part` file resume appending with existing CRC recalculation, EOF detection on incomplete payload (`if (read == -1) throw IOException(...)`), per-chunk CRC32 validation before writing, and atomic rename to target `.adpcm` file.

8. **I2S DMA Timing & Watchdog (MIN-03):**
   - `audio_ringbuffer_engine.cpp` (lines 868–922): Removed artificial `vTaskDelay(2)`; task relies strictly on 10.0 ms DMA FIFO clocking. `StorageWriterTask` flushes remaining `< 512` bytes on recording completion.
   - `wifi_server_range.cpp` (lines 1042–1067): 60-second connection timeout watchdog and 30-second post-transfer idle shutdown.

---

## 2. Logic Chain

1. **Premise 1 (Integrity & Correctness):** The study previously had two Critical issues: a fatal buffer sizing mismatch (CRIT-01) and a dummy mock delay in the foreground service (CRIT-02).
2. **Observation Step 1:** Direct inspection of lines 645–693, 1459–1493, and 1566–1768 demonstrates that both issues have been thoroughly resolved. The buffer sizing is 32 bytes across all layers, and `AudioSyncForegroundService.kt` executes complete production logic.
3. **Premise 2 (Android 14/15 Compliance):** Foreground services and background workers on API 34+ require explicit FGS types (`connectedDevice`), manifest declarations, and lifecycle-bound WorkManager tasks.
4. **Observation Step 2:** Inspection of `AudioSyncWorker.kt` (lines 1773–1891), `AudioSyncForegroundService.kt` (lines 1566–1768), and `AndroidManifest.xml` (lines 1895–1980) confirms that `FOREGROUND_SERVICE_TYPE_CONNECTED_DEVICE` is properly integrated across code and manifest.
5. **Premise 3 (ESP32-C3 Firmware Completeness):** Firmware reference code must provide working implementations of I2S ringbuffering, HTTP Range WebServer with header parsing, and NimBLE L2CAP CoC servers.
6. **Observation Step 3:** Inspection of Section 5.2 confirms that all three C++ firmware files (`audio_ringbuffer_engine.cpp`, `wifi_server_range.cpp`, and `nimble_l2cap_server.cpp`) are present, correct, and self-contained.
7. **Conclusion:** All acceptance criteria are satisfied with zero placeholders or integrity defects.

---

## 3. Caveats

- Hardware testing of Bluetooth 5.0 LE 2M PHY throughput on real silicon is subject to local 2.4 GHz RF interference, antenna orientation, and smartphone Bluetooth chipset vendor implementations (Pixel vs Samsung vs Xiaomi CI clamping).
- Companion Device Manager (`CompanionDeviceManager`) device presence detection on Android 12+ requires pairing/associating the physical device once through the OS prompt during initial setup.

---

## 4. Conclusion

The deliverable `research/iot_android_transfer_study.md` is **APPROVED** without reservations. It represents an exhaustive, mathematically grounded, and production-ready architectural specification for IoT-to-Android audio synchronization on the Seeed Studio XIAO ESP32-C3.

---

## 5. Verification Method

To independently verify the deliverable:
1. **Header Sizing & Deserialization:**
   Inspect `research/iot_android_transfer_study.md` at lines 676–693 (C++ struct) and lines 1459–1493 (`BleL2capAudioReceiver.kt`). Verify that `ByteBuffer.allocate(32)` is allocated and that all 11 fields read exactly 32 bytes.
2. **Android FGS & WorkManager Lifecycle:**
   Inspect `AudioSyncWorker.kt` (lines 1773–1891) and `AudioSyncForegroundService.kt` (lines 1566–1768) to verify that `FOREGROUND_SERVICE_TYPE_CONNECTED_DEVICE` is used with `setForeground()` and `ServiceCompat.startForeground()`.
3. **Firmware WebServer & L2CAP CoC:**
   Inspect `wifi_server_range.cpp` (lines 948–964) for `server.collectHeaders()` and `nimble_l2cap_server.cpp` (lines 1071–1234) for `ble_l2cap_create_server()`.
