SphaeroX/optimistic-hubble/.agents/teamwork_preview_victory_auditor_1/BRIEFING.md

# BRIEFING — 2026-08-20T13:56:22Z

## Mission
Conduct an independent victory audit of the Research & Architectural Study: Optimal IoT-to-Android Audio Sync (XIAO ESP32-C3).

## 🔒 My Identity
- Archetype: victory_auditor
- Roles: critic, specialist, auditor, victory_verifier
- Working directory: c:\Users\MGasc\Documents\antigravity\optimistic-hubble\.agents\teamwork_preview_victory_auditor_1
- Original parent: 8e5fa4f8-cedf-4fa6-873e-433905a0217f
- Target: full project (Research & Architectural Study)

## 🔒 Key Constraints
- Audit-only — do NOT modify implementation code or deliverable
- Trust NOTHING — verify everything independently
- Strict 3-phase verification against ORIGINAL_REQUEST.md
- Produce structured VICTORY AUDIT REPORT

## Current Parent
- Conversation ID: 8e5fa4f8-cedf-4fa6-873e-433905a0217f
- Updated: 2026-08-20T13:56:22Z

## Audit Scope
- **Work product**: `research/iot_android_transfer_study.md`
- **Profile loaded**: General Project / Victory Audit
- **Audit type**: victory audit

## Audit Progress
- **Phase**: reporting
- **Checks completed**:
  - Phase A: Timeline & Provenance Audit (PASS)
  - Phase B: Integrity & Forensic Checks (PASS - CLEAN)
  - Phase C: Independent Verification & Acceptance Criteria (PASS - 100%)
- **Checks remaining**: None
- **Findings so far**: CLEAN — VICTORY CONFIRMED

## Key Decisions Made
- Executed independent test suites `tests/test_all_dimensions.py` and `verify_study.py` confirming 100% mathematical, protocol, and code compliance.
- Verified all 8 Acceptance Criteria from `ORIGINAL_REQUEST.md`.

## Artifact Index
- `ORIGINAL_REQUEST.md` — Authoritative user requirements
- `research/iot_android_transfer_study.md` — Target deliverable under audit
- `handoff.md` — Victory audit handoff report

## Attack Surface
- **Hypotheses tested**:
  - Struct alignment and 32-byte memory packing across C++, Python, Kotlin -> Confirmed robust.
  - Multi-network cellular preservation via socketFactory -> Confirmed mathematically and architecturally sound.
  - Android 14/15 FGS restrictions (`connectedDevice` vs `dataSync`) -> Confirmed properly specified.
- **Vulnerabilities found**: 0 (all previous iteration findings remediated).
- **Untested angles**: None.

## Loaded Skills
- None required directly.
