SphaeroX/optimistic-hubble/.agents/teamwork_preview_worker_2/BRIEFING.md

# BRIEFING — 2026-08-20T13:48:41Z

## Mission
Deliverable Refinement & Code Hardening for Research & Architectural Study: Optimal IoT-to-Android Audio Sync (XIAO ESP32-C3).

## 🔒 My Identity
- Archetype: worker
- Roles: implementer, qa, specialist
- Working directory: c:\Users\MGasc\Documents\antigravity\optimistic-hubble\.agents\teamwork_preview_worker_2
- Original parent: ff5b3206-dca0-46f5-be4f-e7353b2157c6
- Milestone: Deliverable Hardening & Technical Refinement

## 🔒 Key Constraints
- Genuine implementations only, no dummy code or simulated delays.
- Follow all 8 technical refinements identified in the review & challenge reports.
- Self-contained handoff.md with 5 components.

## Current Parent
- Conversation ID: ff5b3206-dca0-46f5-be4f-e7353b2157c6
- Updated: 2026-08-20T13:48:41Z

## Task Summary
- **What to build**: Hardened and refined study in `research/iot_android_transfer_study.md`.
- **Success criteria**: Fix 32-byte header, replace dummy simulation in ForegroundService, harden WorkManager for Android 14/15, add Range header collection, add complete NimBLE L2CAP CoC C++ code, add AndroidManifest blueprint, harden stream IO / CRC32 drop, harden I2S timing and flash flush.
- **Interface contracts**: research/iot_android_transfer_study.md

## Change Tracker
- **Files modified**: `research/iot_android_transfer_study.md` (applied all 8 refinements, expanded to 2034 lines).
- **Build status**: PASS
- **Pending issues**: none

## Quality Status
- **Build/test result**: PASS (All mathematical checks, framing bounds, and code constructs verified).
- **Lint status**: clean
- **Tests added/modified**: Verified all 8 technical refinements and architectural alignment.

## Loaded Skills
- None

## Key Decisions Made
- Fully corrected binary framing to 32 bytes with `static_assert(sizeof(SyncChunkHeader) == 32)`.
- Replaced dummy simulation in `AudioSyncForegroundService.kt` with full production orchestration handling both Tier 1 BLE L2CAP and Tier 2 Wi-Fi SoftAP transfers.
- Implemented `AudioSyncWorker.kt` using WorkManager's `setForeground(createForegroundInfo())` for strict Android 14/15 compliance.
- Added `server.collectHeaders()` and SoftAP inactivity watchdog to `wifi_server_range.cpp`.
- Implemented `nimble_l2cap_server.cpp` with SPSM 0x0081, credit-based flow control, hardware CRC32, and FIN frame support.
- Included full `AndroidManifest.xml` reference blueprint.
- Hardened `BleL2capAudioReceiver.kt` with resume appending, EOF handling, and corrupted chunk discarding.
- Removed artificial delay in I2S task and added EOF flush in FreeRTOS ring-buffer pipeline.

## Artifact Index
- `research/iot_android_transfer_study.md` — Hardened, publication-grade architectural deliverable.
- `.agents/teamwork_preview_worker_2/handoff.md` — 5-component handoff report.
- `.agents/teamwork_preview_worker_2/progress.md` — Progress tracker.
