SphaeroX/optimistic-hubble/research/enclosure/bild2_offen.png

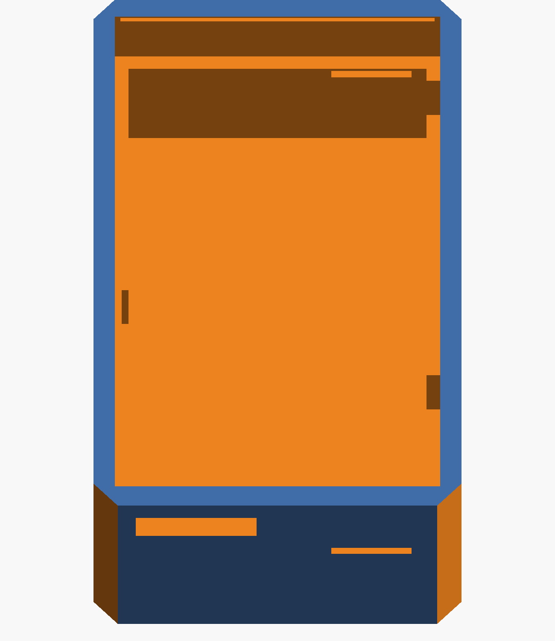
research/enclosure/bild2_offen.png
