SphaeroX/optimistic-hubble/research/enclosure/bild3_ruecken.png

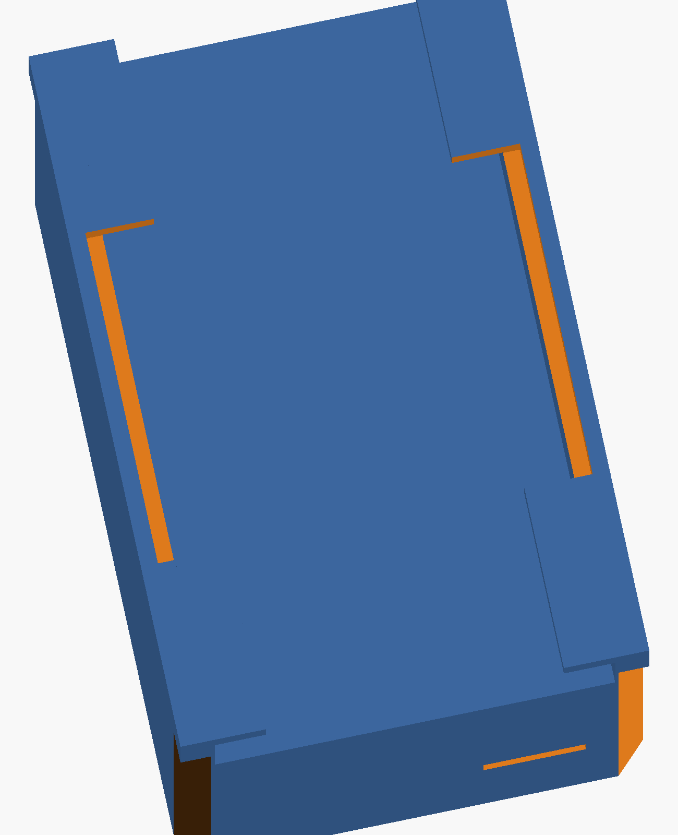
research/enclosure/bild3_ruecken.png
