SphaeroX/optimistic-hubble/research/enclosure/bild4_schnitt_mitte.png

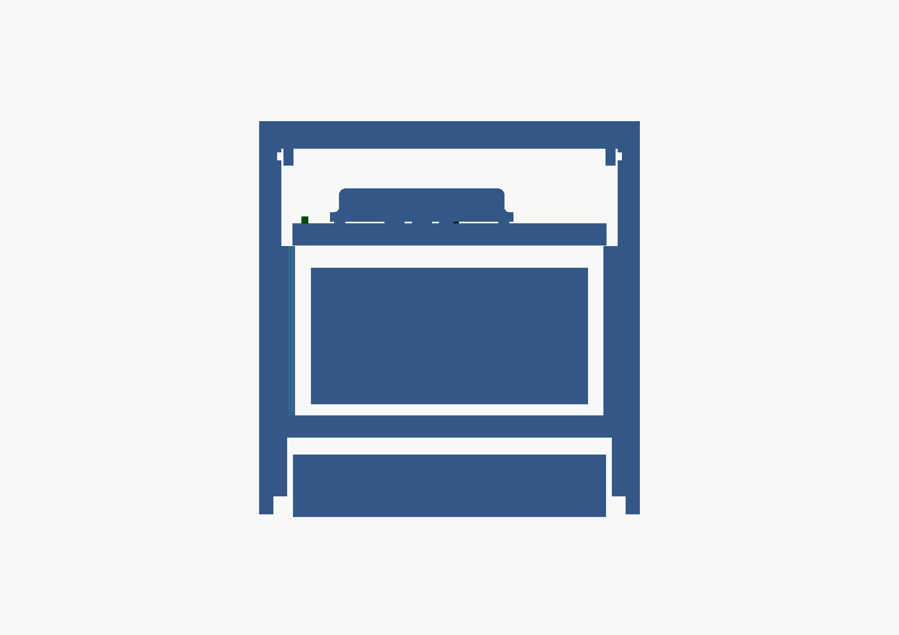
research/enclosure/bild4_schnitt_mitte.png
