SphaeroX/optimistic-hubble/research/enclosure/bild5_schnitt_usb.png

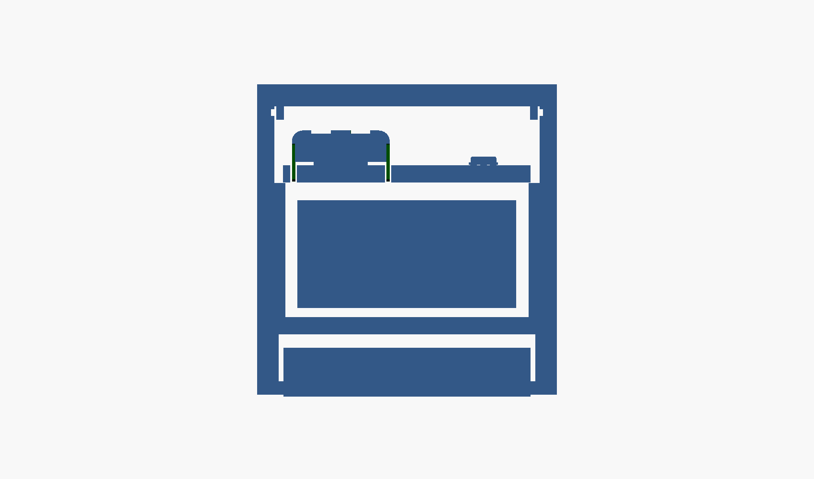
research/enclosure/bild5_schnitt_usb.png
