SphaeroX/optimistic-hubble/research/enclosure/bild6_schnitt_mic.png

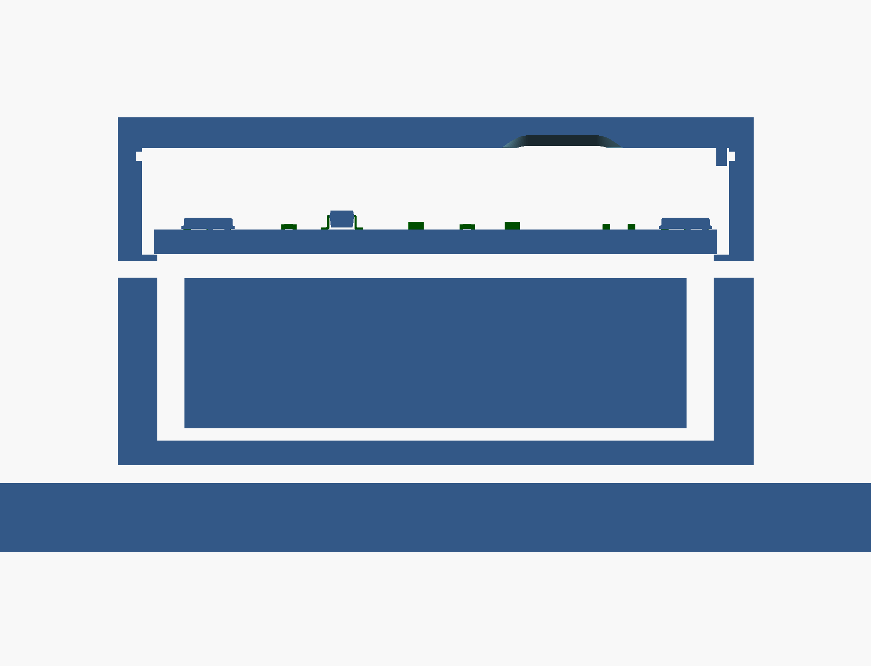
research/enclosure/bild6_schnitt_mic.png
