SphaeroX/optimistic-hubble/research/enclosure/bild7_deckel.png

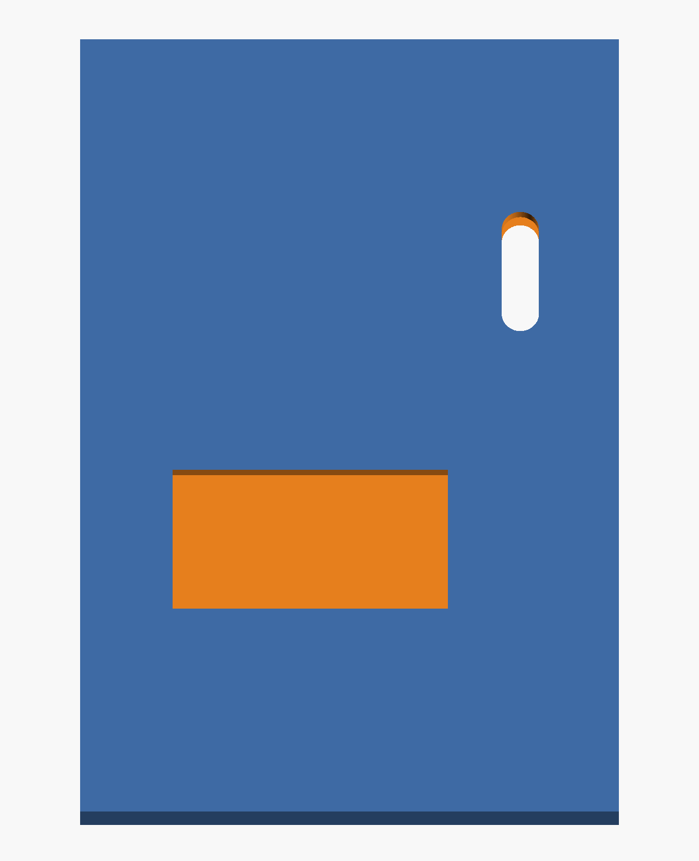
research/enclosure/bild7_deckel.png
