SphaeroX/optimistic-hubble/research/enclosure/bild9_v2_ruecken.png

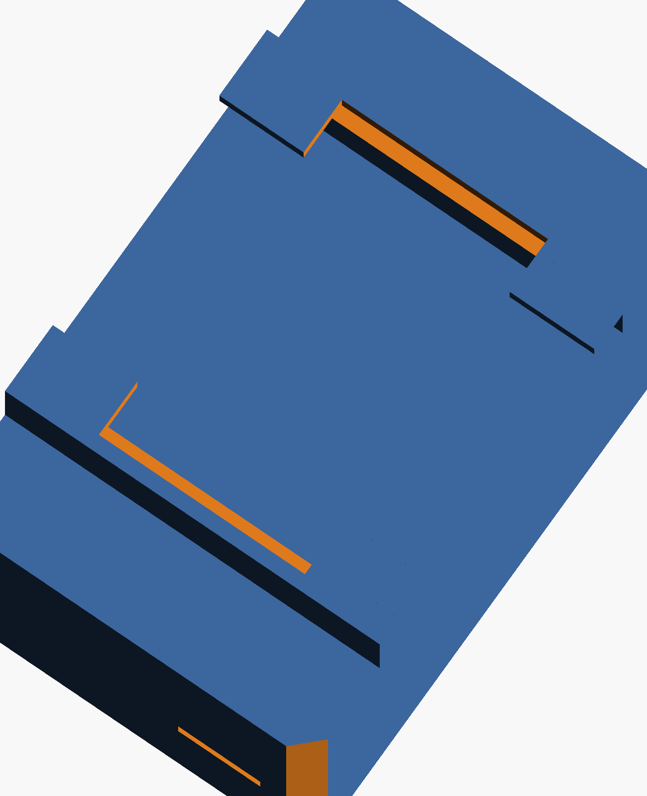
research/enclosure/bild9_v2_ruecken.png
