SphaeroX/optimistic-hubble/research/enclosure/bild11_v3_schnitt_faltung.png

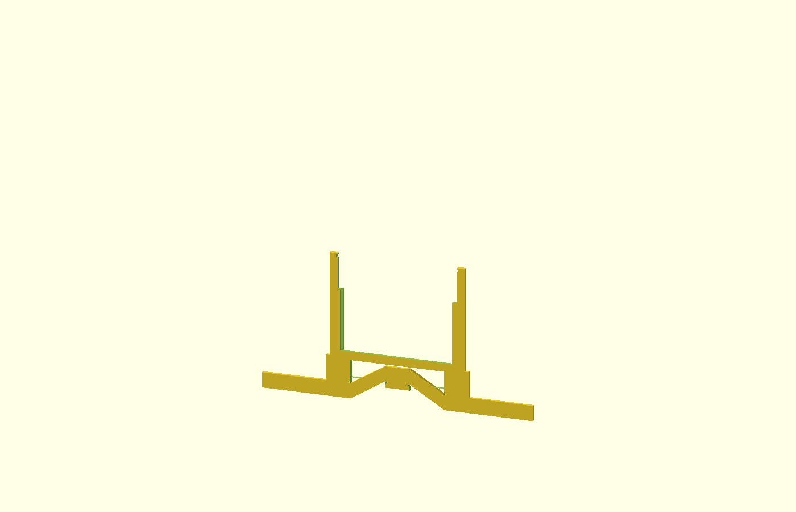
research/enclosure/bild11_v3_schnitt_faltung.png
