SphaeroX/optimistic-hubble/research/enclosure/bild12_v3_zoom_faltung.png

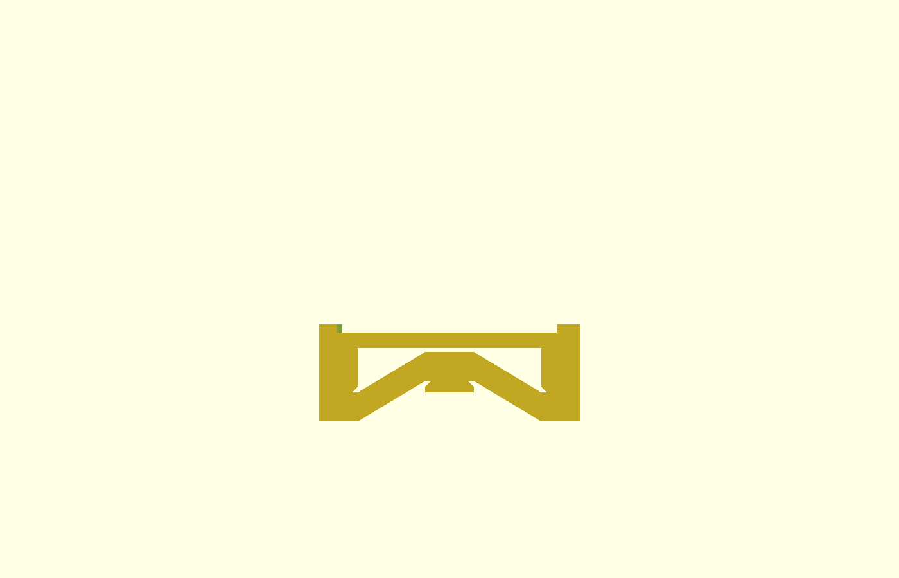
research/enclosure/bild12_v3_zoom_faltung.png
