SphaeroX/optimistic-hubble/research/enclosure/bild15_v3_slim.png

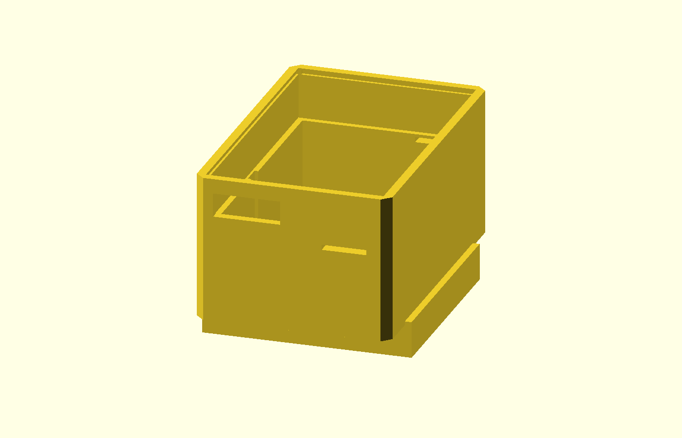
research/enclosure/bild15_v3_slim.png
