SphaeroX/optimistic-hubble/research/enclosure/bild18_v3_A_slim_band.png

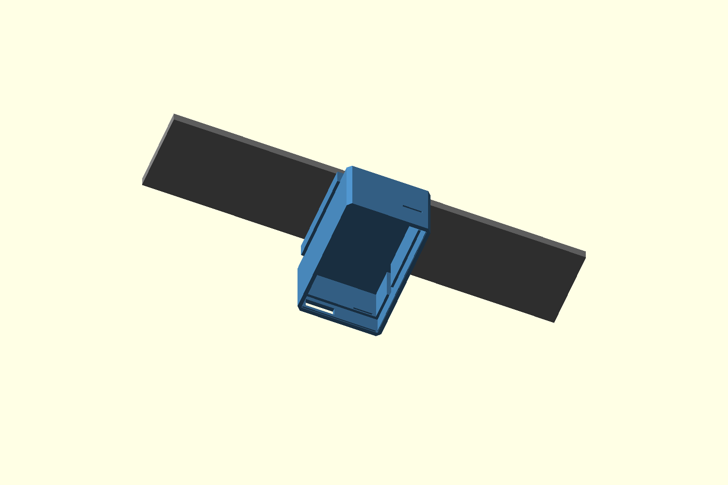
research/enclosure/bild18_v3_A_slim_band.png
