SphaeroX/optimistic-hubble/research/enclosure/bild21_v3_B_unten.png

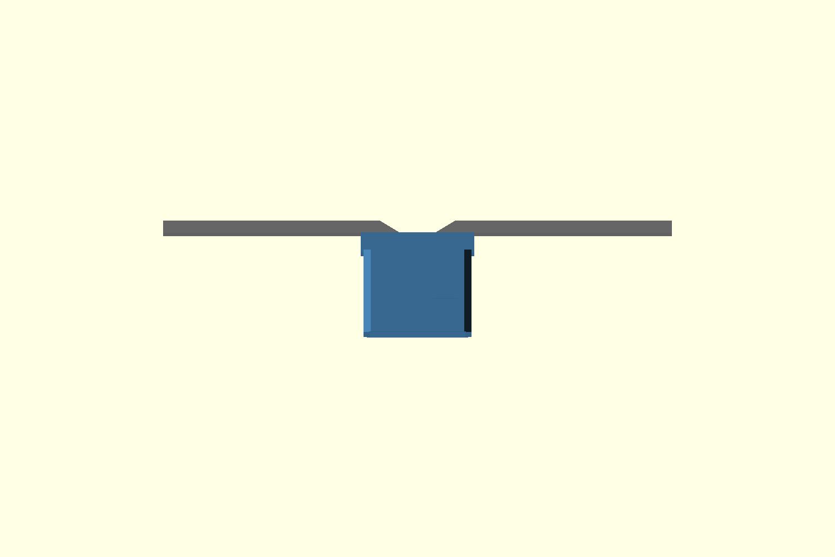
research/enclosure/bild21_v3_B_unten.png
