SphaeroX/optimistic-hubble/research/enclosure/bild22_v3_B_schnitt.png

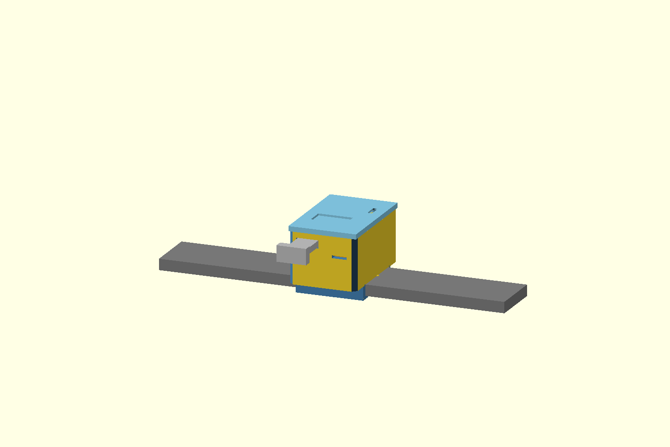
research/enclosure/bild22_v3_B_schnitt.png
