SphaeroX/optimistic-hubble/research/enclosure/bild22_v3_B_schraeg.png

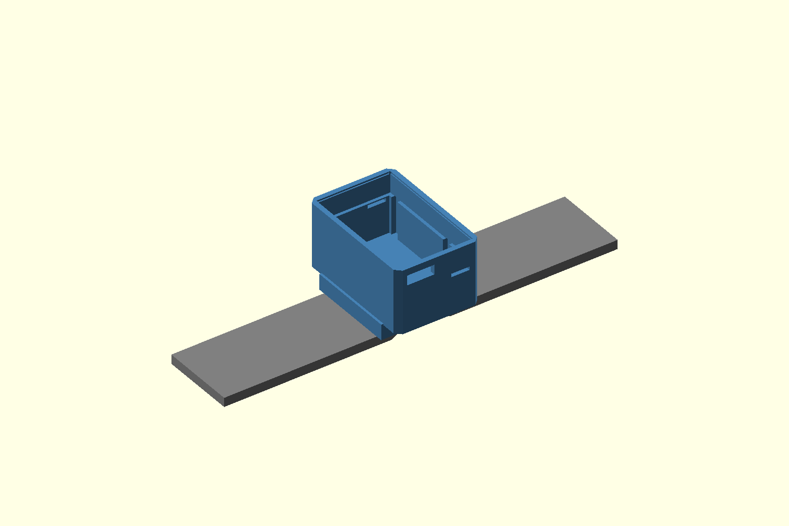
research/enclosure/bild22_v3_B_schraeg.png
