SphaeroX/optimistic-hubble/research/enclosure/cam_A.png

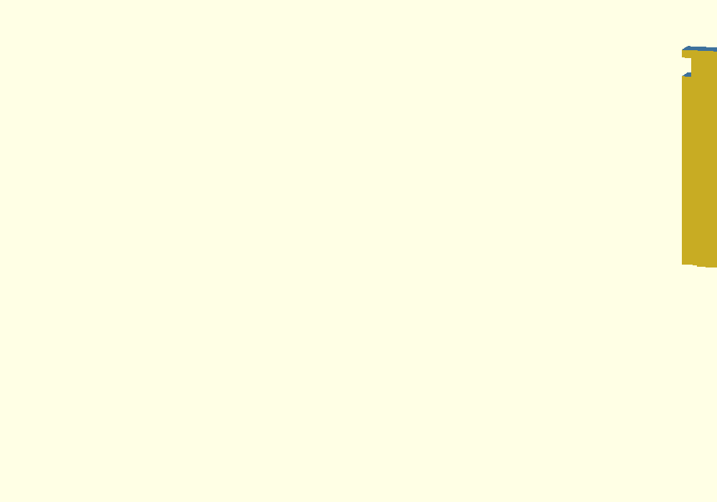
research/enclosure/cam_A.png
