SphaeroX/optimistic-hubble/research/enclosure/cam_B.png

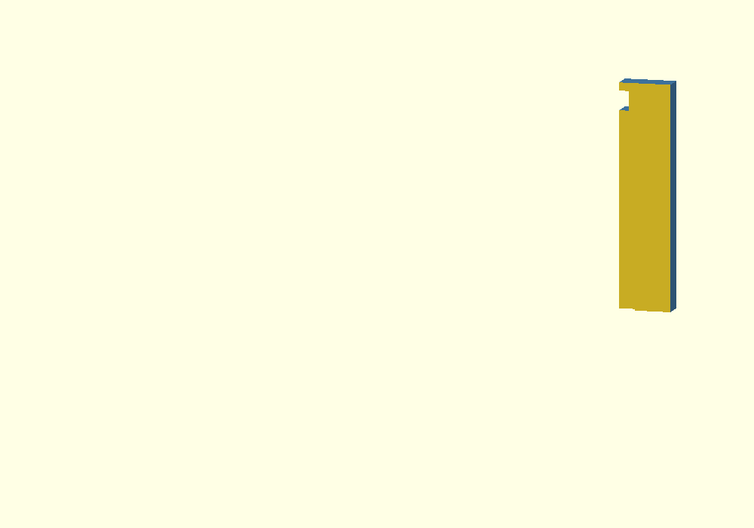
research/enclosure/cam_B.png
