SphaeroX/optimistic-hubble/research/enclosure/cam_iso.png

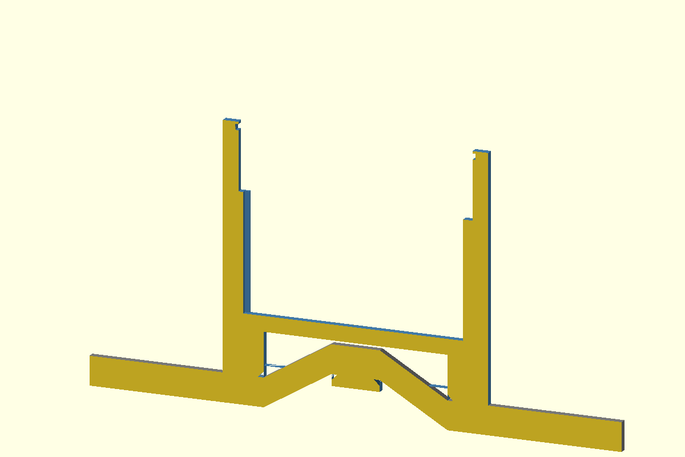
research/enclosure/cam_iso.png
