SphaeroX/optimistic-hubble/research/enclosure/t1.png

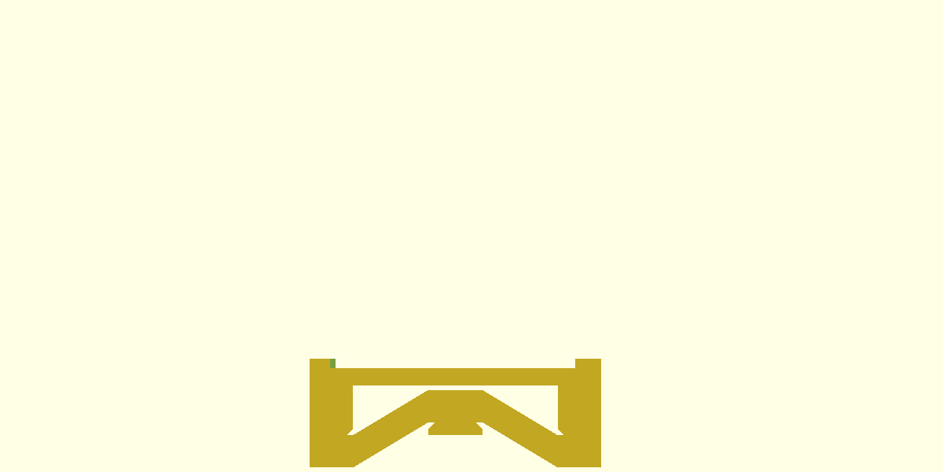
research/enclosure/t1.png
