SphaeroX/optimistic-hubble/research/enclosure/t3.png

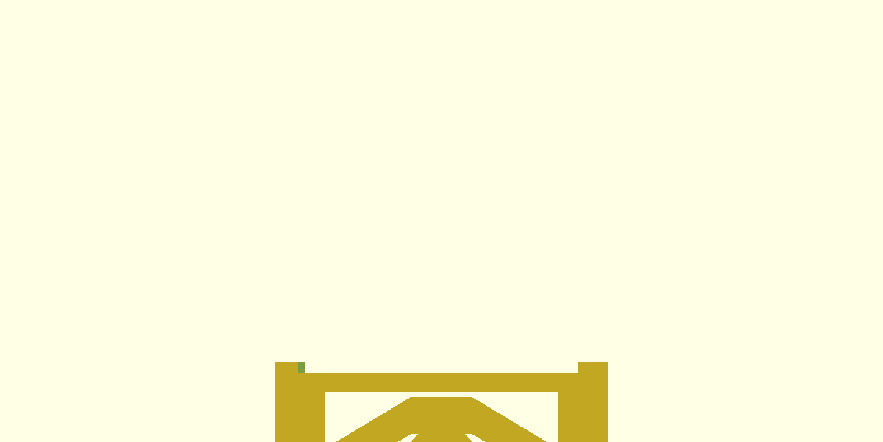
research/enclosure/t3.png
