SphaeroX/optimistic-hubble/research/enclosure/v3_offen_iso.png

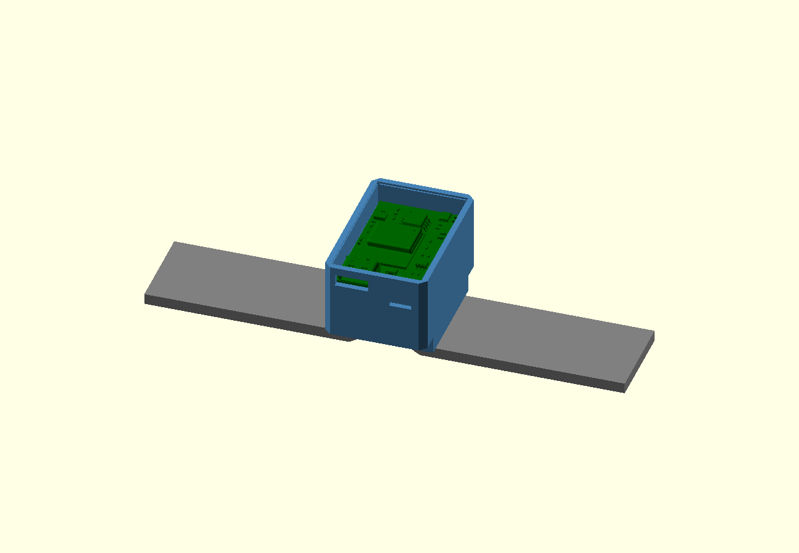
research/enclosure/v3_offen_iso.png
