SphaeroX/optimistic-hubble/research/enclosure/v3_offen_top.png

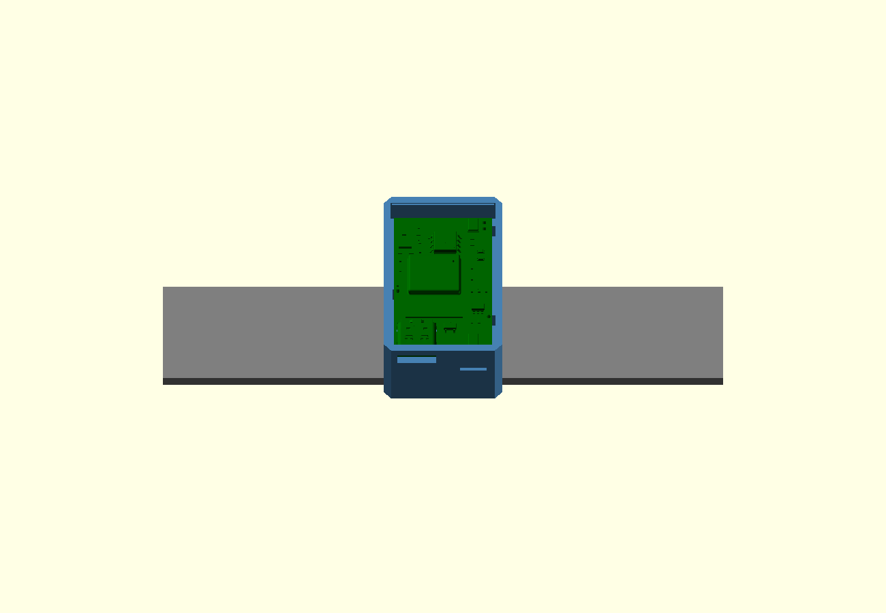
research/enclosure/v3_offen_top.png
