SphaeroX/optimistic-hubble/research/enclosure/v3r_A_closed.png

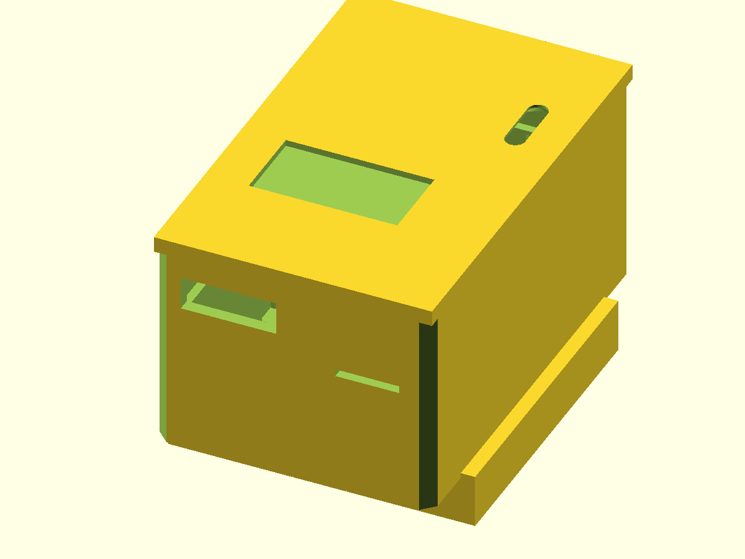
research/enclosure/v3r_A_closed.png
