SphaeroX/optimistic-hubble/research/enclosure/v3r_C_closed.png

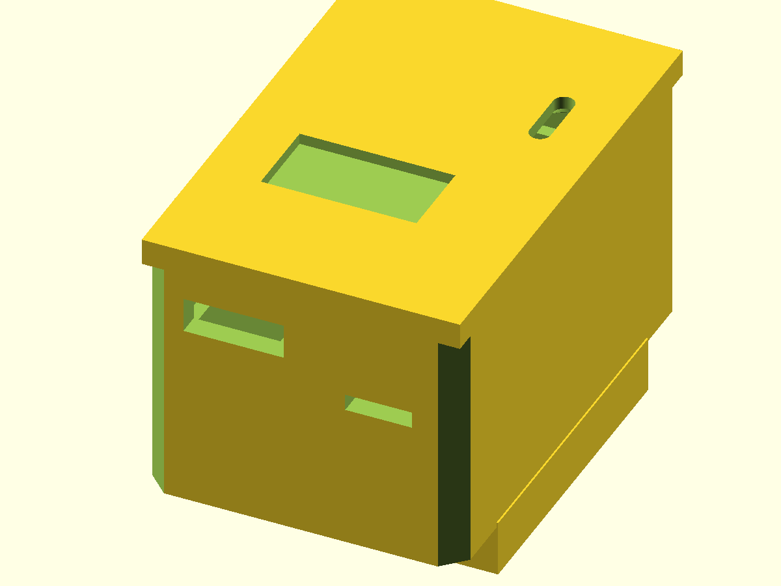
research/enclosure/v3r_C_closed.png
