SphaeroX/optimistic-hubble/research/enclosure/zz_60.png

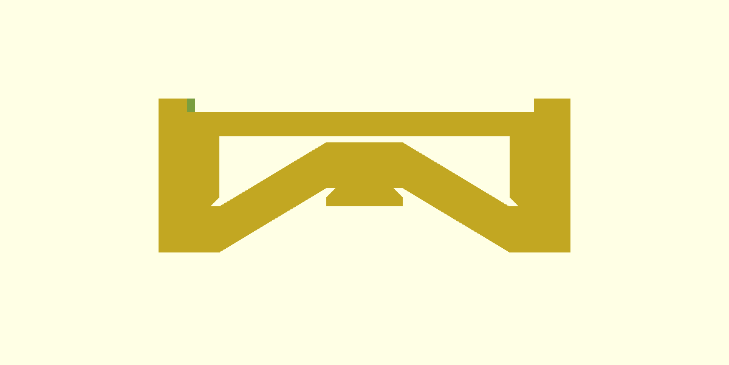
research/enclosure/zz_60.png
