SphaeroX/optimistic-hubble/research/enclosure/stl/v3_B_standard_tray.stl

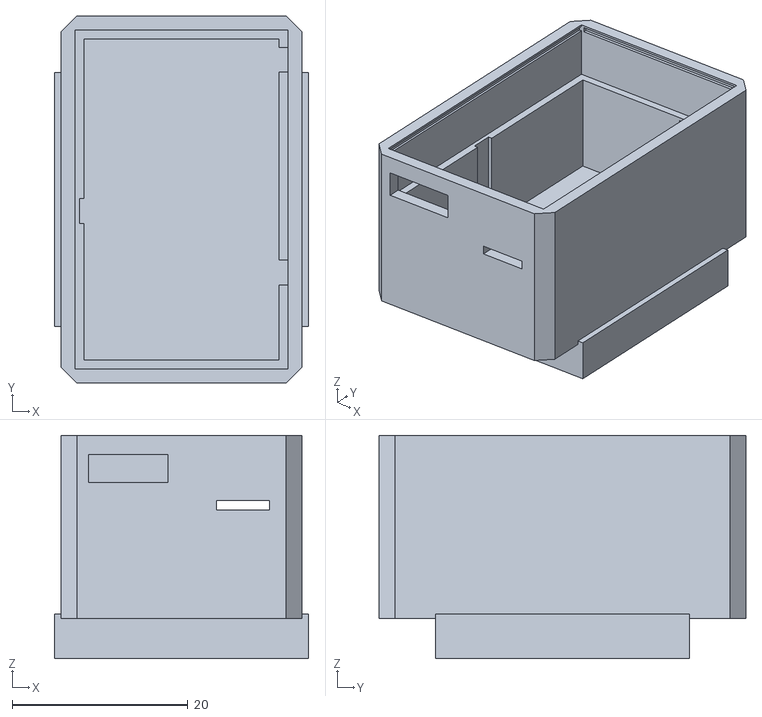
[picture p45: CAD file, 2026-09-12]
research/enclosure/stl/v3_B_standard_tray.stl
28.9 x 41.8 x 25.4
