SphaeroX/optimistic-hubble/research/enclosure/stl/v3_C_robust_tray_print.stl

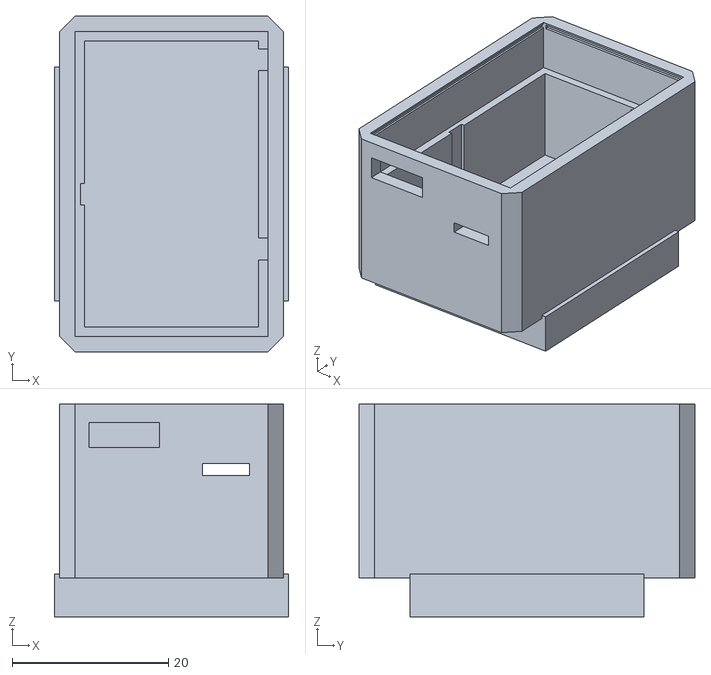
[picture p46: CAD file, 2026-09-12]
research/enclosure/stl/v3_C_robust_tray_print.stl
30.0 x 43.0 x 27.2
