SphaeroX/optimistic-hubble/research/enclosure/_scene_open.scad

color("SteelBlue") tray("cassette");
color("grey")      band_thread_mock();
