SphaeroX/optimistic-hubble/research/enclosure/zz.scad

use <audio_vault_case.scad>;
translate([1.5, -7.4, 16.9]) band_cut_fold(4, 4, -11.4);
