SphaeroX/optimistic-hubble/research/enclosure/bild1_assembly.png

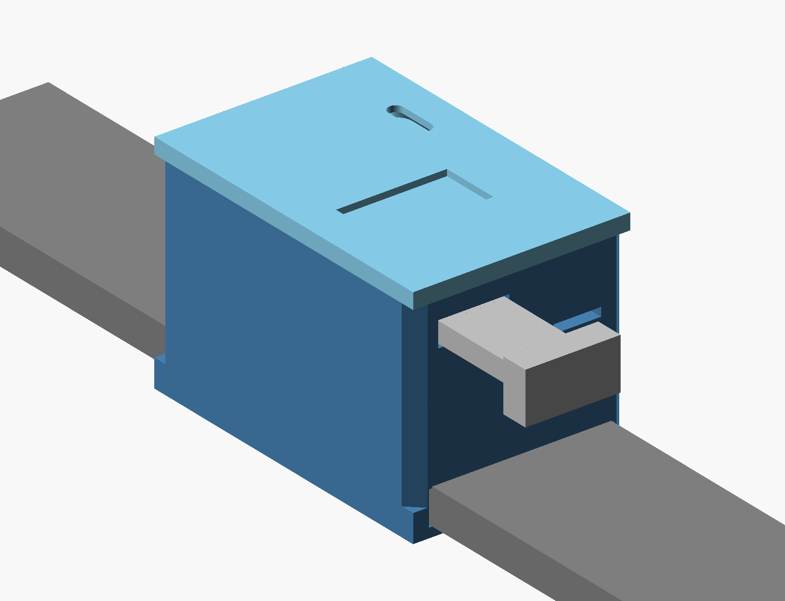
research/enclosure/bild1_assembly.png
