SphaeroX/optimistic-hubble/research/enclosure/bild8_v2_assembly.png

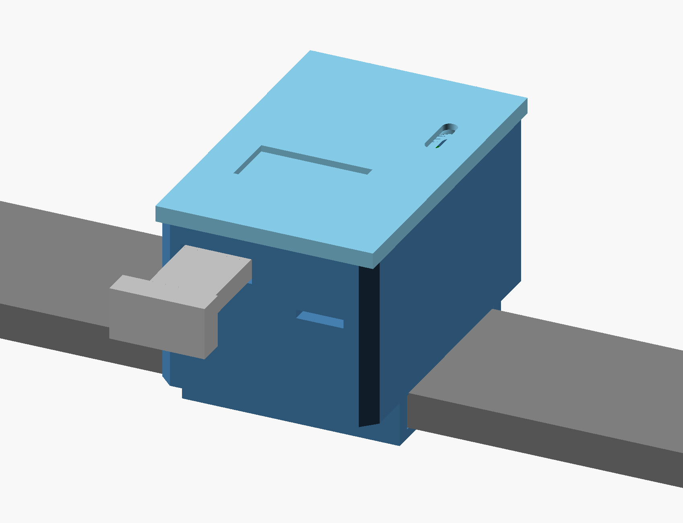
research/enclosure/bild8_v2_assembly.png
