SphaeroX/optimistic-hubble/hardware/output/xiao_voice_recorder.kicad_sch

## KiCad design hardware/output/xiao_voice_recorder.kicad_sch (2026-08-19)

Schematic: xiao_voice_recorder.kicad_sch

Parts:
C1: 4.7nF_1kV; C_0805_2012Metric
C2, C3, C4, C5, C8, C11: 10uF; C_0805_2012Metric
C6, C7, C9, C12, C13, C14, C16, C17, C18: 100nF; C_0603_1608Metric
C10, C15: 1uF; C_0603_1608Metric
D1: RED_CHRG; LED_0603_1608Metric
D2: GRN_FULL; LED_0603_1608Metric
D3: SS14_Schottky; D_SOD-123
D4: RED_RECORDING; LED_0805_2012Metric
D5: BLU_3V3_PWR; LED_0603_1608Metric
FB1: 600R_100MHz; R_0805_2012Metric
J1: TYPE-C-16P; USB_C_Receptacle_HRO_TYPE-C-31-M-12
J2: JST-PH-2P-LiPo; JST_PH_S2B-PH-K_1x02_P2.00mm_Horizontal
MK1: INMP441_LEFT; InvenSense_INMP441
MK2: INMP441_RIGHT; InvenSense_INMP441
Q1: AO3401A_P-FET; SOT-23
R1, R2: 5.1k_1%; R_0603_1608Metric
R3: 1M; R_0805_2012Metric
R4: 2.4k_1%; R_0603_1608Metric
R5, R6, R18: 1k; R_0603_1608Metric
R7: 100k; R_0603_1608Metric
R8, R9: 100k_1%; R_0603_1608Metric
R10, R11, R14, R15, R16: 10k; R_0603_1608Metric
R12, R13: 4.7k; R_0603_1608Metric
R17: 330R; R_0805_2012Metric
SW1: POWER_SWITCH; SW_SPDT_PCM12
SW2: RESET_BTN; SW_SPST_PTS645
SW3: BOOT_BTN; SW_SPST_PTS645
TP1: TP_3V3; TestPoint_Pad_D1.0mm_OD2.0mm
TP2: TP_GND; TestPoint_Pad_D1.0mm_OD2.0mm
TP3: TP_EN; TestPoint_Pad_D1.0mm_OD2.0mm
TP4: TP_IO9; TestPoint_Pad_D1.0mm_OD2.0mm
TP5: TP_USB_DP; TestPoint_Pad_D1.0mm_OD2.0mm
TP6: TP_USB_DN; TestPoint_Pad_D1.0mm_OD2.0mm
TP7: TP_VBAT; TestPoint_Pad_D1.0mm_OD2.0mm
U1: USBLC6-2SC6; SOT-23-6
U2: TP4056; SOP-8-PP_3.9x4.9mm_P1.27mm_EP
U3: AP2112K-3.3; SOT-23-5
U4: ESP32-C3-WROOM-02-N4; ESP32-C3-WROOM-02
U5: LSM6DS3TR-C; LGA-14_3x2.5mm_P0.5mm_LayoutBorder1x6y
U6: W25Q128JV_16MB; SOIC-8_5.23x5.23mm_P1.27mm

Notes on the sheet:
1. POWER MANAGEMENT & BATTERY CHARGER (USB-C, TP4056, POWER-PATH, 3.3V LDO)
2. ESP32-C3 CORE MICROCONTROLLER (WROOM-02, RESET, BOOT, USB D+/D-)
3. DUAL I2S MEMS MICROPHONES (STEREO NOISE CANCELLATION)
4. 6-AXIS IMU (LSM6DS3 TAP DETECTOR)
5. 16MB SPI FLASH STORAGE (W25Q128)
6. STATUS INDICATORS & TEST PADS
